alper-bozcal/75W_XDPS/ENKO/Canbus/DBC2 Canbus List.pdf

J1939-71

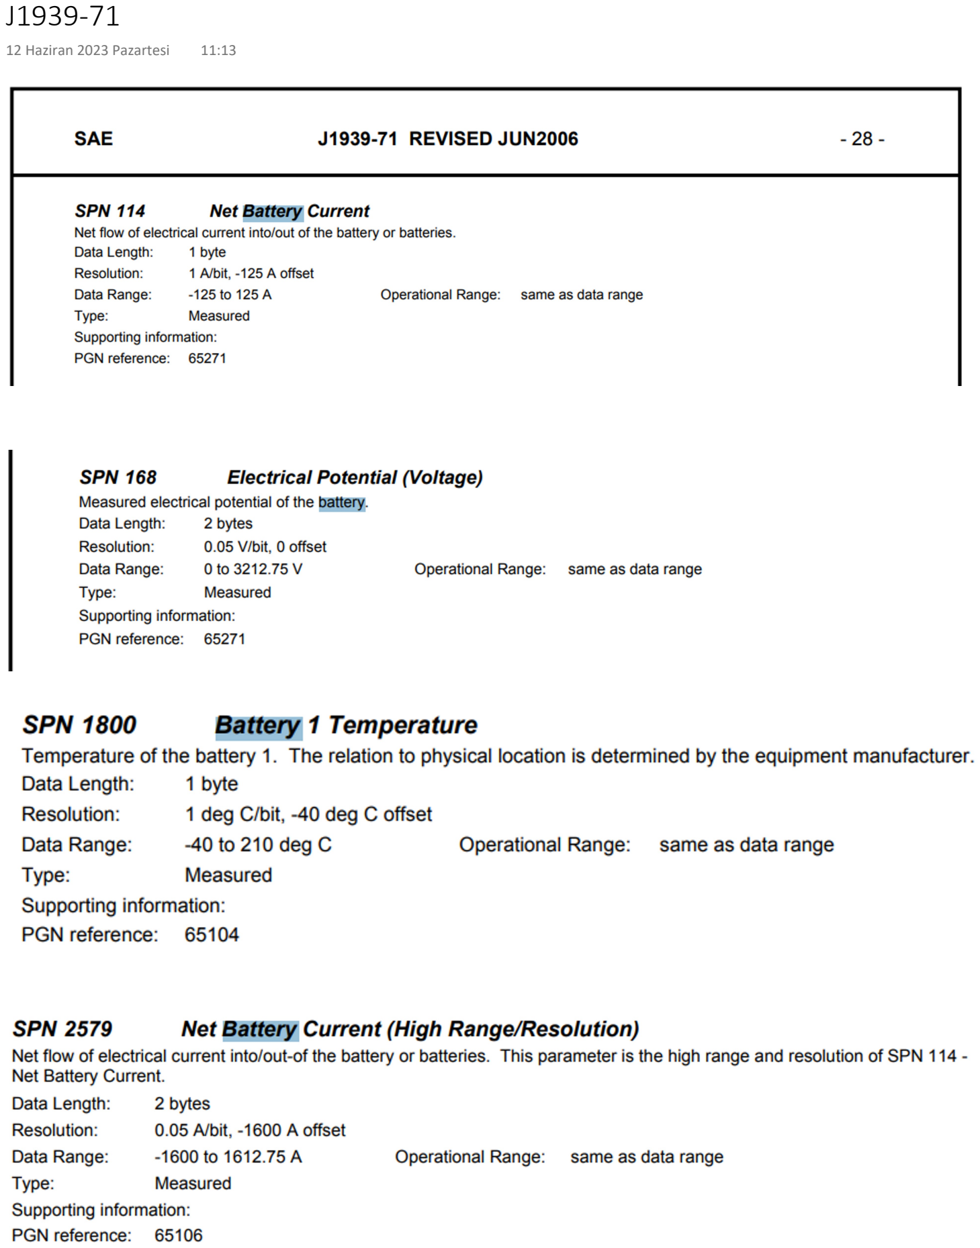
[picture p2: page 1]

### 12 Haziran 2023 Pazartesi 11:13

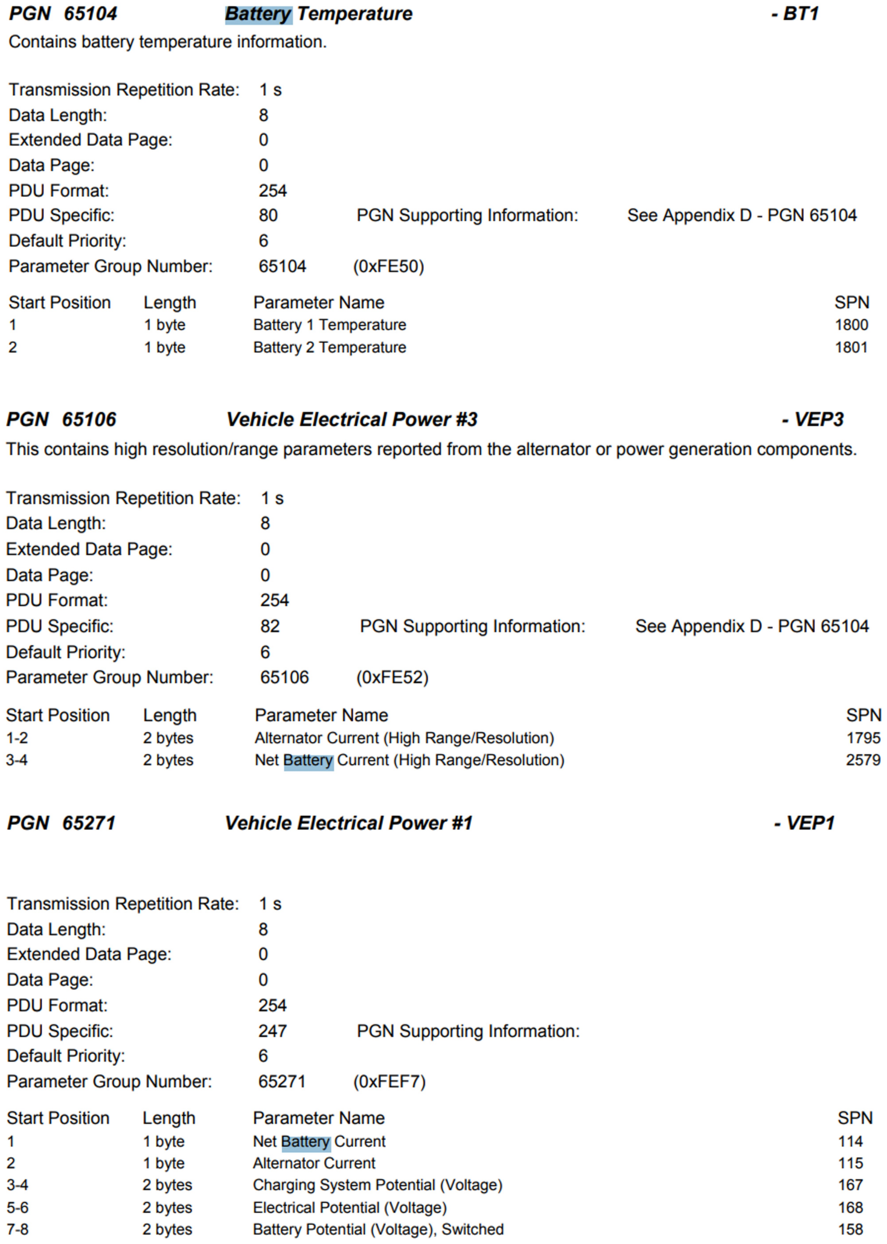
[picture p3: page 2]
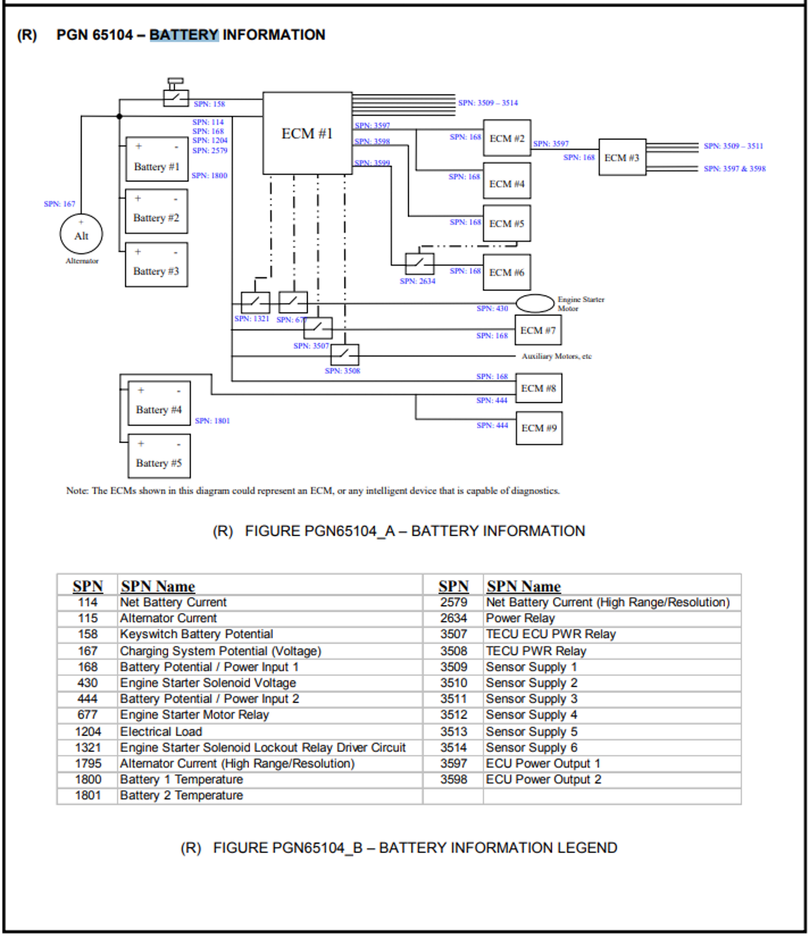
[picture p4: page 3]
