alper-bozcal/75W_XDPS/Design Docs/300W 894 Core Hesapları.PNG

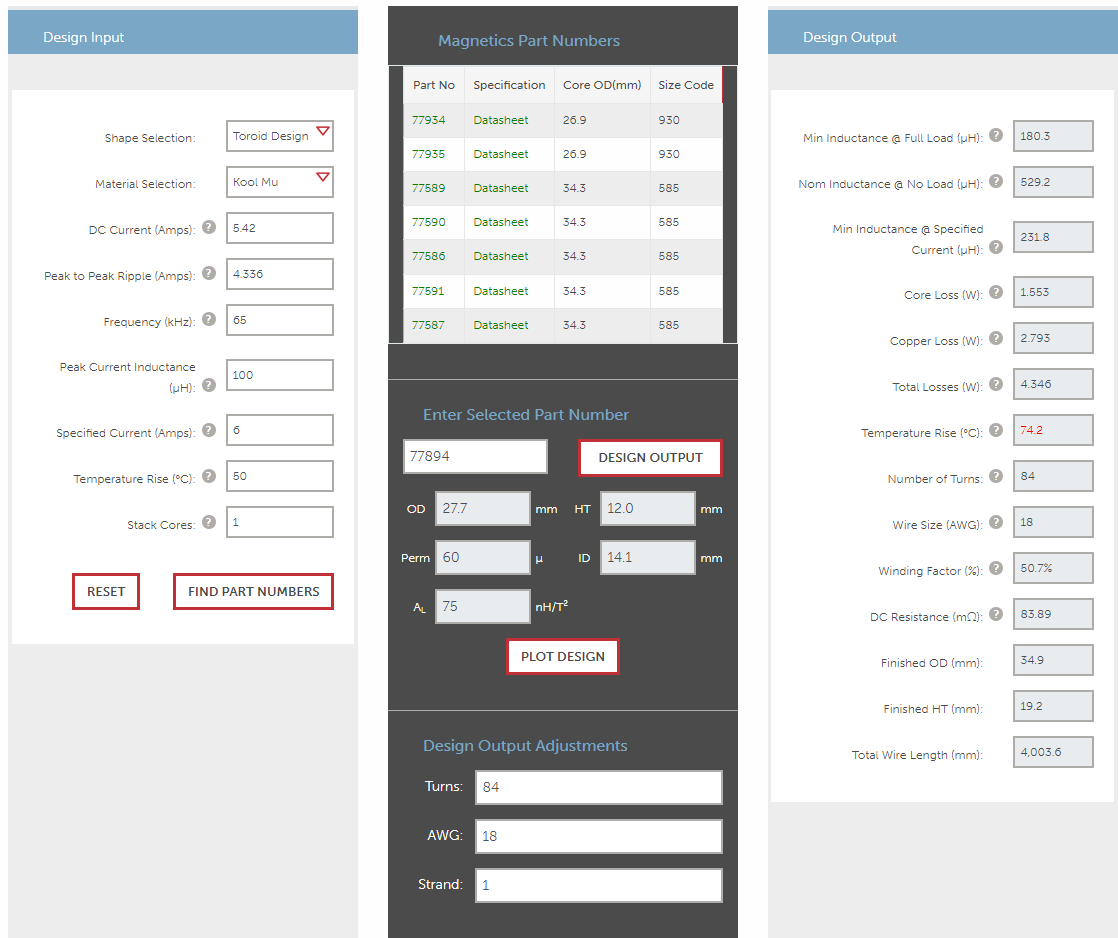
Design Docs/300W 894 Core Hesapları.PNG
