alper-bozcal/75W_XDPS/Design Docs/300W 77083 Bütün Sınırlara Uyan.PNG

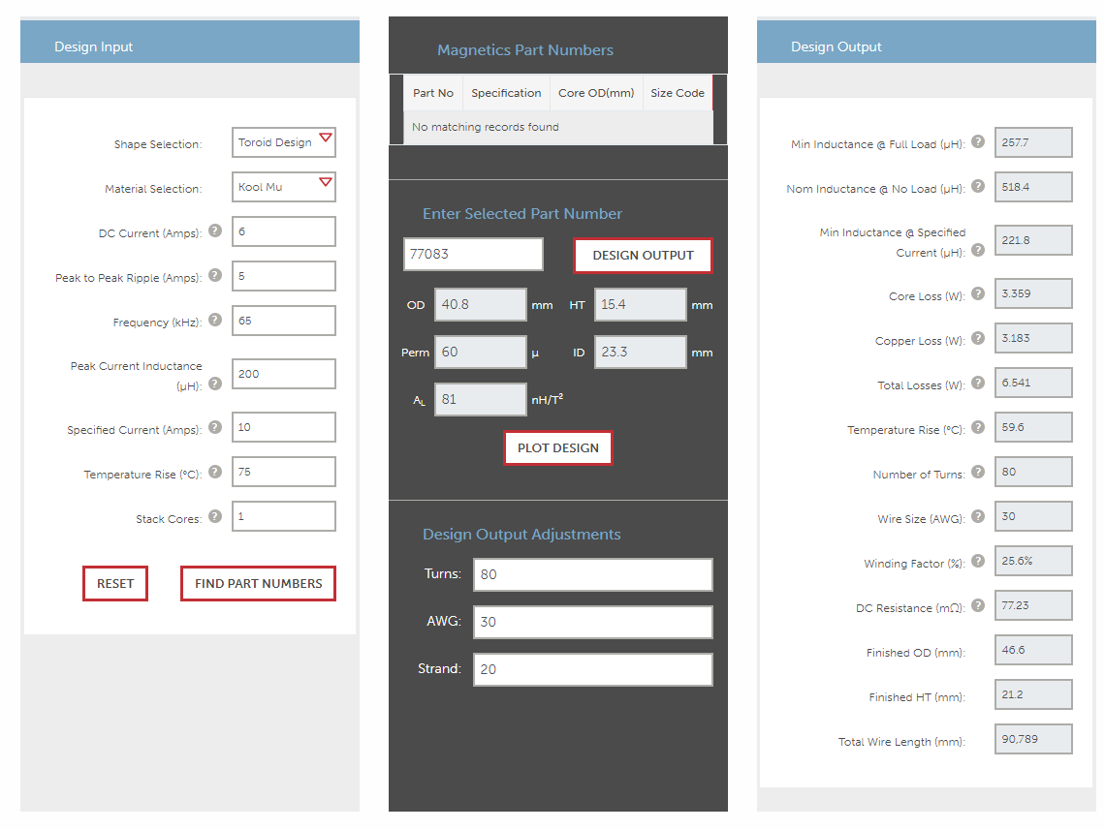
Design Docs/300W 77083 Bütün Sınırlara Uyan.PNG
