alper-bozcal/75W_XDPS/Simulations/Leakage/90W leakeage/90W-220VAC-LEAKAGE.PNG

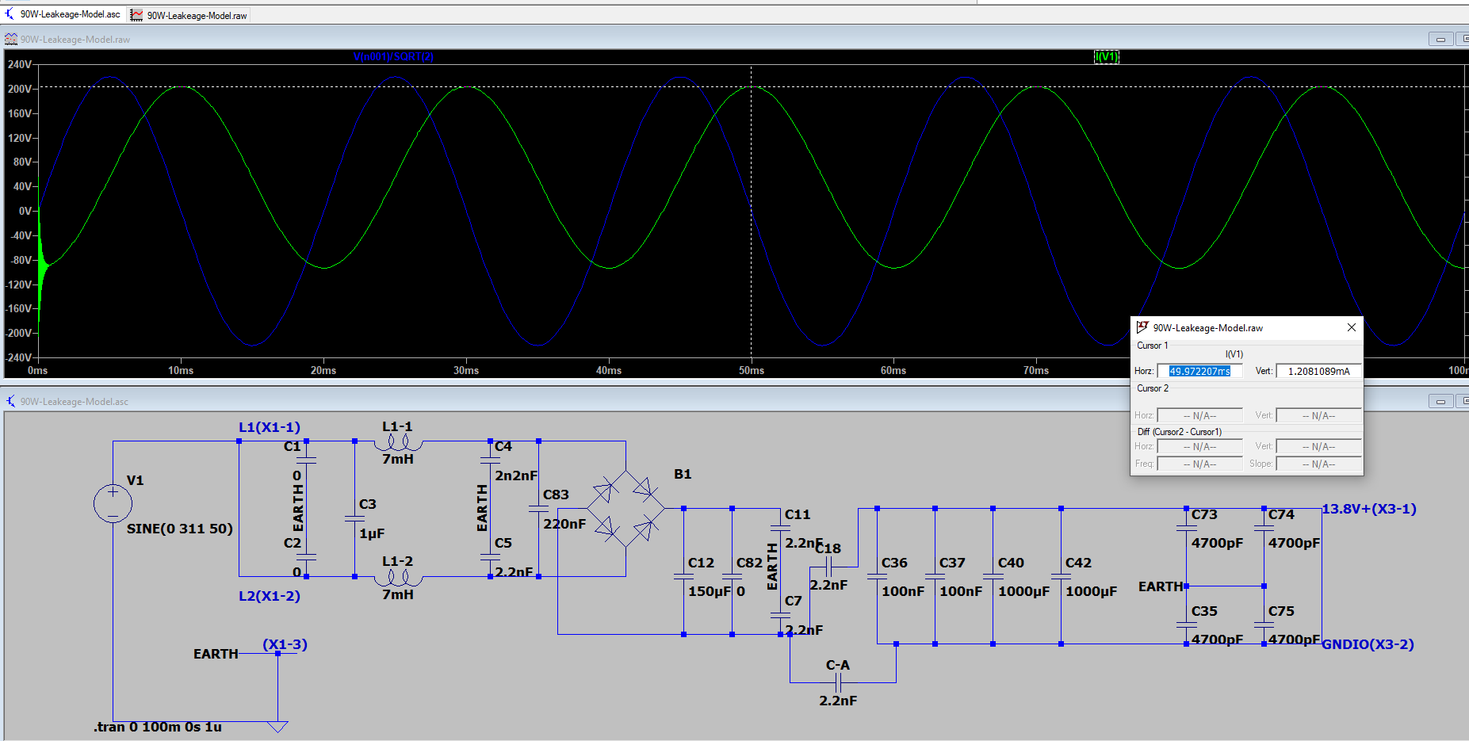
Simulations/Leakage/90W leakeage/90W-220VAC-LEAKAGE.PNG
