alper-bozcal/75W_XDPS/Simulations/Leakage/90W leakeage/90W-264VAC-LEAKAGE.PNG

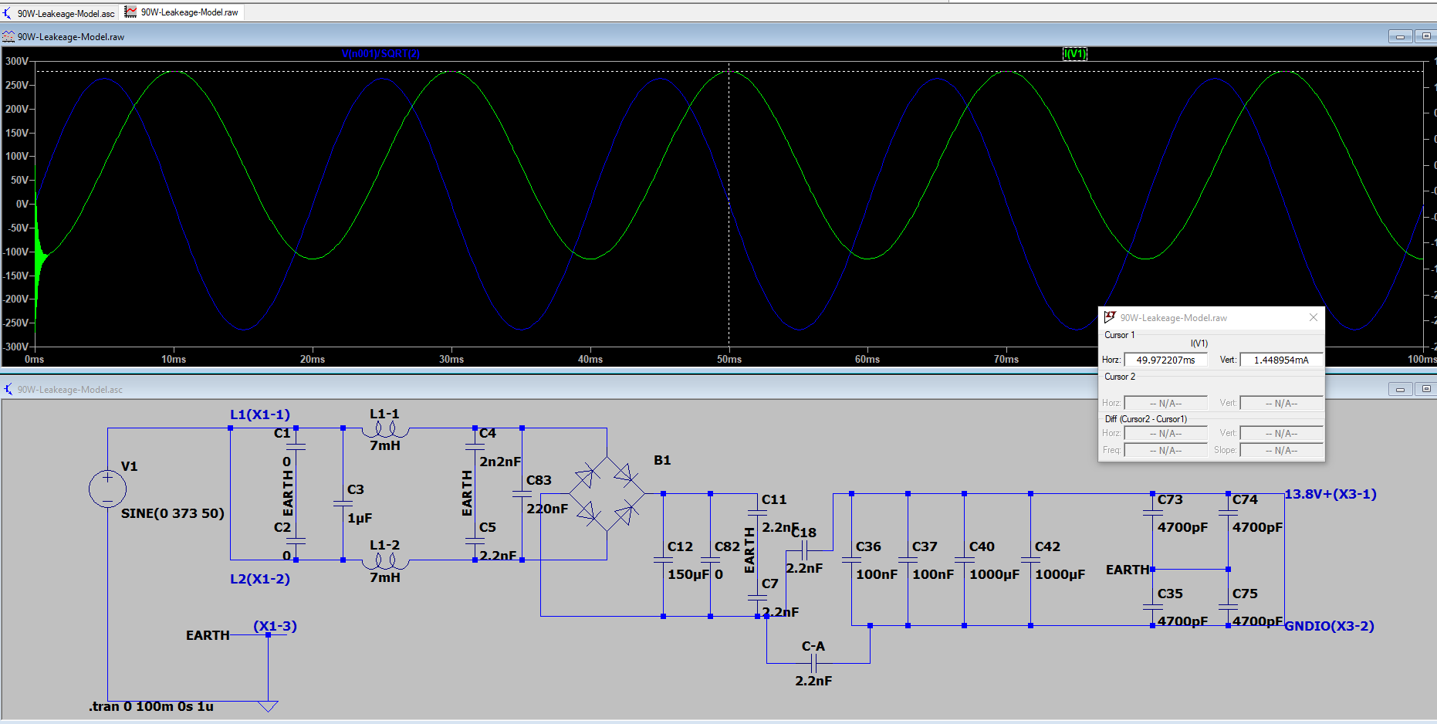
Simulations/Leakage/90W leakeage/90W-264VAC-LEAKAGE.PNG
