alper-bozcal/75W_XDPS/Simulations/Leakage/150W leakeage/150W-85VAC-Leakeage.PNG

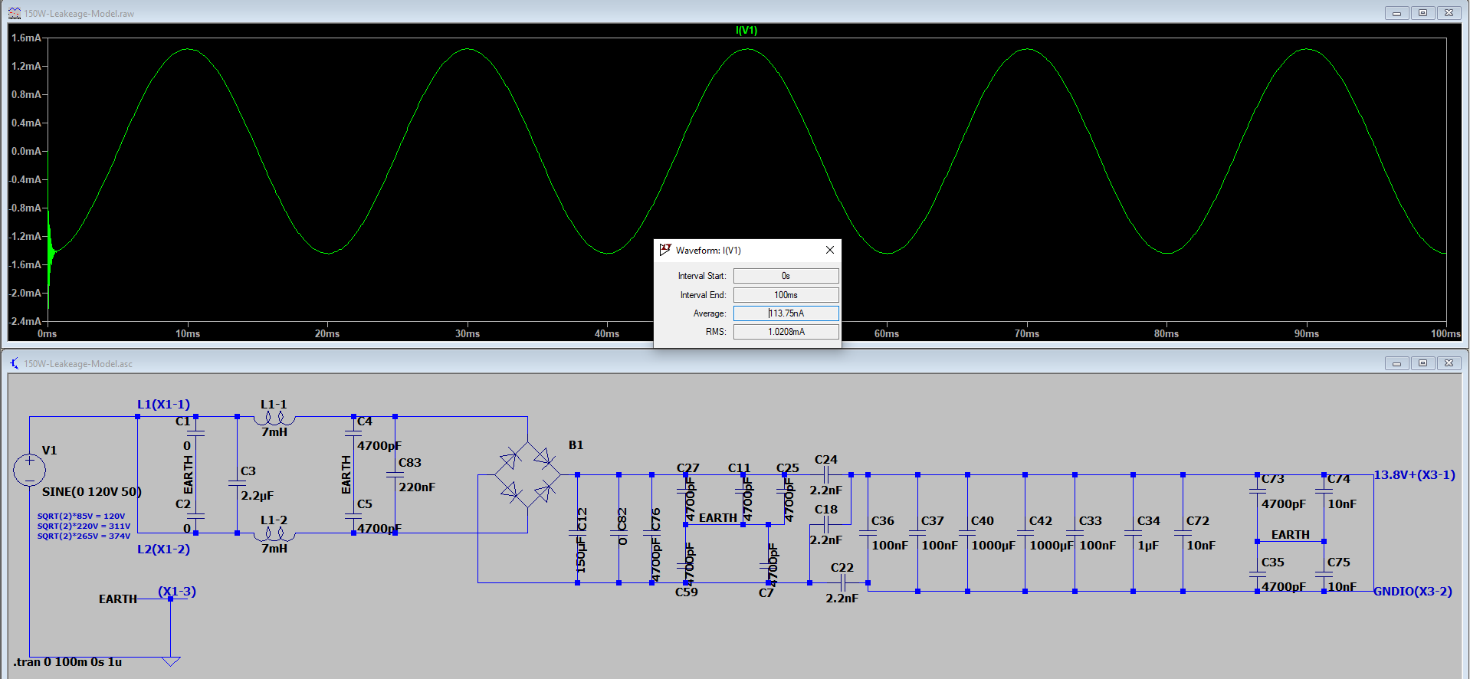
Simulations/Leakage/150W leakeage/150W-85VAC-Leakeage.PNG
