alper-bozcal/75W_XDPS/Simulations/Leakage/300W leakeage/300W 85VAC Leakeage.PNG

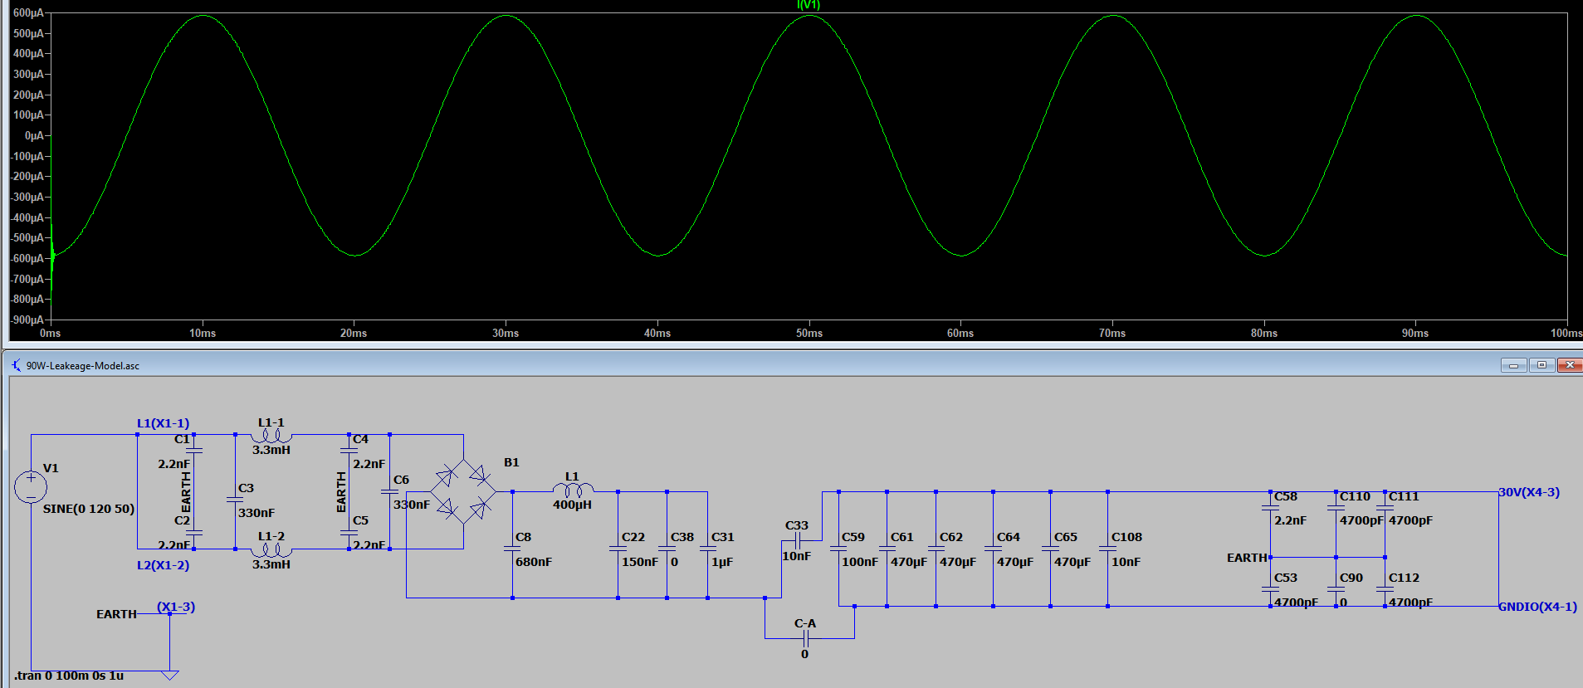
Simulations/Leakage/300W leakeage/300W 85VAC Leakeage.PNG
