alper-bozcal/75W_XDPS/Tests/EMC/2023 01 17 VESTEL/TEST18-2A_FULL.Rtf

TEST18-2A_FULL

Common Information
Test Description:
Test Site: | SAC3
Test Standard:
Environment Conditions:
Operator Name:
Comment:

Final_Result
Frequency (MHz) | QuasiPeak (dBµV/m) | Limit (dBµV/m) | Margin (dB) | Meas. Time (ms) | Bandwidth (kHz) | Height (cm) | Pol | Azimuth (deg)
30.570000 | 32.75 | 40.00 | 7.25 | 1000.0 | 120.000 | 100.0 | V | 165.0
40.260000 | 32.58 | 40.00 | 7.42 | 1000.0 | 120.000 | 100.0 | V | 18.0
44.760000 | 33.35 | 40.00 | 6.65 | 1000.0 | 120.000 | 100.0 | V | 120.0
74.940000 | 29.49 | 40.00 | 10.51 | 1000.0 | 120.000 | 160.0 | V | 225.0
222.360000 | 38.35 | 40.00 | 1.65 | 1000.0 | 120.000 | 100.0 | H | 114.0
223.650000 | 37.09 | 40.00 | 2.91 | 1000.0 | 120.000 | 105.0 | H | 103.0
Hardware Setup: EMI radiated\SAC3 Radiated Emission 30-6000 MHz - [EMI radiated] Subrange 1
| Frequency Range: | 30 MHz - 6 GHz
| Receiver: | ESW 44 [ESW 44]
| | @ GPIB0 (ADR 20), SN 1328.4100K45/103131, FW 2.10SP2
| Signal Path: | ESR 7-ETS-Lindgren 3142E
| | FW 1.0
| | Correction Table: EMI+ANTENNA_CABLE_30MHz-6GHz_26.08.2022
| Antenna: | ETS-Lindgren 3142E
| | Correction Table (vertical): ETS_LINDGREN_3142E_HORIZONTAL_18.08.2020
| | Correction Table (horizontal): ETS_LINDGREN_3142E_HORIZONTAL_18.08.2020
| Antenna Tower: | EMCO 2090 Antenna Tower [EMCO 2090 Antenna Tower]
| | @ GPIB0 (ADR 8), FW REV 3.21
| Turntable: | EMCO Turntable [EMCO Turntable]
| | @ GPIB0 (ADR 9), FW REV 3.21
EMI Auto Test Template: SAC3 EN 55032 CLASS B 30-1000 MHz TEST
Hardware Setup: | SAC3 Radiated Emission 30-6000 MHz
Measurement Type: | Open-Area-Test-Site
Frequency Range: | 30 MHz - 1 GHz
Graphics Level Range: | 0 dBµV/m - 80 dBµV/m
Preview Measurements:
| Graphics Display: | Show separate traces for horizontal and vertical polarization
| Scan Test Template: | SAC2 TV EN 55022 ITE Equipments Prescan
Adjustment:
| Template for Single Meas.: | SAC2 TV EN 55022 ITE Equipments Final Measurement
Final Measurements:
| Template for Single Meas.: | SAC2 TV EN 55022 ITE Equipments Final Measurement
