alper-bozcal/75W_XDPS/Tests/EMC/2023 05 23 Vestel RE CE Harmonics/DBC2 75W&150W VESTEL Tests.odt

DBC-2

75W & 150W

CONDUCTED – HARMONICS – RADIATED

Tests @Vestel

23.05.2023

Following tests hold for DBC 2 75W and 150W units accordingly. All images have labels to indicate which sample tested. For 150W tests ENKO Unit 150W-4 used. For 75W tests, ENKO Unit 1205-A used.

CONDUCTED EMISSIONS TESTS

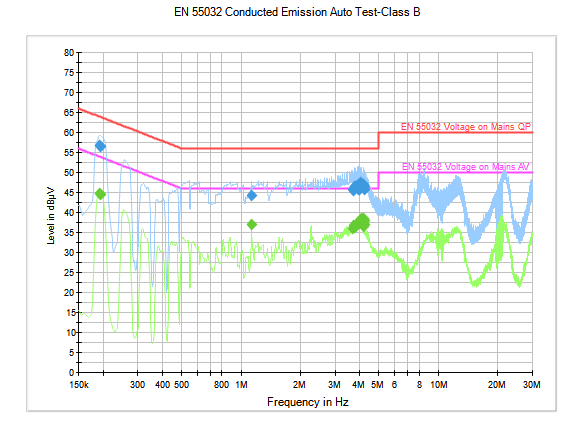
[picture p43: figure]

Image 1 – 150W-4 15VDC 10ADC Tests @Vestel

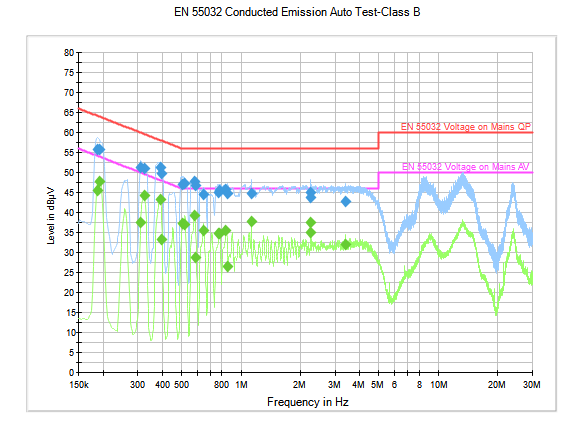
[picture p44: figure]

Image 2 - 150W-4 30VDC 5ADC Tests @Vestel

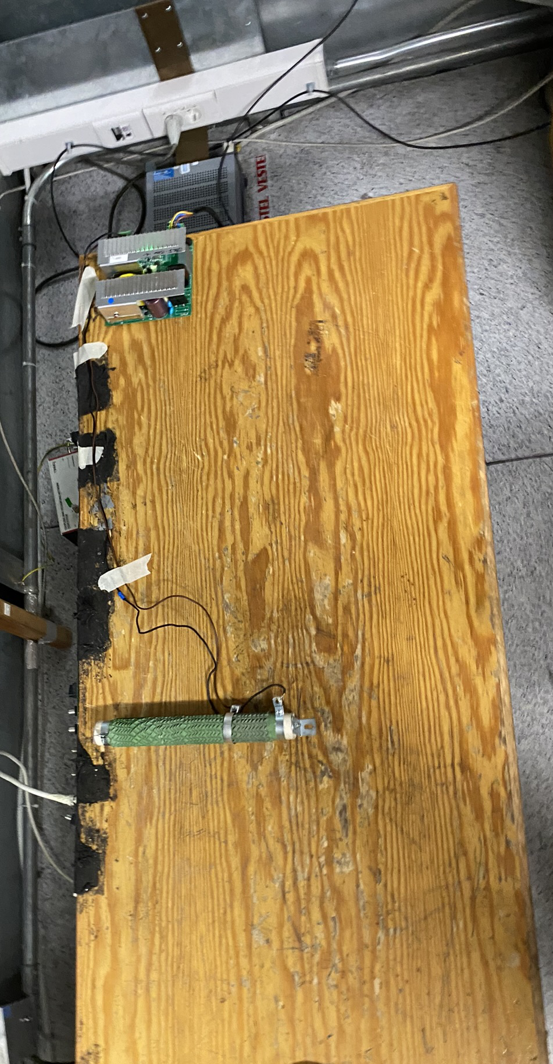
[picture p45: figure]

Image 3 – 150W-4 Conducted Test Setup @Vestel

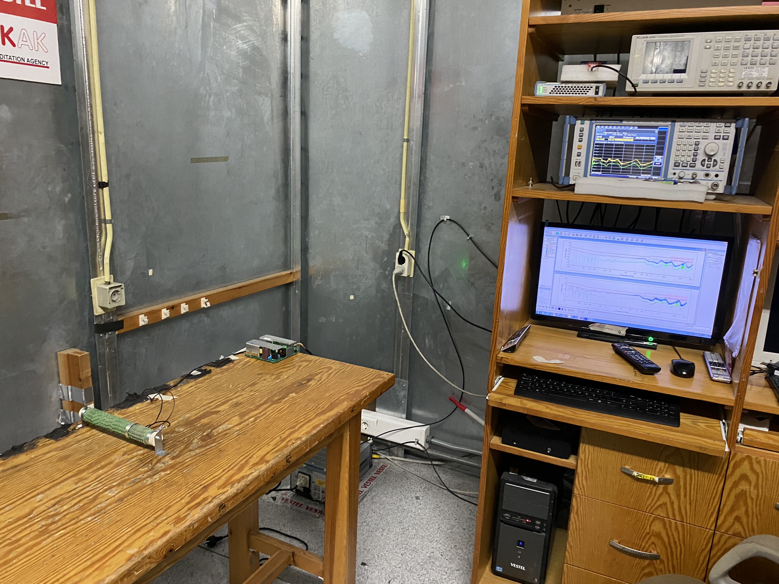
[picture p46: figure]

Image 4 – 150W-4 Conducted Test Setup @Vestel

Line Current Harmonics Tests

Harmonics tests at Vestel were according to standard: EN/IEC 61000-3-2 Ed.4 Long cyclic, Class A.

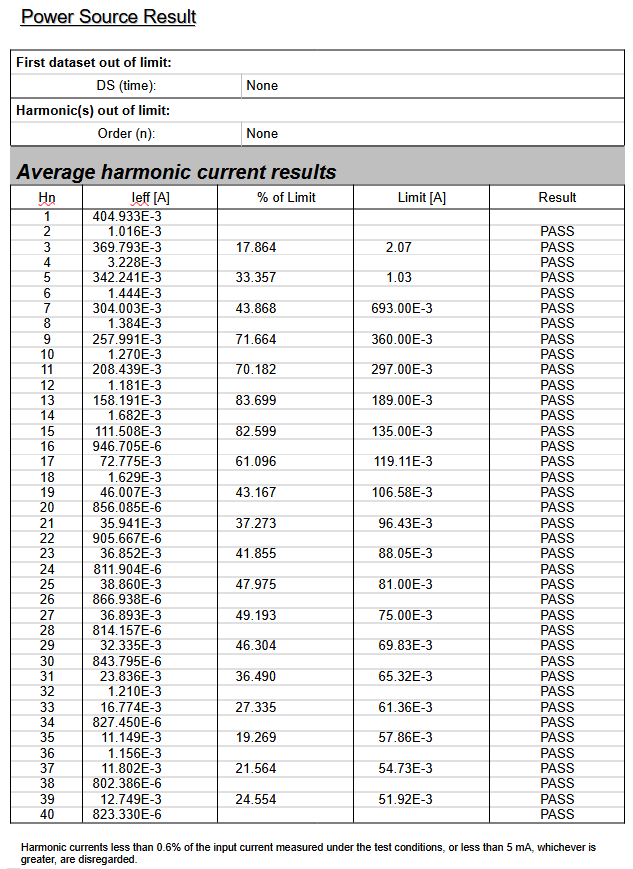
[picture p47: figure]

Image 5 – 1205-A 15VDC 05ADC Harmonics Test Average Results @Vestel

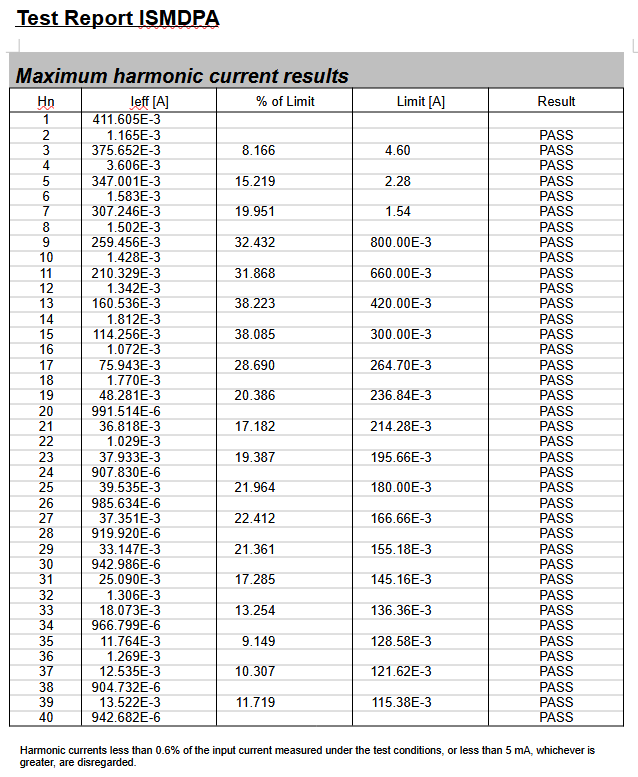
[picture p48: figure]

Image 6 – 1205-A 15VDC 05ADC Harmonics Test Maximum Results @Vestel

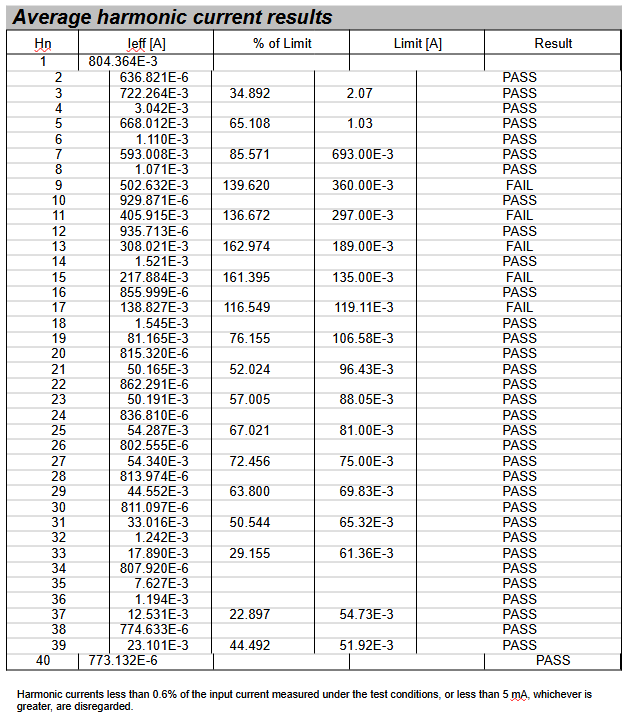
[picture p49: figure]

Image 7 – 150W-4 15VDC 10ADC Average Current Harmonics Test @Vestel

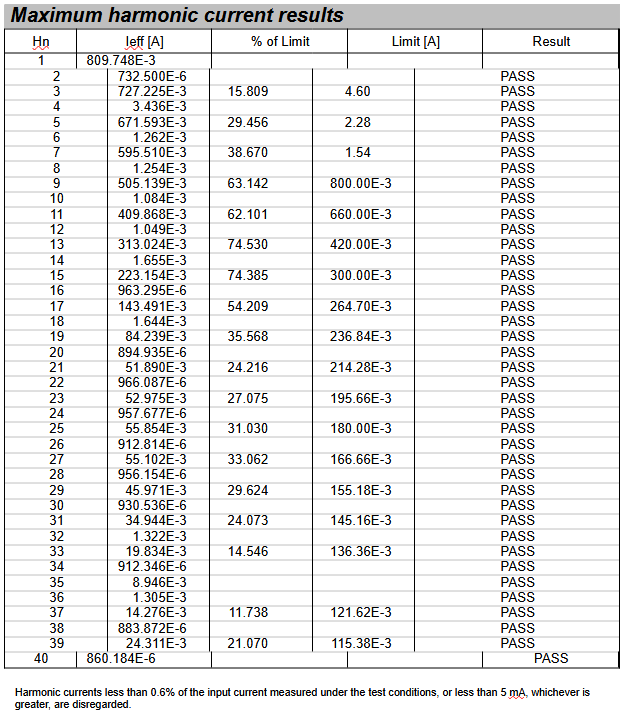
[picture p50: figure]

Image 8 – 150W-4 15VDC 10ADC Maximum Current Harmonics Test @Vestel

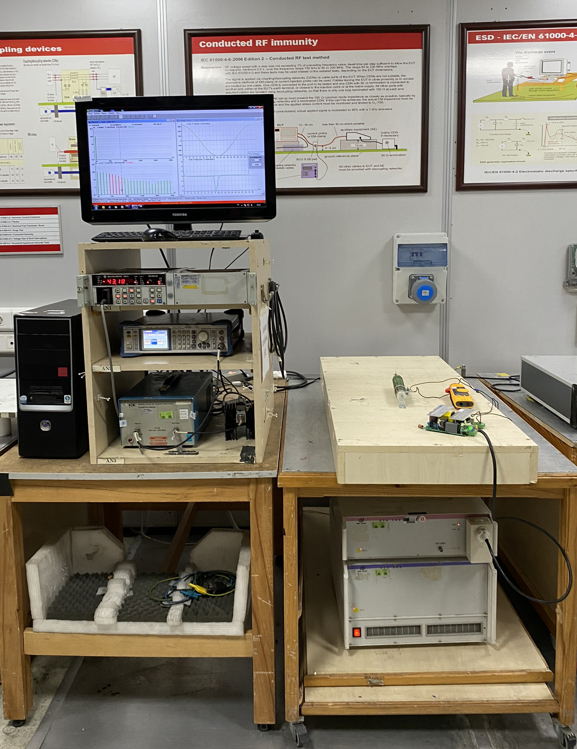
[picture p51: figure]

Image 9 – Harmonics Current Measurement Tests Setup @Vestel

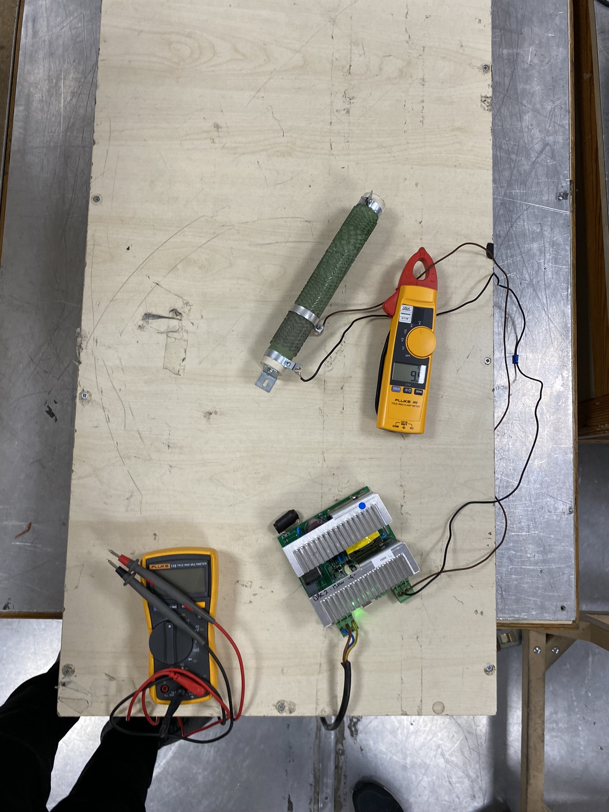
[picture p52: figure]

Image 10 - Harmonics Current Measurement Tests Setup @Vestel

Radiated Emissions Tests

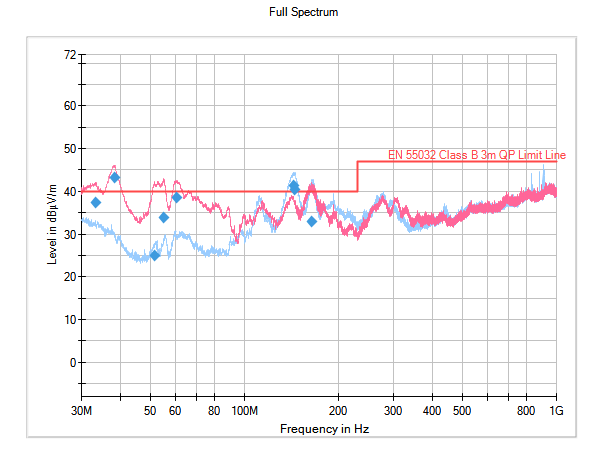
[picture p53: figure]

Image 11 – 150W-4 15VDC 10ADC T1 Radiated Test @Vestel

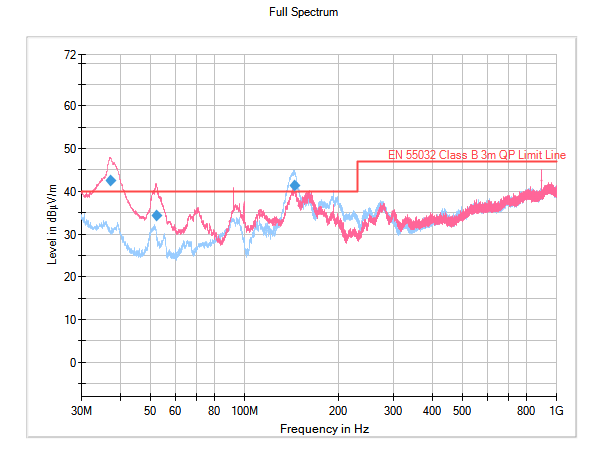
[picture p54: figure]

Image 12 – 150W-4 15VDC 10ADC T2 Radiated Test @Vestel

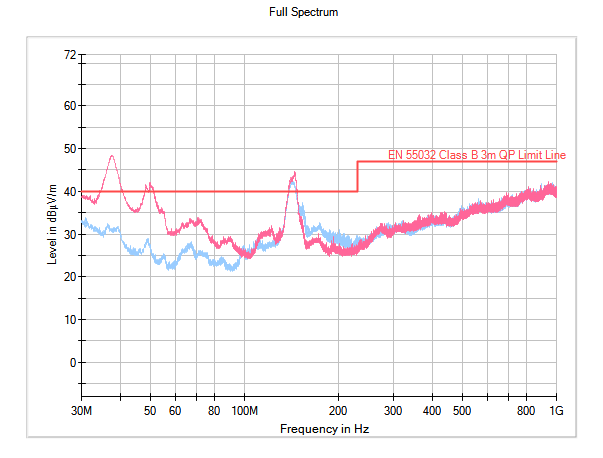
[picture p55: figure]

Image 13 – 150W-4 15VDC 10ADC T3 Radiated Test @Vestel

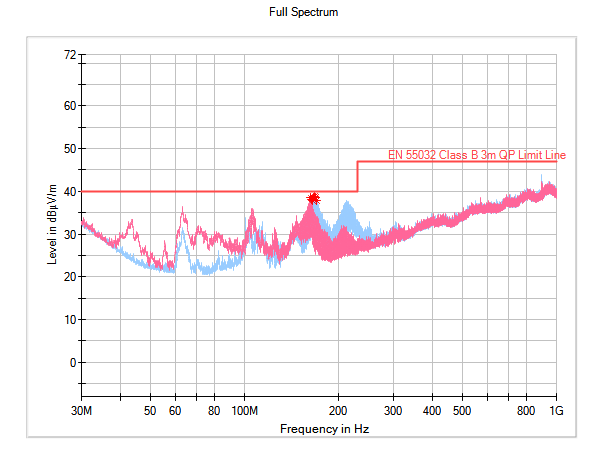
[picture p56: figure]

Image 14 – 150W-4 15VDC 10ADC T4 Radiated Test @Vestel

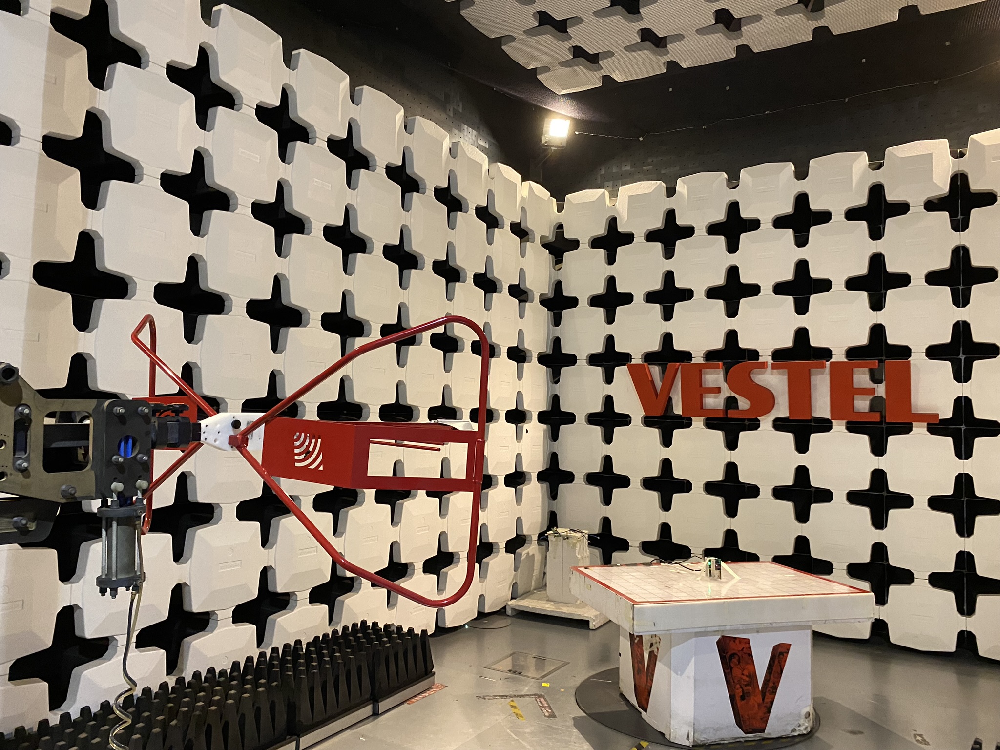
[picture p57: figure]

Image 15 – Radiated Tests Setup @Vestel

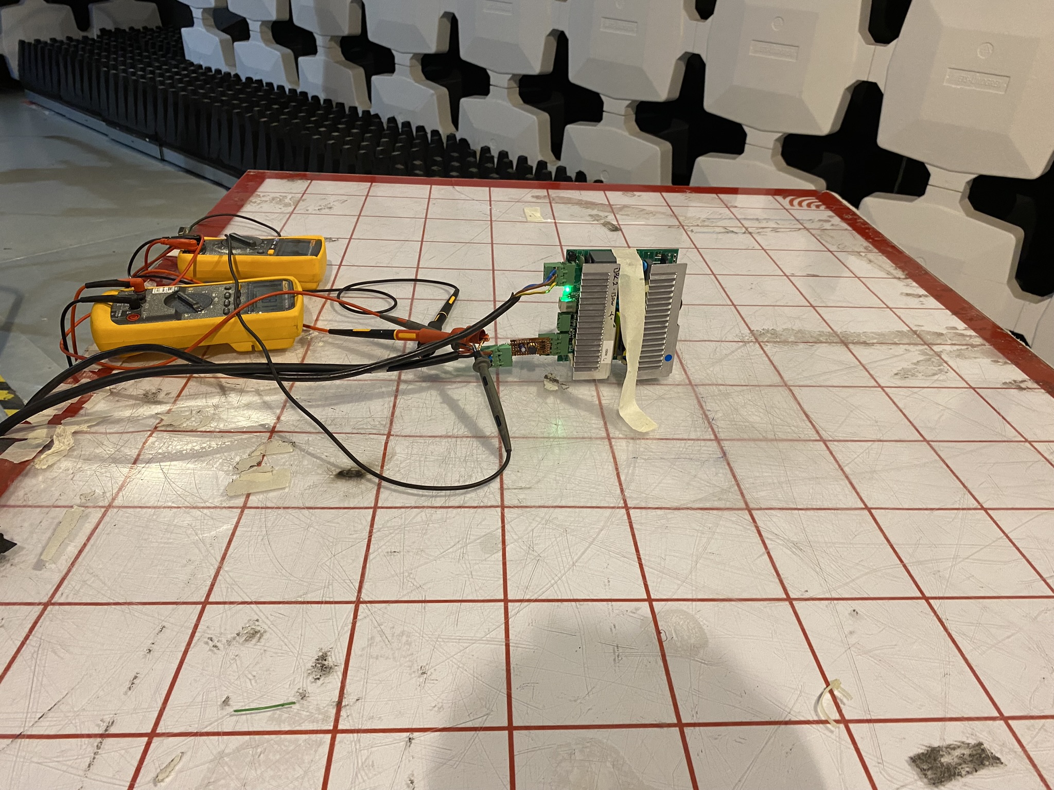
[picture p58: figure]

Image 16 – Radiated Tests Setup @Vestel

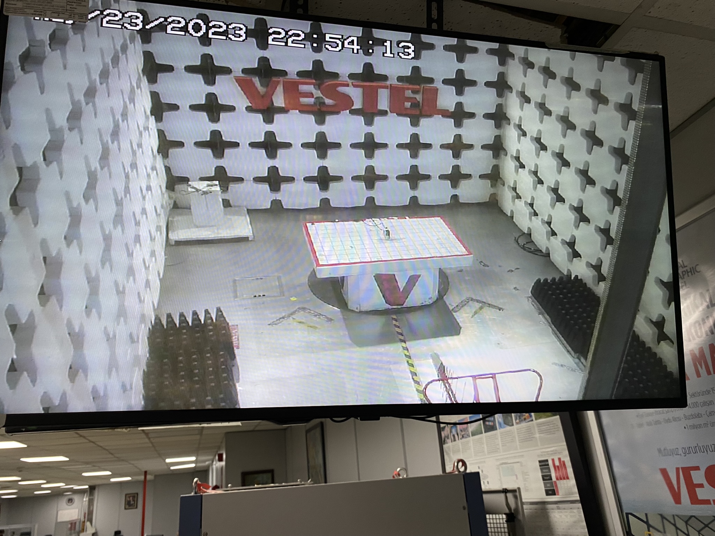
[picture p59: figure]

Image 17 – Radiated Tests Setup @Vestel

ENKO ELECTRONIC CONTROL SYSTEMS
