alper-bozcal/75W_XDPS/Tests/EMC/2023 05 23 Vestel RE CE Harmonics/Radiated Emission/Dbc2 1210-T1.Rtf

Dbc2 1210-T1

Common Information
Test Description:
Test Site: | SAC3
Test Standard:
Environment Conditions:
Operator Name:
Comment:

Final_Result
Frequency (MHz) | QuasiPeak (dBµV/m) | Limit (dBµV/m) | Margin (dB) | Meas. Time (ms) | Bandwidth (kHz) | Height (cm) | Pol | Azimuth (deg)
33.240000 | 37.49 | 40.00 | 2.51 | 1000.0 | 120.000 | 100.0 | V | 180.0
38.400000 | 43.31 | 40.00 | -3.31 | 1000.0 | 120.000 | 100.0 | V | 0.0
51.330000 | 25.09 | 40.00 | 14.91 | 1000.0 | 120.000 | 105.0 | V | 180.0
54.930000 | 33.97 | 40.00 | 6.03 | 1000.0 | 120.000 | 153.0 | V | 45.0
60.300000 | 38.47 | 40.00 | 1.53 | 1000.0 | 120.000 | 100.0 | V | 0.0
143.670000 | 41.41 | 40.00 | -1.41 | 1000.0 | 120.000 | 176.0 | H | 270.0
144.600000 | 40.31 | 40.00 | -0.31 | 1000.0 | 120.000 | 152.0 | H | 135.0
164.400000 | 32.84 | 40.00 | 7.16 | 1000.0 | 120.000 | 175.0 | H | 315.0
Hardware Setup: EMI radiated\SAC3 Radiated Emission 30-6000 MHz - [EMI radiated] Subrange 1
| Frequency Range: | 30 MHz - 6 GHz
| Receiver: | ESW 44 [ESW 44]
| | @ GPIB0 (ADR 20), SN 1328.4100K45/103131, FW 2.10SP2
| Signal Path: | ESR 7-ETS-Lindgren 3142E
| | FW 1.0
| | Correction Table: EMI+ANTENNA_CABLE_30MHz-6GHz_26.08.2022
| Antenna: | ETS-Lindgren 3142E
| | Correction Table (vertical): ETS_LINDGREN_3142E_HORIZONTAL_18.08.2020_KONTROL_24.01.2023
| | Correction Table (horizontal): ETS_LINDGREN_3142E_HORIZONTAL_18.08.2020_KONTROL_24.01.2023
| Antenna Tower: | EMCO 2090 Antenna Tower [EMCO 2090 Antenna Tower]
| | @ GPIB0 (ADR 8), FW REV 3.21
| Turntable: | EMCO Turntable [EMCO Turntable]
| | @ GPIB0 (ADR 9), FW REV 3.21
EMI Auto Test Template: SAC3 EN 55032 CLASS B 30-1000 MHz TEST
Hardware Setup: | SAC3 Radiated Emission 30-6000 MHz
Measurement Type: | Open-Area-Test-Site
Frequency Range: | 30 MHz - 1 GHz
Graphics Level Range: | 0 dBµV/m - 80 dBµV/m
Preview Measurements:
| Graphics Display: | Show separate traces for horizontal and vertical polarization
| Scan Test Template: | SAC2 TV EN 55022 ITE Equipments Prescan
Adjustment:
| Template for Single Meas.: | SAC2 TV EN 55022 ITE Equipments Final Measurement
Final Measurements:
| Template for Single Meas.: | SAC2 TV EN 55022 ITE Equipments Final Measurement
