alper-bozcal/75W_XDPS/Tests/EMC/2023 04 29 Numune Gönderimi/DBC2-150W-7-1510.pdf

# DBC2

19.04.2023 16:02:30

### 1 / 1 - Page 1 of 2

Heading | DBC2-150W-7-1510

## Meas Type Equipment under Test DBC2

Manufacturer | ENKO
OP Condition | p
Operator | C.U.
Test Spec | J

## Settings

Scan Start | 150.000000000 kHz
Scan Stop | 30.000000000 MHz
RBW | 9.0 kHz
IF RBW | 10.0 kHz
Meas Time | 1.0 s
RF Att | 10.0 dB
Preamp State | Off
Preamp Value | 0.0 dB
Input Selection | INP1
Input Coupling | AC
Scan Type | TD Scan
Transducer | ENV432 ENKO.TDF

## Scan Table

Scan Start | 150.000000000 kHz
Scan Stop | 30.000000000 MHz
Scan Type | TD Scan
Transducer | ENV432 ENKO.TDF
Detector | Trace 1: Max Peak Trace 2: Average
Start
Frequency

Stop
Frequency
Step Size | RBW | Meas Time | RF Atten | Preamp | Input
150.000 kHz | 30.000 MHz | 2.250 kHz | 9.0 kHz | 10.0 ms 10.0 dB 0.0 dB INPUT1

## Peak List

Margin | 6.0 dB
Peaks | 25
Trace | Frequency | Level (dBµV) | Phase | Detector | Delta Limit/dB
1 186.000000000 kHz | 59.29 | L1 Positive Peak | -4.92
1 | 3.358500000 MHz | 50.55 | L1 Positive Peak | -5.45
2 | 13.002000000 MHz | 44.09 | L1 | Average | -5.91
1 | 13.384500000 MHz | 56.01 | L1 Positive Peak | -3.99
1 | 16.836000000 MHz | 57.40 | L1 Positive Peak | -2.60
2 | 17.009250000 MHz | 44.44 | N | Average | -5.56

## Final Results

Meas Time | 1.0 s
Margin | 6.0 dB
Peaks | 25
Trace | Frequency | Level (dBµV) | Phase | Detector | Delta Limit/dB
1 186.000000000 kHz | 57.42 | L1 | Quasi Peak | -6.79
1 | 3.358500000 MHz | 45.27 | L1 | Quasi Peak | -10.73
2 | 13.002000000 MHz | 42.95 | L1 | CISPR AV | -7.05
1 | 13.384500000 MHz | 49.52 | L1 | Quasi Peak | -10.48
1 | 16.836000000 MHz | 51.17 | N | Quasi Peak | -8.83
2 | 17.009250000 MHz | 43.87 | N | CISPR AV | -6.13

19.04.2023 16:02:30
Heading | DBC2-150W-7-1510

## Meas Type Equipment under Test DBC2

Manufacturer | ENKO
OP Condition | p
Operator | C.U.
Test Spec | J

### 1 / 1 - Page 2 of 2

## Scan Diagram

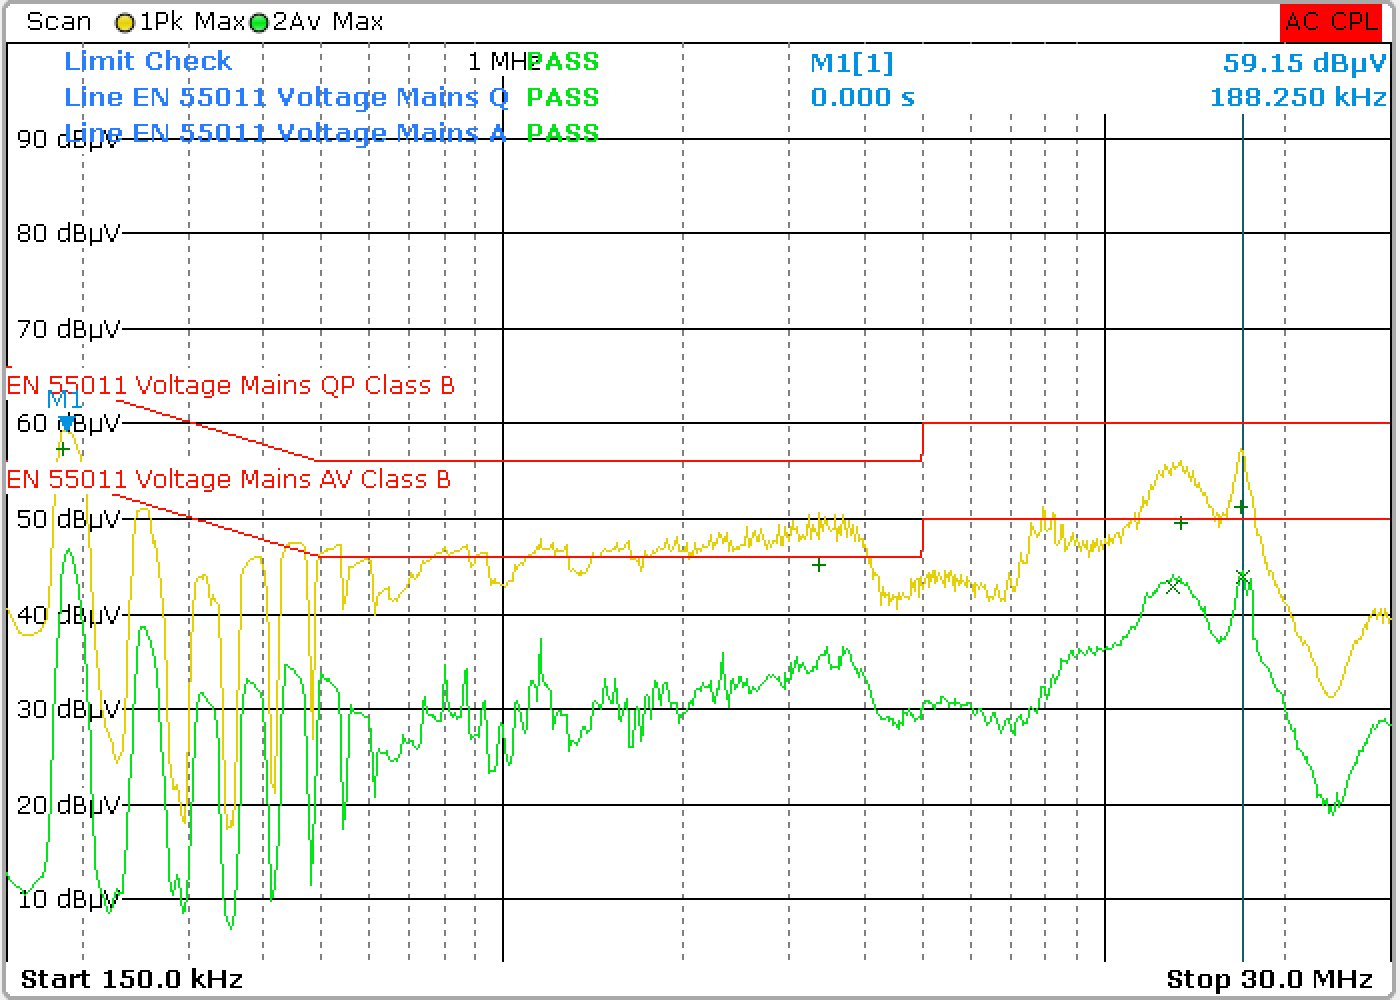
[picture p76: figure]
