alper-bozcal/75W_XDPS/Tests/EMC/2022 11 21 Conducted/2405/dbc-2 2405 V15.pdf

# DBC-2

21.11.2022 16:21:16

1 / 1 - Page 1 of 2

Heading | dbc-2 2405 V14
Meas Type
Equipment under Test
Manufacturer | enko
OP Condition | p
Operator | g.aktas
Test Spec | J
Settings
Scan Start | 150.000000000 kHz
Scan Stop | 30.000000000 MHz
RBW | 9.0 kHz
IF RBW | 10.0 kHz
Meas Time | 1.0 s
RF Att | 10.0 dB
Preamp State | Off
Preamp Value | 0.0 dB
Input Selection | INP1
Input Coupling | AC
Scan Type | TD Scan
Transducer | ENV432 ENKO.TDF
Scan Table
Scan Start | 150.000000000 kHz
Scan Stop | 30.000000000 MHz
Scan Type | TD Scan
Transducer | ENV432 ENKO.TDF
Detector | Trace 1: Max Peak Trace 2: Average
Start
Frequency

Stop
Frequency
Step Size | RBW | Meas Time | RF Atten | Preamp | Input
150.000 kHz | 30.000 MHz | 2.250 kHz | 9.0 kHz 100.0 ms 10.0 dB 0.0 dB INPUT1
Peak List
Margin | 6.0 dB
Peaks | 25
Trace | Frequency | Level (dBµV) | Phase | Detector | Delta Limit/dB
1 | 20.622750000 MHz | 55.20 | L1 Positive Peak | -4.80
1 | 29.942250000 MHz | 56.05 | L1 Positive Peak | -3.95
2 | 29.991750000 MHz | 45.11 | L1 | Average | -4.89
Final Results
Meas Time | 1.0 s
Margin | 6.0 dB
Peaks | 25
Trace | Frequency | Level (dBµV) | Phase | Detector | Delta Limit/dB
1 | 20.622750000 MHz | 50.75 | L1 | Quasi Peak | -9.25
1 | 29.942250000 MHz | 51.01 | L1 | Quasi Peak | -8.99
2 | 29.991750000 MHz | 44.92 | L1 | CISPR AV | -5.08

21.11.2022 16:21:16
Heading | dbc-2 2405 V14
Meas Type
Equipment under Test
Manufacturer | enko
OP Condition | p
Operator | g.aktas
Test Spec | J

1 / 1 - Page 2 of 2

Scan Diagram

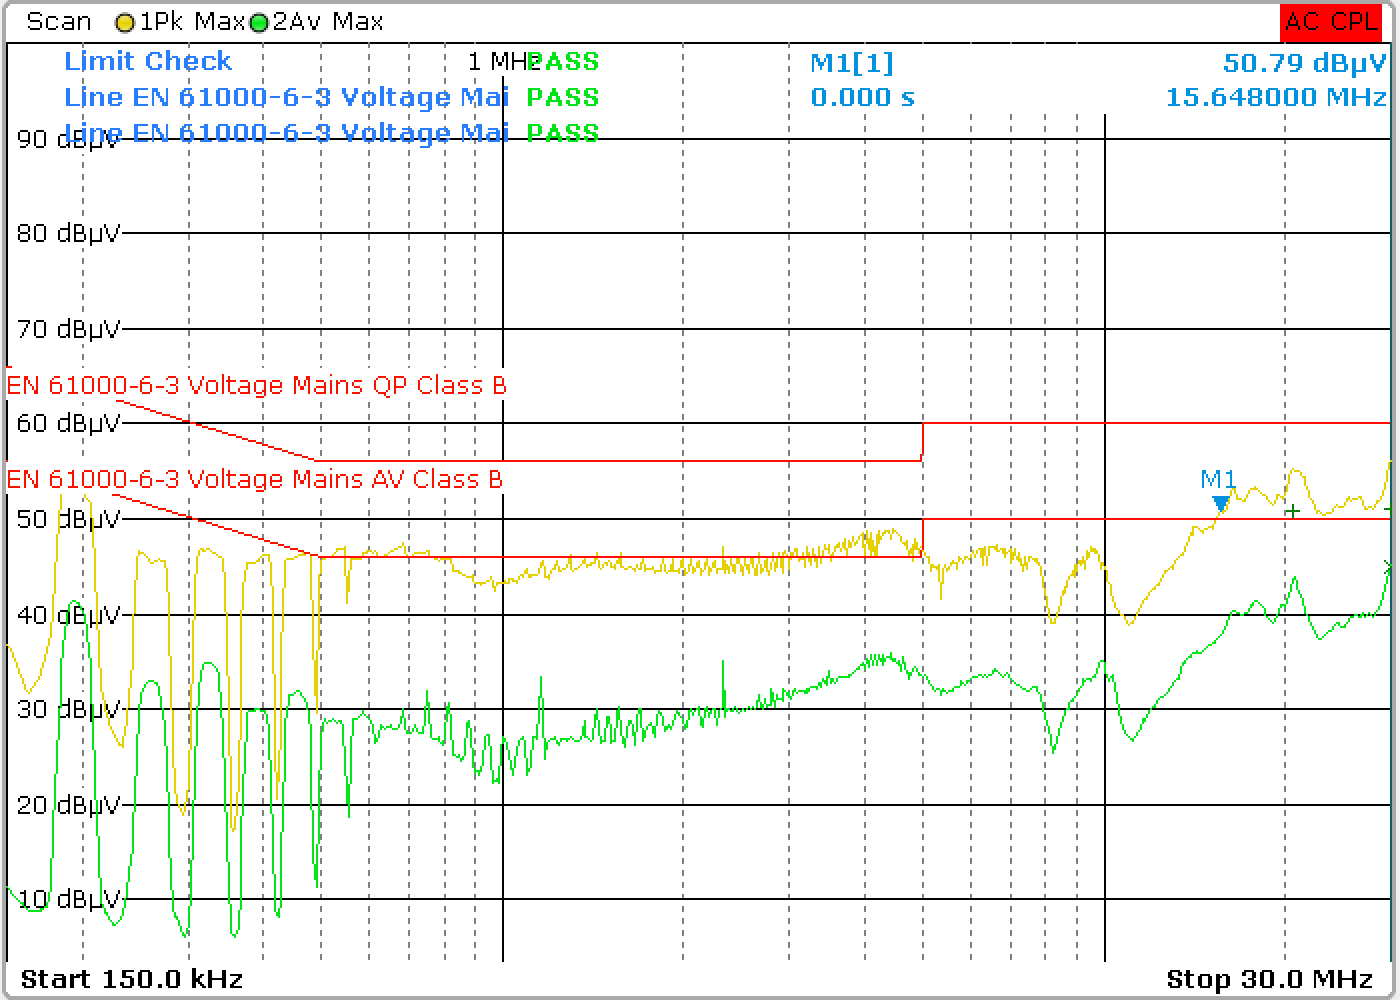
[picture p77: figure]
