alper-bozcal/75W_XDPS/Tests/EMC/Scope Denemeleri/osiloskop ölçümleri.xlsx

Sheet: Sheet1 (3)
 |  | 2022-12-29 | 2023-01-02 | 2023-01-03
Çıkış kablosu ile PE arası
Sekonder senkron mosfet darin source
D1 anot katot
Sekonder Vsupply-GNDA
Sekonder Vsupply-PE
Primer mosfet gate-source
VAUX_PRI
D6 anot katot
Sekonder senkron mosfet gate source
Sekonder senkron mosfet gate drain
Primer mosfet drain source
 | ilk durum |  | primer aux diyotuna snubber eklendi | Sekonder senkron mosfet snubber 3.3nF + 9.4 ohm

Sheet: Sheet1 (2)
 | 2022-12-29 | 2023-01-02 | 2023-01-03
Çıkış kablosu ile PE arası
Sekonder senkron mosfet darin source
D1 anot katot
Sekonder Vsupply-GNDA
Sekonder Vsupply-PE
Primer mosfet gate-source
VAUX_PRI
D6 anot katot
Sekonder senkron mosfet gate source
Sekonder senkron mosfet gate drain
Primer mosfet drain source

Sheet: Sheet1
 | 2022-12-29 | 2023-01-02 | 2023-01-03
Çıkış kablosu ile PE arası
Sekonder senkron mosfet darin source
D1 anot katot
Sekonder Vsupply-GNDA
Sekonder Vsupply-PE
Primer mosfet gate-source
VAUX_PRI
D6 anot katot
Sekonder senkron mosfet gate source
Sekonder senkron mosfet gate drain
Primer mosfet drain source
