alper-bozcal/75W_XDPS/Tests/Harmonik/Harmonik 31 Ekim 90W/DBC2 75W Testler-ENKO.xlsx

Sheet: TESTLER
1- | TEST1 sayfasındaki koşullar oluşturularak test yapılır. Sonuçlar bu sayfaya kayıt edilir.
2- | PC arayüzden min.12V ve maksimum 30V değerine set edilebilir olmalıdır. Kontrol edilir.
3- | Output reverse polarity protection test (TEST3)
4- | Akım harmonikleri ölçümü TEST4
4- | Cold start test
5- | Max. ambient temperature test on maximum output power (thermal kamera ile test, thermocouple ile test)
6- | Leakage Current. Leakage current için devre eş değer şeması çizilir. Leakage akım hesaplanır. 220VAC ve 264VAc için ölçülür.
 | Humidity test
 | Output power derating test
 | Alarm conditions and alarm relay test
 | Battery temperature measurement tests
 | Boost charge test
 | Parallel connection test
 | Vibration
 | Sparking (Cihaz enerjisiz ve çıkış kondansatörleri boşalmışken akü bağlantısı yapılır bu sırada ark oluşmamalıdır.)
 | In-rush current value (Cihaz enerjisiz ve çıkış kondansötörleri boşalmışken çıkış tam yük ve boş durumları için akım akım probu ile osiloskopta giriş akımı ölçülür.)
 | Input-output Hi-Pot test (with terminals shorted)
 | Input-Earth isolation test
 | Output-Earth isolation test
 | Case-Earth ESD test, 8kV max. (not applicable with 3D enclosure)
 | EMC test:
 | Input current harmonics level measurement
 | Conducted EMC
 | Radiated EMC
 | Burst-surge test (to be tested at final stage)
 | Noise immunity test
 | Failure Mode Analysis
 | Load Dump Test
 |  | 7-

Sheet: TEST1
INPUT |  |  |  |  | OUTPUT |  |  |  | Verim | Ripple | Start-up | Start-up with 10x10.000uF | Notlar
Vin (VAC) |  | Fr (Hz) |  | Pin (watt) | Vout(DC) |  | Iout(A) |  | Çıkış Gücü/Giriş Gücü | Çıkışta sadece direnç yükü varken ölçüm yapılır. | Beliritlen koşulda giriş gerilimini kes ve ver. Problemsiz olarak çıkış geriliminin yada akımının oluştuğunu gör. | Beliritlen koşulda giriş gerilimini kes ve ver. Problemsiz olarak çıkış geriliminin yada akımının oluştuğunu gör.
İstenen | Ölçülen | İstenen | Ölçülen |  | İstenen | Ölçülen | İstenen | Ölçülen | % | mVDC
85VAC |  | 60Hz |  |  | 12VDC |  | NO LOAD
85VAC |  | 60Hz |  |  | 12VDC |  | 0,5A
85VAC |  | 60Hz |  |  | 12VDC |  | 1A
85VAC |  | 60Hz |  |  | 12VDC |  | 4A
85VAC |  | 60Hz |  |  | 12VDC |  | 5A
85VAC |  | 60Hz |  |  | 12VDC |  | SHORT
85VAC |  | 60Hz |  |  | 13,8VDC |  | NO LOAD
85VAC |  | 60Hz |  |  | 13,8VDC |  | 0,5A
85VAC |  | 60Hz |  |  | 13,8VDC |  | 1A
85VAC |  | 60Hz |  |  | 13,8VDC |  | 4A
85VAC |  | 60Hz |  |  | 13,8VDC |  | 5A
85VAC |  | 60Hz |  |  | 13,8VDC |  | SHORT
85VAC |  | 60Hz |  |  | 14,5VDC |  | NO LOAD
85VAC |  | 60Hz |  |  | 14,5VDC |  | 0,5A
85VAC |  | 60Hz |  |  | 14,5VDC |  | 1A
85VAC |  | 60Hz |  |  | 14,5VDC |  | 4A
85VAC |  | 60Hz |  |  | 14,5VDC |  | 5A
85VAC |  | 60Hz |  |  | 14,5VDC |  | SHORT
85VAC |  | 60Hz |  |  | 15VDC |  | NO LOAD
85VAC |  | 60Hz |  |  | 15VDC |  | 0,5A
85VAC |  | 60Hz |  |  | 15VDC |  | 1A
85VAC |  | 60Hz |  |  | 15VDC |  | 4A
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
300VAC |  | 50Hz |  |  | 14,5VDC |  | SHORT
300VAC |  | 50Hz |  |  | 15VDC |  | NO LOAD
300VAC |  | 50Hz |  |  | 15VDC |  | 0,5A
300VAC |  | 50Hz |  |  | 15VDC |  | 1A
300VAC |  | 50Hz |  |  | 15VDC |  | 4A
300VAC |  | 50Hz |  |  | 15VDC |  | 5A
300VAC |  | 50Hz |  |  | 15VDC |  | SHORT

Sheet: TEST3
INPUT |  |  |  | OUTPUT |  |  | Çıkışa ters olarak bağlanacak akü şarj durumu | Çıkışa ters olarak bağlanacak akü nominal gerilimi
Vin (VAC) |  | Fr (Hz) |  | Vout(DC) |  | LOAD (A)
İstenen | Ölçülen | İstenen | Ölçülen | İstenen | Ölçülen | İstenen |  | İstenen | Ölçülen
110VAC |  | 60Hz |  | 12VDC |  | NO LOAD | Boş yada boşa yakın | 12VDC
110VAC |  | 60Hz |  | 12VDC |  | NO LOAD | Tam şarjlı | 12VDC
110VAC |  | 60Hz |  | 12VDC |  | 1A resistive Load | Boş yada boşa yakın | 12VDC
110VAC |  | 60Hz |  | 12VDC |  | 1A resistive Load | Tam şarjlı | 12VDC
110VAC |  | 60Hz |  | 12VDC |  | 5A resistive Load | Boş yada boşa yakın | 12VDC
110VAC |  | 60Hz |  | 12VDC |  | 5A resistive Load | Tam şarjlı | 12VDC
220VAC |  | 50Hz |  | 12VDC |  | NO LOAD | Boş yada boşa yakın | 12VDC
220VAC |  | 50Hz |  | 12VDC |  | NO LOAD | Tam şarjlı | 12VDC
220VAC |  | 50Hz |  | 12VDC |  | 1A resistive Load | Boş yada boşa yakın | 12VDC
220VAC |  | 50Hz |  | 12VDC |  | 1A resistive Load | Tam şarjlı | 12VDC
220VAC |  | 50Hz |  | 12VDC |  | 5A resistive Load | Boş yada boşa yakın | 12VDC
220VAC |  | 50Hz |  | 12VDC |  | 5A resistive Load | Tam şarjlı | 12VDC
264VAC |  | 50Hz |  | 12VDC |  | NO LOAD | Boş yada boşa yakın | 12VDC
264VAC |  | 50Hz |  | 12VDC |  | NO LOAD | Tam şarjlı | 12VDC
264VAC |  | 50Hz |  | 12VDC |  | 1A resistive Load | Boş yada boşa yakın | 12VDC
264VAC |  | 50Hz |  | 12VDC |  | 1A resistive Load | Tam şarjlı | 12VDC
264VAC |  | 50Hz |  | 12VDC |  | 5A resistive Load | Boş yada boşa yakın | 12VDC
264VAC |  | 50Hz |  | 12VDC |  | 5A resistive Load | Tam şarjlı | 12VDC

Sheet: TEST4
INPUT |  |  |  | OUTPUT |  |  |  | Harmonik ÖlçümAkım Harmoniği Ölçümü (Class A) (ölçümler mA olarak yazılmalıdır)
Vin (VAC) |  | Fr (Hz) |  | Vout(DC) |  | Iout(A) |  | 1 | 2 | 3 | 4 | 5 | 6 | 7 | 8 | 9 | 10 | 11 | 12 | 13 | 14 | 15 | 16 | 17 | 18 | 19 | 20 | 21 | 22 | 23 | 24 | 25
İstenen | Ölçülen | İstenen | Ölçülen | İstenen | Ölçülen | İstenen | Ölçülen |  | 1080 | 2300 | 430 | 1140 | 300 | 770 | 230 | 400 | 184 | 330 | 153 | 210 | 131 | 150 | 115 | 132 | 102 | 118 | 92 | 107 | 83 | 97 | 76 | 90
85VAC |  | 60Hz |  | 12VDC |  | NO LOAD
85VAC |  | 60Hz |  | 12VDC |  | 10A
85VAC |  | 60Hz |  | 13,8VDC |  | NO LOAD
85VAC |  | 60Hz |  | 13,8VDC |  | 10A
85VAC |  | 60Hz |  | 14,5VDC |  | NO LOAD
85VAC |  | 60Hz |  | 14,5VDC |  | 10A
85VAC | 90 | 60Hz | 60 | 15VDC | 15.02 | NO LOAD | 0 | 41.31 | 2.61 | 3.58 | 2.39 | 3.86 | 2.07 | 5.31 | 1.67 | 2.99 | 1.56 | 3 | 1.38 | 2.43 | 1.16 | 1.94 | 0.68 | 1.56 | 0.51 | 1.17 | 0.46 | 1.49 | 0.3 | 1.52 | 0.02 | 1.67
85VAC | 90 | 60Hz | 60 | 15VDC | 14.6 | 10A | 5.2 | 1093.83 | 12.41 | 860 | 11.33 | 522.62 | 8.63 | 235.39 | 6.47 | 130.65 | 3.77 | 101 | 3.77 | 44.81 | 2.69 | 35.63 | 1.61 | 33.47 | 1.07 | 10.25 | 1.61 | 16.73 | 2.16 | 16.73 | 1.07 | 4.85
85VAC |  | 60Hz |  | 24VDC |  | NO LOAD
85VAC |  | 60Hz |  | 24VDC |  | 10A
85VAC |  | 60Hz |  | 27,6VDC |  | NO LOAD
85VAC |  | 60Hz |  | 27,6VDC |  | 10A
85VAC |  | 60Hz |  | 29VDC |  | NO LOAD
85VAC |  | 60Hz |  | 29VDC |  | 10A
85VAC |  | 60Hz |  | 30VDC |  | NO LOAD
85VAC |  | 60Hz |  | 30VDC |  | 10A
110VAC |  | 60Hz |  | 12VDC |  | NO LOAD
110VAC |  | 60Hz |  | 12VDC |  | 10A
110VAC |  | 60Hz |  | 13,8VDC |  | NO LOAD
110VAC |  | 60Hz |  | 13,8VDC |  | 10A
110VAC |  | 60Hz |  | 14,5VDC |  | NO LOAD
110VAC |  | 60Hz |  | 14,5VDC |  | 10A
110VAC | 110 | 60Hz | 60 | 15VDC | 15.02 | NO LOAD | 0 | 50 | 1.5 | 2.88 | 1.54 | 3.38 | 1.27 | 5.71 | 1.22 | 2.69 | 1.07 | 2.66 | 0.81 | 2.06 | 0.94 | 2.23 | 0.72 | 1.62 | 0.59 | 1.47 | 0.47 | 1.98 | 0.31 | 2.04 | 0.409 | 1.77
110VAC | 110 | 60Hz | 60 | 15VDC | 14.6 | 10A | 5.2 | 857.39 | 10.4 | 708.89 | 8.03 | 484.26 | 7.09 | 252.535 | 6.14 | 109.71 | 4.25 | 85.59 | 2.36 | 69.04 | 2.83 | 31.68 | 0.94 | 22.22 | 0.47 | 28.84 | 0.945 | 14.18 | 2.36 | 7.56 | 2.83 | 13.71
110VAC |  | 60Hz |  | 24VDC |  | NO LOAD
110VAC |  | 60Hz |  | 24VDC |  | 10A
110VAC |  | 60Hz |  | 27,6VDC |  | NO LOAD
110VAC |  | 60Hz |  | 27,6VDC |  | 10A
110VAC |  | 60Hz |  | 29VDC |  | NO LOAD
110VAC |  | 60Hz |  | 29VDC |  | 10A
110VAC |  | 60Hz |  | 30VDC |  | NO LOAD
110VAC |  | 60Hz |  | 30VDC |  | 10A
220VAC |  | 50Hz |  | 12VDC |  | NO LOAD
220VAC |  | 50Hz |  | 12VDC |  | 10A
220VAC |  | 50Hz |  | 13,8VDC |  | NO LOAD
220VAC |  | 50Hz |  | 13,8VDC |  | 10A
220VAC |  | 50Hz |  | 14,5VDC |  | NO LOAD
220VAC |  | 50Hz |  | 14,5VDC |  | 10A
220VAC | 220 | 50Hz | 50 | 15VDC | 15.02 | NO LOAD | 0 | 82.96 | 0.3 | 2.73 | 0.08 | 5.09 | 0.3 | 4.01 | 0.39 | 3.01 | 0.303 | 3.27 | 0.455 | 2.66 | 0.455 | 2.58 | 0.347 | 2.23 | 0.21 | 2.64 | 0.23 | 2.77 | 0.91 | 3.99 | 0.34 | 6.46
220VAC | 222 | 50Hz | 50 | 15VDC | 14.5 | 10A | 5.2 | 425.18 | 2.24 | 377.08 | 2.24 | 316.16 | 1.92 | 238.56 | 1.92 | 162.89 | 1.6 | 90.1 | 2.24 | 42.96 | 0.96 | 34.63 | 0.96 | 42.32 | 2.88 | 41.36 | 2.56 | 34.3 | 1.6 | 27.25 | 2.88 | 13.46
220VAC |  | 50Hz |  | 24VDC |  | NO LOAD
220VAC |  | 50Hz |  | 24VDC |  | 10A
220VAC |  | 50Hz |  | 27,6VDC |  | NO LOAD
220VAC |  | 50Hz |  | 27,6VDC |  | 10A
220VAC |  | 50Hz |  | 29VDC |  | NO LOAD
220VAC |  | 50Hz |  | 29VDC |  | 10A
220VAC |  | 50Hz |  | 30VDC |  | NO LOAD
220VAC |  | 50Hz |  | 30VDC |  | 10A
264VAC |  | 50Hz |  | 12VDC |  | NO LOAD
264VAC |  | 50Hz |  | 12VDC |  | 10A
264VAC |  | 50Hz |  | 13,8VDC |  | NO LOAD
264VAC |  | 50Hz |  | 13,8VDC |  | 10A
264VAC |  | 50Hz |  | 14,5VDC |  | NO LOAD
264VAC |  | 50Hz |  | 14,5VDC |  | 10A
264VAC | 262 | 50Hz | 50 | 15VDC | 15.02 | NO LOAD | 0 | 97.99564 | 3.94876 | 3.37604 | 1.26602 | 7.74681 | 2.32103 | 4.76263 | 1.68802 | 3.85833 | 2.11003 | 2.11003 | 3.34590 | 2.07988 | 2.77318 | 1.98945 | 2.59232 | 1.98945 | 2.17031 | 1.65788 | 2.80332 | 2.20046 | 1.77845 | 2.35117 | 5.06406 | 1.35645
264VAC | 265 | 50Hz | 50 | 15VDC | 14.6 | 10A | 5.2 | 370.40046 | 13.97738 | 324.68279 | 11.93901 | 275.47078 | 8.44466 | 216.06694 | 6.98869 | 152.87755 | 3.49434 | 88.81458 | 1.74717 | 44.84408 | 2.91195 | 24.75160 | 3.49434 | 29.70192 | 2.91195 | 33.19627 | 3.78554 | 26.78997 | 1.74717 | 25.62519 | 2.91195 | 12.52140
264VAC |  | 50Hz |  | 24VDC |  | NO LOAD
264VAC |  | 50Hz |  | 24VDC |  | 10A
264VAC |  | 50Hz |  | 27,6VDC |  | NO LOAD
264VAC |  | 50Hz |  | 27,6VDC |  | 10A
264VAC |  | 50Hz |  | 29VDC |  | NO LOAD
264VAC |  | 50Hz |  | 29VDC |  | 10A
264VAC |  | 50Hz |  | 30VDC |  | NO LOAD
264VAC |  | 50Hz |  | 30VDC |  | 10A

Sheet: Procedure
# | Final testspec | Test requirements | According to (newest edition) | ENKO TEST ACTION FOR DBC2 90/150W | Prototype test
1 | Test specimen documentation | Full data package available, datasheet, test reports, schematic, 3D stp files, Layout files |  | Critical components and their circuit connection diagram will be shared with DEIF prior to type tests. Creapage and clearance data on the pcb gerber file will be shared with DEIF.
2 | Performance Test | According to datasheet |  | Functional performance tests will be completed by ENKO before sending the samples. BMS algorithm will not be included with the first samples, this task will be tested after the type tests are completed and approved. Function tests will include: - Maximum and minimum AC input voltage limit test - Output voltage selection (150W only) and load regulation test - Line regulation test - Output voltage ripple test - Maximum power test - Short circuit test - Reverse polarity protection test - Power derating test - Efficiency test - Temperature limit tests
3 | Cold Test | -40°C | IACS E10 Revision 7 & relevant product standard | Cold start function will be tested at ENKO
4 | Dry Heat Test | 70°C | IACS E10 Revision 7 & relevant product standard | DEIF (test should be conducted at 60 degrees Celsius)
5 | Damp Heat Dynamic - Test | 55°C, 97% RH, 2 cyckles 2x(12+12 h) | IACS E10 Revision 7 & relevant product standard | DEIF
6 | Vibration Test | 2-13,2Hz, amplitude ±1mm 13,2-100Hz, acceleration +-0,7G | IACS E10 Revision 7 & relevant product standard | DEIF
7 | Bump Test | Fix mount 25G 16ms, DIN mount 15G 16ms 1000 bumps in each direction correspond to 2000 bumps in each axis. Total 6000 bumps. | Deif standard & relevant product standard | DEIF
8 | Mechanical Shock Test | Fix mount 50G 11ms, DIN mount 15G 11ms | IEC 60068-2-27 or relevant product standard | DEIF
9 | Inclination Test | Static 22,5°C, Dynamic 22,5°C | IEC 60092-504 | DEIF
10 | Flammability Test | 1x30sek needle flame | IEC 60092-101 | DEIF
11 | Insulation Resistance Test | Un<65V testvoltage 2xUn (minimum 50V), before test 10MΩ, after test 1MΩ Un>65V testvoltage 500V, before test 100MΩ, after test 10MΩ | IACS E10 rev. 7 | ENKO
12 | High-Voltage Test | Un≤65V: Testvoltage = 2xUn + 500 V 65V<Un≤250V: Testvoltage 1500V 250V<Un≤500V: Testvoltage 2000V 500V<Un≤690V: Testvoltage 2500V | IACS E10 rev. 7 | ENKO
13 | Radiated Interf. | 150kHz - 6GHz Power distribution zone | IACS E10 rev. 7, IEC 61000-6-3, IEC 62041 environment 1 | DEIF
14 | Terminal Interf. Volt., AC, DC and Tele ports | 9kHz - 30 MHz Power distribution zone | IACS E10 rev. 7, IEC 61000-6-3, IEC 62041 environment 1 | DEIF
15 | Enclosure Test (IP degree) | IP 20 | EN60529 | DEIF
16 | High Temperature life time test | To be evaluated based on HALT result |  | DEIF
17 | Electrical Fast Transients, Burst (5/50 ns, CM) | 1kV I/O & Com ports, 2kV AC & DC I/O supply ports and GND port Tested at 5KHz and 100 kHz ,Criteria B | IACS E10 rev. 7, IEC 61000-6-2, IEC 62041 environment 1 | ENKO
18 | RF E-field | 80MHz - 6GHz 10V/m 80%AM 3s dwell time | IACS E10 rev. 7, IEC 61000-6-2, IEC 62041 environment 1 | DEIF
19 | Load Dump Test | To be determined | ISO 16750-2 load dump Test A / SAE J1113-11 pulse 5a | DEIF
20 | Electro-static Discharge (ESD) | 6kV contact, 8kV air discharge (including terminals) | IACS E10 rev. 7, IEC 61000-6-2, IEC 62041 environment 1 | ENKO
21 | Slow Transients, Surge (1,2/50 ms, DM & CM) | 1kV CM long COM ports >30m 1kV CM, 0,5 kV DM DC ports 2kV CM, 1 kV DM AC ports | IACS E10 rev. 7, IEC 61000-6-2, IEC 62041 environment 1 | DEIF
22 | RF Conducted | 150kHz - 80MHz 10Vrms 80%AM 3s dwell time | IACS E10 rev. 7, IEC 61000-6-2, IEC 62041 environment 1 | ENKO
23 | Power Frequency Magn. Field | 30A/m, 50 & 60Hz, 60sec. | IEC 61000-6-2 | DEIF
24 | Low-freq. Harm., AC power ports | See test specified in standard | IACS E10 rev. 7 | DEIF
25 | Voltage Variations, AC power ports | +6 %V/ -10 %V, +/- 5 %Hz - 15 minutes +/- 20 %V - 1,5 seconds +/- 10 %Hz - 5 seconds | IACS E10 rev. 7 | DEIF
26 | Voltage Dips, AC power ports | 0%-1 cycle, 40%-10/12 cycles, 70%-25/30cycles | IEC 61000-6-2 | DEIF
27 | Voltage Interruptions, AC power ports | 0% voltage - various timing according to standard | IACS E10 rev. 7, IEC 61000-6-2, IEC 62041 environment 1 | DEIF
28 | Reverse Polarity | 100% 1 minute | IEC/EN 61010-1 | ENKO
29 | Physical Spacing on PCBs, terminals, etc. |  | CE (EN/IEC requirements) and UL requirements | ENKO
30 | Temperature Rise in Components & Terminals |  | CE (EN/IEC requirements) and UL requirements | ENKO
31 | Single Fault Condition Test |  | CE (EN/IEC requirements) and UL requirements | ENKO
32 | Limited Circuits Test |  | CE (EN/IEC requirements) and UL requirements | ENKO
33 | Enclosure rigidity – Static Test |  | CE (EN/IEC requirements) and UL requirements | DEIF
34 | Enclosure rigidity – Impact Test |  | CE (EN/IEC requirements) and UL requirements | DEIF
35 | Protection against spread of fire |  | CE (EN/IEC requirements) and UL requirements | DEIF
36 | Durability of markings |  | CE (EN/IEC requirements) and UL requirements | DEIF
37 | Marking requirements |  | CE (EN/IEC requirements) and UL requirements | ENKO
38 | Protective Bonding Impedance Test |  | CE (EN/IEC requirements) and UL requirements | There are no conductive surfaces on DBC2, enclosure is plastic. Therefore; this test is not applicable for DBC2 series chargers.
39 | Routine High Voltage Test (Production) | According to EN/IEC and UL requirements |  | ENKO
40 | TRF for EN61010-1 |  | Documentation according to CB requirements | DEIF
