alper-bozcal/75W_XDPS/Tests/EMC/2023 02 17 IZTECHLAB/13Vadapter_1.Rtf

IZTECHLABS EMC TEST REPORT

Common Information
Test Description: | Radiated Emission
Test Site: | SAC
Test Standard:
Test Mode:
Environment Conditions:
Comment:
Full Spectrum

Final_Result
Frequency (MHz) | QuasiPeak (dBµV/m) | Limit (dBµV/m) | Margin (dB) | Meas. Time (ms) | Bandwidth (kHz) | Height (cm) | Pol | Azimuth (deg)
174.090000 | 37.46 | 40.00 | 2.54 | 1000.0 | 120.000 | 176.0 | H | 82.0
174.600000 | 40.54 | 40.00 | -0.54 | 1000.0 | 120.000 | 100.0 | V | 123.0
182.610000 | 37.84 | 40.00 | 2.16 | 1000.0 | 120.000 | 100.0 | V | 227.0
(continuation of the "Final_Result" table from column 15 ...) Frequency (MHz) | Corr. (dB/m) | Comment
174.090000 | 10.6 | 2:41:35 PM - 2/17/2023
174.600000 | 10.7 | 2:44:33 PM - 2/17/2023
182.610000 | 10.1 | 2:47:17 PM - 2/17/2023
Fewer than six emissions within 10 dB of the limit have been observed
