alper-bozcal/75W_XDPS/Tests/EMC/2023 02 17 IZTECHLAB/13Vadapter_2.Rtf

IZTECHLABS EMC TEST REPORT

Common Information
Test Description: | Radiated Emission
Test Site: | SAC
Test Standard:
Test Mode:
Environment Conditions:
Comment:
Full Spectrum

Final_Result
Frequency (MHz) | QuasiPeak (dBµV/m) | Limit (dBµV/m) | Margin (dB) | Meas. Time (ms) | Bandwidth (kHz) | Height (cm) | Pol | Azimuth (deg)
174.570000 | 37.86 | 40.00 | 2.14 | 1000.0 | 120.000 | 163.0 | H | 66.0
178.140000 | 35.78 | 40.00 | 4.22 | 1000.0 | 120.000 | 100.0 | V | 240.0
182.070000 | 38.79 | 40.00 | 1.21 | 1000.0 | 120.000 | 139.0 | H | 270.0
230.250000 | 34.17 | 47.00 | 12.83 | 1000.0 | 120.000 | 127.0 | H | 51.0
(continuation of the "Final_Result" table from column 15 ...) Frequency (MHz) | Corr. (dB/m) | Comment
174.570000 | 10.7 | 3:21:04 PM - 2/17/2023
178.140000 | 11.3 | 3:24:09 PM - 2/17/2023
182.070000 | 10.2 | 3:26:51 PM - 2/17/2023
230.250000 | 10.9 | 3:29:54 PM - 2/17/2023
Fewer than six emissions within 10 dB of the limit have been observed
