alper-bozcal/75W_XDPS/Tests/EMC/2023 02 17 IZTECHLAB/BCS2405_2.Rtf

IZTECHLABS EMC TEST REPORT

Common Information
Test Description: | Radiated Emission
Test Site: | SAC
Test Standard:
Test Mode:
Environment Conditions:
Comment:
Full Spectrum

Final_Result
Frequency (MHz) | QuasiPeak (dBµV/m) | Limit (dBµV/m) | Margin (dB) | Meas. Time (ms) | Bandwidth (kHz) | Height (cm) | Pol | Azimuth (deg)
30.000000 | 29.46 | 40.00 | 10.54 | 1000.0 | 120.000 | 190.0 | V | 294.0
43.830000 | 39.16 | 40.00 | 0.84 | 1000.0 | 120.000 | 100.0 | V | 330.0
78.930000 | 31.79 | 40.00 | 8.21 | 1000.0 | 120.000 | 103.0 | V | 270.0
94.680000 | 42.28 | 40.00 | -2.28 | 1000.0 | 120.000 | 103.0 | V | 141.0
(continuation of the "Final_Result" table from column 15 ...) Frequency (MHz) | Corr. (dB/m) | Comment
30.000000 | 20.3 | 3:50:57 PM - 2/17/2023
43.830000 | 12.1 | 3:53:48 PM - 2/17/2023
78.930000 | 10.8 | 3:56:33 PM - 2/17/2023
94.680000 | 11.6 | 3:48:09 PM - 2/17/2023
Fewer than six emissions within 10 dB of the limit have been observed
