alper-bozcal/75W_XDPS/Tests/EMC/2023 02 17 IZTECHLAB/DBC2-Ref-_full.Rtf

IZTECHLABS EMC TEST REPORT

Common Information
Test Description: | Radiated Emission
Test Site: | SAC
Test Standard:
Test Mode:
Environment Conditions:
Comment:
Full Spectrum

Final_Result
Frequency (MHz) | QuasiPeak (dBµV/m) | Limit (dBµV/m) | Margin (dB) | Meas. Time (ms) | Bandwidth (kHz) | Height (cm) | Pol | Azimuth (deg)
30.000000 | 22.65 | 40.00 | 17.35 | 1000.0 | 120.000 | 187.0 | V | 24.0
37.890000 | 33.34 | 40.00 | 6.66 | 1000.0 | 120.000 | 100.0 | V | -43.0
48.210000 | 31.48 | 40.00 | 8.52 | 1000.0 | 120.000 | 100.0 | V | 15.0
66.540000 | 30.86 | 40.00 | 9.14 | 1000.0 | 120.000 | 115.0 | V | -45.0
71.730000 | 32.27 | 40.00 | 7.73 | 1000.0 | 120.000 | 100.0 | V | -45.0
79.200000 | 21.86 | 40.00 | 18.14 | 1000.0 | 120.000 | 188.0 | H | 253.0
79.230000 | 34.99 | 40.00 | 5.01 | 1000.0 | 120.000 | 106.0 | V | 227.0
103.350000 | 28.49 | 40.00 | 11.51 | 1000.0 | 120.000 | 103.0 | V | 186.0
123.990000 | 29.02 | 40.00 | 10.98 | 1000.0 | 120.000 | 270.0 | H | 263.0
213.630000 | 26.93 | 40.00 | 13.07 | 1000.0 | 120.000 | 139.0 | H | 119.0
214.710000 | 27.13 | 40.00 | 12.87 | 1000.0 | 120.000 | 139.0 | H | 119.0
215.790000 | 25.64 | 40.00 | 14.36 | 1000.0 | 120.000 | 175.0 | H | 110.0
217.050000 | 27.34 | 40.00 | 12.66 | 1000.0 | 120.000 | 161.0 | H | 118.0
218.160000 | 28.31 | 40.00 | 11.69 | 1000.0 | 120.000 | 175.0 | H | 289.0
219.300000 | 26.92 | 40.00 | 13.08 | 1000.0 | 120.000 | 150.0 | H | 119.0
220.470000 | 26.79 | 40.00 | 13.21 | 1000.0 | 120.000 | 151.0 | H | 114.0
221.730000 | 23.74 | 40.00 | 16.26 | 1000.0 | 120.000 | 175.0 | H | 101.0
222.750000 | 28.53 | 40.00 | 11.47 | 1000.0 | 120.000 | 222.0 | H | 285.0
223.920000 | 29.02 | 40.00 | 10.98 | 1000.0 | 120.000 | 223.0 | H | 285.0
225.150000 | 24.67 | 40.00 | 15.33 | 1000.0 | 120.000 | 127.0 | H | 114.0
226.260000 | 29.03 | 40.00 | 10.97 | 1000.0 | 120.000 | 150.0 | H | 141.0
227.460000 | 28.28 | 40.00 | 11.72 | 1000.0 | 120.000 | 152.0 | H | 132.0
228.570000 | 28.76 | 40.00 | 11.24 | 1000.0 | 120.000 | 151.0 | H | 127.0
229.620000 | 28.39 | 40.00 | 11.61 | 1000.0 | 120.000 | 152.0 | H | 132.0
(continuation of the "Final_Result" table from column 15 ...) Frequency (MHz) | Corr. (dB/m) | Comment
30.000000 | 20.3 | 12:25:49 PM - 2/17/2023
37.890000 | 15.8 | 12:28:47 PM - 2/17/2023
48.210000 | 9.1 | 1:28:24 PM - 2/17/2023
66.540000 | 8.6 | 1:25:27 PM - 2/17/2023
71.730000 | 9.7 | 1:28:13 PM - 2/17/2023
79.200000 | 10.8 | 1:10:58 PM - 2/17/2023
79.230000 | 10.8 | 1:34:03 PM - 2/17/2023
103.350000 | 12.1 | 1:31:18 PM - 2/17/2023
123.990000 | 12.0 | 1:13:39 PM - 2/17/2023
213.630000 | 10.8 | 12:37:28 PM - 2/17/2023
214.710000 | 10.7 | 12:40:16 PM - 2/17/2023
215.790000 | 10.7 | 12:43:01 PM - 2/17/2023
217.050000 | 10.5 | 12:45:50 PM - 2/17/2023
218.160000 | 10.4 | 1:16:31 PM - 2/17/2023
219.300000 | 10.2 | 12:48:39 PM - 2/17/2023
220.470000 | 10.2 | 12:51:26 PM - 2/17/2023
221.730000 | 10.2 | 12:54:12 PM - 2/17/2023
222.750000 | 10.2 | 1:19:16 PM - 2/17/2023
223.920000 | 10.4 | 1:22:02 PM - 2/17/2023
225.150000 | 10.5 | 12:57:02 PM - 2/17/2023
226.260000 | 10.6 | 12:59:47 PM - 2/17/2023
227.460000 | 10.7 | 1:02:35 PM - 2/17/2023
228.570000 | 10.8 | 1:05:23 PM - 2/17/2023
229.620000 | 10.9 | 1:08:09 PM - 2/17/2023
