alper-bozcal/75W_XDPS/Tests/EMC/2023 02 17 IZTECHLAB/DBC290W_full.Rtf

IZTECHLABS EMC TEST REPORT

Common Information
Test Description: | Radiated Emission
Test Site: | SAC
Test Standard:
Test Mode:
Environment Conditions:
Comment:
Full Spectrum

Final_Result
Frequency (MHz) | QuasiPeak (dBµV/m) | Limit (dBµV/m) | Margin (dB) | Meas. Time (ms) | Bandwidth (kHz) | Height (cm) | Pol | Azimuth (deg)
30.150000 | 38.93 | 40.00 | 1.07 | 1000.0 | 120.000 | 198.0 | V | 105.0
38.430000 | 34.81 | 40.00 | 5.19 | 1000.0 | 120.000 | 100.0 | V | 90.0
46.950000 | 43.26 | 40.00 | -3.26 | 1000.0 | 120.000 | 100.0 | V | 1.0
76.950000 | 39.98 | 40.00 | 0.02 | 1000.0 | 120.000 | 103.0 | V | 313.0
87.150000 | 45.09 | 40.00 | -5.09 | 1000.0 | 120.000 | 103.0 | V | 263.0
131.250000 | 39.31 | 40.00 | 0.69 | 1000.0 | 120.000 | 107.0 | V | 177.0
188.430000 | 38.98 | 40.00 | 1.02 | 1000.0 | 120.000 | 100.0 | V | 258.0
192.300000 | 41.52 | 40.00 | -1.52 | 1000.0 | 120.000 | 164.0 | H | 245.0
(continuation of the "Final_Result" table from column 15 ...) Frequency (MHz) | Corr. (dB/m) | Comment
30.150000 | 20.2 | 4:53:27 PM - 2/17/2023
38.430000 | 15.5 | 4:56:23 PM - 2/17/2023
46.950000 | 10.0 | 4:59:11 PM - 2/17/2023
76.950000 | 10.5 | 5:02:11 PM - 2/17/2023
87.150000 | 11.4 | 5:04:56 PM - 2/17/2023
131.250000 | 11.5 | 5:07:43 PM - 2/17/2023
188.430000 | 9.7 | 5:10:32 PM - 2/17/2023
192.300000 | 9.7 | 5:13:17 PM - 2/17/2023
