alper-bozcal/75W_XDPS/Tests/EMC/2023 02 27 IZTECHLAB/RE_DBC2_150W_1510_B.Rtf

IZTECHLABS EMC TEST REPORT

Common Information
Test Description: | Radiated Emission
Test Site: | SAC
Test Standard:
Test Mode:
Environment Conditions:
Comment:

Final_Result
Frequency (MHz) | QuasiPeak (dBµV/m) | Limit (dBµV/m) | Margin (dB) | Meas. Time (ms) | Bandwidth (kHz) | Height (cm) | Pol | Azimuth (deg)
166.648750 | 34.80 | 40.00 | 5.20 | 1000.0 | 120.000 | 176.0 | H | 113.0
(continuation of the "Final_Result" table from column 15 ...) Frequency (MHz) | Corr. (dB/m) | Comment
166.648750 | 9.9 | 12:03:15 PM - 2/27/2023
Fewer than six emissions within 10 dB of the limit have been observed
