alper-bozcal/75W_XDPS/Tests/EMC/2023 02 27 IZTECHLAB/RE_DBC2_150W_1510_B2.Rtf

IZTECHLABS EMC TEST REPORT

Common Information
Test Description: | Radiated Emission
Test Site: | SAC
Test Standard:
Test Mode:
Environment Conditions:
Comment:

Final_Result
Frequency (MHz) | QuasiPeak (dBµV/m) | Limit (dBµV/m) | Margin (dB) | Meas. Time (ms) | Bandwidth (kHz) | Height (cm) | Pol | Azimuth (deg)
33.135478 | 34.64 | 40.00 | 5.36 | 1000.0 | 120.000 | 100.0 | V | 47.0
47.824953 | 40.71 | 40.00 | -0.71 | 1000.0 | 120.000 | 100.0 | V | 326.0
72.344347 | 38.78 | 40.00 | 1.22 | 1000.0 | 120.000 | 105.0 | V | 351.0
79.673294 | 41.36 | 40.00 | -1.36 | 1000.0 | 120.000 | 100.0 | V | 152.0
92.522819 | 37.07 | 40.00 | 2.93 | 1000.0 | 120.000 | 105.0 | V | 134.0
159.506750 | 36.95 | 40.00 | 3.05 | 1000.0 | 120.000 | 246.0 | H | 109.0
(continuation of the "Final_Result" table from column 15 ...) Frequency (MHz) | Corr. (dB/m) | Comment
33.135478 | 18.6 | 1:57:34 PM - 2/27/2023
47.824953 | 9.4 | 2:06:28 PM - 2/27/2023
72.344347 | 9.8 | 2:09:17 PM - 2/27/2023
79.673294 | 10.9 | 2:03:20 PM - 2/27/2023
92.522819 | 11.5 | 2:00:27 PM - 2/27/2023
159.506750 | 9.7 | 1:54:15 PM - 2/27/2023
