alper-bozcal/75W_XDPS/Tests/EMC/2023 02 27 IZTECHLAB/RE_DBC2_150W_1510_B4.Rtf

IZTECHLABS EMC TEST REPORT

Common Information
Test Description: | Radiated Emission
Test Site: | SAC
Test Standard:
Test Mode:
Environment Conditions:
Comment:

Final_Result
Frequency (MHz) | QuasiPeak (dBµV/m) | Limit (dBµV/m) | Margin (dB) | Meas. Time (ms) | Bandwidth (kHz) | Height (cm) | Pol | Azimuth (deg)
47.156875 | 33.96 | 40.00 | 6.04 | 1000.0 | 120.000 | 100.0 | V | -5.0
74.983750 | 36.88 | 40.00 | 3.12 | 1000.0 | 120.000 | 119.0 | V | 169.0
99.840000 | 34.84 | 40.00 | 5.16 | 1000.0 | 120.000 | 103.0 | V | 33.0
156.100000 | 33.29 | 40.00 | 6.71 | 1000.0 | 120.000 | 208.0 | H | 112.0
(continuation of the "Final_Result" table from column 15 ...) Frequency (MHz) | Corr. (dB/m) | Comment
47.156875 | 9.8 | 4:34:45 PM - 2/27/2023
74.983750 | 10.2 | 4:37:59 PM - 2/27/2023
99.840000 | 11.9 | 4:36:18 PM - 2/27/2023
156.100000 | 9.7 | 4:32:41 PM - 2/27/2023
Fewer than six emissions within 10 dB of the limit have been observed
