alper-bozcal/75W_XDPS/Tests/EMC/2023 02 27 IZTECHLAB/RE_DBC2_75W.Rtf

IZTECHLABS EMC TEST REPORT

Common Information
Test Description: | Radiated Emission
Test Site: | SAC
Test Standard:
Test Mode:
Environment Conditions:
Comment:

Final_Result
Frequency (MHz) | QuasiPeak (dBµV/m) | Limit (dBµV/m) | Margin (dB) | Meas. Time (ms) | Bandwidth (kHz) | Height (cm) | Pol | Azimuth (deg)
76.014375 | 33.81 | 40.00 | 6.19 | 1000.0 | 120.000 | 300.0 | V | 187.0
78.378750 | 36.35 | 40.00 | 3.65 | 1000.0 | 120.000 | 107.0 | V | 214.0
87.290625 | 38.76 | 40.00 | 1.24 | 1000.0 | 120.000 | 100.0 | V | 68.0
124.878125 | 34.61 | 40.00 | 5.39 | 1000.0 | 120.000 | 103.0 | V | 159.0
134.093125 | 35.62 | 40.00 | 4.38 | 1000.0 | 120.000 | 100.0 | V | -7.0
146.581875 | 37.70 | 40.00 | 2.30 | 1000.0 | 120.000 | 103.0 | V | 159.0
169.922500 | 35.05 | 40.00 | 4.95 | 1000.0 | 120.000 | 164.0 | H | 119.0
202.417500 | 39.51 | 40.00 | 0.49 | 1000.0 | 120.000 | 100.0 | V | 292.0
(continuation of the "Final_Result" table from column 15 ...) Frequency (MHz) | Corr. (dB/m) | Comment
76.014375 | 10.4 | 11:19:55 AM - 2/27/2023
78.378750 | 10.7 | 11:14:10 AM - 2/27/2023
87.290625 | 11.4 | 11:07:15 AM - 2/27/2023
124.878125 | 12.0 | 11:09:38 AM - 2/27/2023
134.093125 | 11.2 | 11:04:52 AM - 2/27/2023
146.581875 | 10.1 | 11:11:53 AM - 2/27/2023
169.922500 | 10.2 | 11:02:10 AM - 2/27/2023
202.417500 | 10.4 | 11:16:37 AM - 2/27/2023
