alper-bozcal/75W_XDPS/Tests/EMC/2023 02 27 IZTECHLAB/RE_DBC2_75W_2.Rtf

IZTECHLABS EMC TEST REPORT

Common Information
Test Description: | Radiated Emission
Test Site: | SAC
Test Standard:
Test Mode:
Environment Conditions:
Comment:

Final_Result
Frequency (MHz) | QuasiPeak (dBµV/m) | Limit (dBµV/m) | Margin (dB) | Meas. Time (ms) | Bandwidth (kHz) | Height (cm) | Pol | Azimuth (deg)
31.576250 | 34.49 | 40.00 | 5.51 | 1000.0 | 120.000 | 214.0 | V | 214.0
75.286875 | 38.24 | 40.00 | 1.76 | 1000.0 | 120.000 | 103.0 | V | 162.0
83.289375 | 35.63 | 40.00 | 4.37 | 1000.0 | 120.000 | 103.0 | V | 155.0
150.886250 | 35.84 | 40.00 | 4.16 | 1000.0 | 120.000 | 227.0 | H | 102.0
202.902500 | 34.18 | 40.00 | 5.82 | 1000.0 | 120.000 | 103.0 | V | 294.0
204.357500 | 35.29 | 40.00 | 4.71 | 1000.0 | 120.000 | 143.0 | H | 209.0
(continuation of the "Final_Result" table from column 15 ...) Frequency (MHz) | Corr. (dB/m) | Comment
31.576250 | 19.4 | 4:09:13 PM - 2/27/2023
75.286875 | 10.3 | 4:03:54 PM - 2/27/2023
83.289375 | 11.1 | 4:05:29 PM - 2/27/2023
150.886250 | 9.8 | 4:01:58 PM - 2/27/2023
202.902500 | 10.4 | 4:07:10 PM - 2/27/2023
204.357500 | 10.5 | 3:59:58 PM - 2/27/2023
