alper-bozcal/75W_XDPS/Tests/EMC/2023 05 23 Vestel RE CE Harmonics/Conducted Emission/DBC-150W-C2_4.9dB.Rtf

DBC-150W-C2_4.9dB

Common Information
Test Description: | .. Mode
Test site : | Test Site 2
Test Standard: | EN55032
Environment Conditions: | Temp: 25°c Hum:%40
Operator Name: | Kadir ARSLAN
Result:
EN 55032 Conducted Emission Auto Test-Class B

Final Result 1
Frequency (MHz) | QuasiPeak (dBµV) | Meas. Time (ms) | Bandwidth (kHz) | Line | Corr. (dB) | Margin (dB) | Limit (dBµV)
0.188250 | 55.7 | 2000.0 | 9.000 | L1 | 12.1 | 8.4 | 64.1
0.192750 | 55.6 | 2000.0 | 9.000 | L1 | 12.0 | 8.3 | 63.9
0.309750 | 51.3 | 2000.0 | 9.000 | L1 | 11.8 | 8.7 | 60.0
0.323250 | 51.1 | 2000.0 | 9.000 | L1 | 11.8 | 8.6 | 59.6
0.388500 | 51.2 | 2000.0 | 9.000 | L1 | 11.8 | 6.9 | 58.1
0.395250 | 49.8 | 2000.0 | 9.000 | L1 | 11.8 | 8.2 | 58.0
0.507750 | 47.0 | 2000.0 | 9.000 | L1 | 11.7 | 9.0 | 56.0
0.519000 | 47.2 | 2000.0 | 9.000 | L1 | 11.7 | 8.8 | 56.0
0.579750 | 47.6 | 2000.0 | 9.000 | L1 | 11.7 | 8.4 | 56.0
0.591000 | 46.7 | 2000.0 | 9.000 | L1 | 11.7 | 9.3 | 56.0
0.645000 | 44.6 | 2000.0 | 9.000 | L1 | 11.7 | 11.4 | 56.0
0.766500 | 45.0 | 2000.0 | 9.000 | L1 | 11.7 | 11.0 | 56.0
0.775500 | 45.4 | 2000.0 | 9.000 | L1 | 11.7 | 10.6 | 56.0
0.838500 | 45.7 | 2000.0 | 9.000 | L1 | 11.7 | 10.3 | 56.0
0.852000 | 44.7 | 2000.0 | 9.000 | L1 | 11.7 | 11.3 | 56.0
1.128750 | 44.7 | 2000.0 | 9.000 | L1 | 11.7 | 11.3 | 56.0
2.256000 | 45.0 | 2000.0 | 9.000 | L1 | 11.7 | 11.0 | 56.0
2.258250 | 43.8 | 2000.0 | 9.000 | L1 | 11.7 | 12.2 | 56.0
3.385500 | 42.8 | 2000.0 | 9.000 | L1 | 11.7 | 13.2 | 56.0
Final Result 2 Frequency (MHz) | Average (dBµV) | Meas. Time (ms) | Bandwidth (kHz) | Line | Corr. (dB) | Margin (dB) | Limit (dBµV)
0.188250 | 45.5 | 2000.0 | 9.000 | L1 | 12.1 | 8.6 | 54.1
0.192750 | 47.7 | 2000.0 | 9.000 | L1 | 12.0 | 6.2 | 53.9
0.309750 | 37.5 | 2000.0 | 9.000 | L1 | 11.8 | 12.4 | 50.0
0.323250 | 44.2 | 2000.0 | 9.000 | L1 | 11.8 | 5.4 | 49.6
0.388500 | 43.2 | 2000.0 | 9.000 | L1 | 11.8 | 4.9 | 48.1
0.395250 | 33.2 | 2000.0 | 9.000 | L1 | 11.8 | 14.7 | 48.0
0.507750 | 37.3 | 2000.0 | 9.000 | L1 | 11.7 | 8.7 | 46.0
0.519000 | 37.1 | 2000.0 | 9.000 | L1 | 11.7 | 8.9 | 46.0
0.579750 | 39.3 | 2000.0 | 9.000 | L1 | 11.7 | 6.7 | 46.0
0.591000 | 28.8 | 2000.0 | 9.000 | L1 | 11.7 | 17.2 | 46.0
0.645000 | 35.5 | 2000.0 | 9.000 | L1 | 11.7 | 10.5 | 46.0
0.766500 | 34.8 | 2000.0 | 9.000 | L1 | 11.7 | 11.2 | 46.0
0.775500 | 34.9 | 2000.0 | 9.000 | L1 | 11.7 | 11.1 | 46.0
0.838500 | 35.4 | 2000.0 | 9.000 | L1 | 11.7 | 10.6 | 46.0
0.852000 | 26.4 | 2000.0 | 9.000 | L1 | 11.7 | 19.6 | 46.0
1.128750 | 37.7 | 2000.0 | 9.000 | L1 | 11.7 | 8.3 | 46.0
2.256000 | 37.5 | 2000.0 | 9.000 | L1 | 11.7 | 8.5 | 46.0
2.258250 | 35.0 | 2000.0 | 9.000 | L1 | 11.7 | 11.0 | 46.0
3.385500 | 32.1 | 2000.0 | 9.000 | L1 | 11.7 | 13.9 | 46.0
