alper-bozcal/75W_XDPS/Tests/EMC/2023 05 23 Vestel RE CE Harmonics/Conducted Emission/DBC2-150W-C1.Rtf

DBC2-150W-C1

Common Information
Test Description: | .. Mode
Test site : | Test Site 2
Test Standard: | EN55032
Environment Conditions: | Temp: 25°c Hum:%40
Operator Name: | Kadir ARSLAN
Result:
EN 55032 Conducted Emission Auto Test-Class B

Final Result 1
Frequency (MHz) | QuasiPeak (dBµV) | Meas. Time (ms) | Bandwidth (kHz) | Line | Corr. (dB) | Margin (dB) | Limit (dBµV)
0.192750 | 56.6 | 2000.0 | 9.000 | L1 | 12.0 | 7.3 | 63.9
0.195000 | 56.5 | 2000.0 | 9.000 | L1 | 12.0 | 7.3 | 63.8
1.131000 | 44.4 | 2000.0 | 9.000 | L1 | 11.7 | 11.6 | 56.0
3.682500 | 45.8 | 2000.0 | 9.000 | L1 | 11.7 | 10.2 | 56.0
3.729750 | 45.5 | 2000.0 | 9.000 | L1 | 11.7 | 10.5 | 56.0
3.750000 | 46.5 | 2000.0 | 9.000 | L1 | 11.7 | 9.5 | 56.0
3.819750 | 46.6 | 2000.0 | 9.000 | L1 | 11.7 | 9.4 | 56.0
3.887250 | 46.9 | 2000.0 | 9.000 | L1 | 11.7 | 9.1 | 56.0
3.939000 | 45.8 | 2000.0 | 9.000 | L1 | 11.7 | 10.2 | 56.0
3.952500 | 46.7 | 2000.0 | 9.000 | L1 | 11.7 | 9.3 | 56.0
3.954750 | 47.0 | 2000.0 | 9.000 | L1 | 11.7 | 9.0 | 56.0
3.990750 | 45.9 | 2000.0 | 9.000 | L1 | 11.7 | 10.1 | 56.0
4.022250 | 47.6 | 2000.0 | 9.000 | L1 | 11.7 | 8.4 | 56.0
4.026750 | 46.2 | 2000.0 | 9.000 | L1 | 11.7 | 9.8 | 56.0
4.087500 | 47.2 | 2000.0 | 9.000 | L1 | 11.7 | 8.8 | 56.0
4.092000 | 47.0 | 2000.0 | 9.000 | L1 | 11.7 | 9.0 | 56.0
4.152750 | 46.1 | 2000.0 | 9.000 | L1 | 11.6 | 9.9 | 56.0
4.159500 | 46.9 | 2000.0 | 9.000 | L1 | 11.6 | 9.1 | 56.0
4.218000 | 45.9 | 2000.0 | 9.000 | L1 | 11.6 | 10.1 | 56.0
4.227000 | 46.4 | 2000.0 | 9.000 | L1 | 11.6 | 9.6 | 56.0
Final Result 2 Frequency (MHz) | Average (dBµV) | Meas. Time (ms) | Bandwidth (kHz) | Line | Corr. (dB) | Margin (dB) | Limit (dBµV)
0.192750 | 44.6 | 2000.0 | 9.000 | L1 | 12.0 | 9.3 | 53.9
0.195000 | 44.6 | 2000.0 | 9.000 | L1 | 12.0 | 9.2 | 53.8
1.131000 | 37.0 | 2000.0 | 9.000 | L1 | 11.7 | 9.0 | 46.0
3.682500 | 36.0 | 2000.0 | 9.000 | L1 | 11.7 | 10.0 | 46.0
3.729750 | 36.7 | 2000.0 | 9.000 | L1 | 11.7 | 9.3 | 46.0
3.750000 | 36.3 | 2000.0 | 9.000 | L1 | 11.7 | 9.7 | 46.0
3.819750 | 36.5 | 2000.0 | 9.000 | L1 | 11.7 | 9.5 | 46.0
3.887250 | 37.1 | 2000.0 | 9.000 | L1 | 11.7 | 8.9 | 46.0
3.939000 | 37.4 | 2000.0 | 9.000 | L1 | 11.7 | 8.6 | 46.0
3.952500 | 37.6 | 2000.0 | 9.000 | L1 | 11.7 | 8.4 | 46.0
3.954750 | 37.3 | 2000.0 | 9.000 | L1 | 11.7 | 8.7 | 46.0
3.990750 | 37.5 | 2000.0 | 9.000 | L1 | 11.7 | 8.5 | 46.0
4.022250 | 37.7 | 2000.0 | 9.000 | L1 | 11.7 | 8.3 | 46.0
4.026750 | 38.0 | 2000.0 | 9.000 | L1 | 11.7 | 8.0 | 46.0
4.087500 | 38.5 | 2000.0 | 9.000 | L1 | 11.7 | 7.5 | 46.0
4.092000 | 37.6 | 2000.0 | 9.000 | L1 | 11.7 | 8.4 | 46.0
4.152750 | 38.5 | 2000.0 | 9.000 | L1 | 11.6 | 7.5 | 46.0
4.159500 | 36.5 | 2000.0 | 9.000 | L1 | 11.6 | 9.5 | 46.0
4.218000 | 37.9 | 2000.0 | 9.000 | L1 | 11.6 | 8.1 | 46.0
4.227000 | 36.9 | 2000.0 | 9.000 | L1 | 11.6 | 9.1 | 46.0
