alper-bozcal/75W_XDPS/Tests/EMC/2023 05 23 Vestel RE CE Harmonics/Harmonic/123-1.rtf

Test Report ISMDPA

Report title: | R 001
Company Name: | EMTEST AG
Date of test: | 15:10 23.Mai 2023
Measurement file name: | DBC2-150W-2.rsd
Tester: | ABU
Standard used: | EN/IEC 61000-3-2 Ed.4 Long cyclic Equipment class A <= 200% of the limit (Limit factor: 1.00)
Observation time: | 200s
Windows width: | 10 periods - (EN/IEC 61000-4-7 Edition 2002 + A1:2008)
Customer:
E. U. T.:
Temperature :
Humidity :

Test Result
E. U. T.: | FAIL
Power Source: | FAIL

(Date) | | (Sign)

E. U. T. Result

Harmonic(s) > 200%:
Order (n): | None
Harmonic(s) with average > 90%:
Order (n): | 9, 11, 13, 15, 17, 19
Harmonic(s) between 150% and 200% during more than 10% of the test time or max. 10min:
Order (n): | None

Power Source Result

First dataset out of limit:
DS (time): | 1 (0.20s)
Harmonic(s) out of limit:
Order (n): | 15

Average harmonic current results
Hn | Ieff [A] | % of Limit | Limit [A] | Result
1 | 825.933E-3
2 | 893.614E-6 | | | PASS
3 | 733.651E-3 | 35.442 | 2.07 | PASS
4 | 3.517E-3 | | | PASS
5 | 665.484E-3 | 64.862 | 1.03 | PASS
6 | 1.644E-3 | | | PASS
7 | 574.681E-3 | 82.927 | 693.00E-3 | PASS
8 | 1.577E-3 | | | PASS
9 | 471.433E-3 | 130.954 | 360.00E-3 | FAIL
10 | 1.431E-3 | | | PASS
11 | 369.198E-3 | 124.309 | 297.00E-3 | FAIL
12 | 1.213E-3 | | | PASS
13 | 276.530E-3 | 146.312 | 189.00E-3 | FAIL
14 | 1.655E-3 | | | PASS
15 | 202.792E-3 | 150.217 | 135.00E-3 | FAIL
16 | 909.208E-6 | | | PASS
17 | 146.679E-3 | 123.141 | 119.11E-3 | FAIL
18 | 1.560E-3 | | | PASS
19 | 109.252E-3 | 102.509 | 106.58E-3 | FAIL
20 | 899.596E-6 | | | PASS
21 | 80.782E-3 | 83.776 | 96.43E-3 | PASS
22 | 1.022E-3 | | | PASS
23 | 62.611E-3 | 71.111 | 88.05E-3 | PASS
24 | 0.998E-3 | | | PASS
25 | 50.381E-3 | 62.199 | 81.00E-3 | PASS
26 | 994.809E-6 | | | PASS
27 | 50.047E-3 | 66.732 | 75.00E-3 | PASS
28 | 1.002E-3 | | | PASS
29 | 50.212E-3 | 71.905 | 69.83E-3 | PASS
30 | 980.573E-6 | | | PASS
31 | 50.087E-3 | 76.677 | 65.32E-3 | PASS
32 | 1.370E-3 | | | PASS
33 | 41.548E-3 | 67.710 | 61.36E-3 | PASS
34 | 903.690E-6 | | | PASS
35 | 30.820E-3 | 53.266 | 57.86E-3 | PASS
36 | 1.268E-3 | | | PASS
37 | 17.557E-3 | 32.080 | 54.73E-3 | PASS
38 | 877.430E-6 | | | PASS
39 | 18.597E-3 | 35.817 | 51.92E-3 | PASS
40 | 894.273E-6 | | | PASS

Harmonic currents less than 0.6% of the input current measured under the test conditions, or less than 5 mA, whichever is greater, are disregarded.

Maximum harmonic current results
Hn | Ieff [A] | % of Limit | Limit [A] | Result
1 | 827.413E-3
2 | 1.064E-3 | | | PASS
3 | 734.453E-3 | 15.966 | 4.60 | PASS
4 | 3.750E-3 | | | PASS
5 | 667.153E-3 | 29.261 | 2.28 | PASS
6 | 1.757E-3 | | | PASS
7 | 577.434E-3 | 37.496 | 1.54 | PASS
8 | 1.703E-3 | | | PASS
9 | 475.515E-3 | 59.439 | 800.00E-3 | PASS
10 | 1.525E-3 | | | PASS
11 | 373.998E-3 | 56.666 | 660.00E-3 | PASS
12 | 1.346E-3 | | | PASS
13 | 281.648E-3 | 67.059 | 420.00E-3 | PASS
14 | 1.782E-3 | | | PASS
15 | 208.244E-3 | 69.415 | 300.00E-3 | PASS
16 | 1.051E-3 | | | PASS
17 | 151.832E-3 | 57.360 | 264.70E-3 | PASS
18 | 1.689E-3 | | | PASS
19 | 113.680E-3 | 47.999 | 236.84E-3 | PASS
20 | 1.024E-3 | | | PASS
21 | 84.207E-3 | 39.297 | 214.28E-3 | PASS
22 | 1.136E-3 | | | PASS
23 | 64.943E-3 | 33.192 | 195.66E-3 | PASS
24 | 1.115E-3 | | | PASS
25 | 52.044E-3 | 28.913 | 180.00E-3 | PASS
26 | 1.100E-3 | | | PASS
27 | 51.538E-3 | 30.924 | 166.66E-3 | PASS
28 | 1.128E-3 | | | PASS
29 | 51.504E-3 | 33.190 | 155.18E-3 | PASS
30 | 1.072E-3 | | | PASS
31 | 51.557E-3 | 35.518 | 145.16E-3 | PASS
32 | 1.485E-3 | | | PASS
33 | 43.360E-3 | 31.798 | 136.36E-3 | PASS
34 | 995.696E-6 | | | PASS
35 | 32.963E-3 | 25.636 | 128.58E-3 | PASS
36 | 1.376E-3 | | | PASS
37 | 19.587E-3 | 16.105 | 121.62E-3 | PASS
38 | 986.349E-6 | | | PASS
39 | 19.338E-3 | 16.760 | 115.38E-3 | PASS
40 | 980.031E-6 | | | PASS

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
33 | 50.96E-3 | 0.022 | 0.1 | PASS
34 | 7.28E-3 | 0.003 | 0.1 | PASS
35 | 109.64E-3 | 0.048 | 0.1 | PASS
36 | 6.00E-3 | 0.003 | 0.1 | PASS
37 | 59.48E-3 | 0.026 | 0.1 | PASS
38 | 8.12E-3 | 0.004 | 0.1 | PASS
39 | 69.80E-3 | 0.030 | 0.1 | PASS
40 | 7.98E-3 | 0.003 | 0.1 | PASS
