alper-bozcal/75W_XDPS/Tests/EMC/2023 05 23 Vestel RE CE Harmonics/Harmonic/123.rtf

Test Report ISMDPA

Report title: | R 001
Company Name: | EMTEST AG
Date of test: | 14:50 23.Mai 2023
Measurement file name: | Harmonics_3_2_Ed4.rsd
Tester: | ABU
Standard used: | EN/IEC 61000-3-2 Ed.4 Long cyclic Equipment class A <= 200% of the limit (Limit factor: 1.00)
Observation time: | 200s
Windows width: | 10 periods - (EN/IEC 61000-4-7 Edition 2002 + A1:2008)
Customer:
E. U. T.:
Temperature :
Humidity :

Test Result
E. U. T.: | FAIL
Power Source: | FAIL

(Date) | | (Sign)

E. U. T. Result

Harmonic(s) > 200%:
Order (n): | None
Harmonic(s) with average > 90%:
Order (n): | 9, 11, 13, 15, 17
Harmonic(s) between 150% and 200% during more than 10% of the test time or max. 10min:
Order (n): | None

Power Source Result

First dataset out of limit:
DS (time): | 1 (0.20s)
Harmonic(s) out of limit:
Order (n): | 15

Average harmonic current results
Hn | Ieff [A] | % of Limit | Limit [A] | Result
1 | 811.518E-3
2 | 642.072E-6 | | | PASS
3 | 719.938E-3 | 34.780 | 2.07 | PASS
4 | 3.566E-3 | | | PASS
5 | 653.336E-3 | 63.678 | 1.03 | PASS
6 | 934.325E-6 | | | PASS
7 | 564.583E-3 | 81.469 | 693.00E-3 | PASS
8 | 941.791E-6 | | | PASS
9 | 463.454E-3 | 128.737 | 360.00E-3 | FAIL
10 | 866.473E-6 | | | PASS
11 | 363.068E-3 | 122.245 | 297.00E-3 | FAIL
12 | 835.571E-6 | | | PASS
13 | 271.763E-3 | 143.790 | 189.00E-3 | FAIL
14 | 1.305E-3 | | | PASS
15 | 198.745E-3 | 147.218 | 135.00E-3 | FAIL
16 | 831.282E-6 | | | PASS
17 | 142.896E-3 | 119.965 | 119.11E-3 | FAIL
18 | 1.559E-3 | | | PASS
19 | 105.483E-3 | 98.972 | 106.58E-3 | PASS
20 | 821.918E-6 | | | PASS
21 | 76.827E-3 | 79.675 | 96.43E-3 | PASS
22 | 1.157E-3 | | | PASS
23 | 58.067E-3 | 65.950 | 88.05E-3 | PASS
24 | 892.345E-6 | | | PASS
25 | 45.253E-3 | 55.867 | 81.00E-3 | PASS
26 | 853.942E-6 | | | PASS
27 | 45.446E-3 | 60.597 | 75.00E-3 | PASS
28 | 850.018E-6 | | | PASS
29 | 47.050E-3 | 67.376 | 69.83E-3 | PASS
30 | 871.189E-6 | | | PASS
31 | 48.354E-3 | 74.024 | 65.32E-3 | PASS
32 | 1.165E-3 | | | PASS
33 | 40.926E-3 | 66.695 | 61.36E-3 | PASS
34 | 810.470E-6 | | | PASS
35 | 30.714E-3 | 53.083 | 57.86E-3 | PASS
36 | 1.223E-3 | | | PASS
37 | 15.826E-3 | 28.917 | 54.73E-3 | PASS
38 | 809.685E-6 | | | PASS
39 | 14.686E-3 | 28.285 | 51.92E-3 | PASS
40 | 965.600E-6 | | | PASS

Harmonic currents less than 0.6% of the input current measured under the test conditions, or less than 5 mA, whichever is greater, are disregarded.

Maximum harmonic current results
Hn | Ieff [A] | % of Limit | Limit [A] | Result
1 | 817.132E-3
2 | 809.212E-6 | | | PASS
3 | 725.228E-3 | 15.766 | 4.60 | PASS
4 | 3.718E-3 | | | PASS
5 | 657.088E-3 | 28.820 | 2.28 | PASS
6 | 1.051E-3 | | | PASS
7 | 566.398E-3 | 36.779 | 1.54 | PASS
8 | 1.094E-3 | | | PASS
9 | 466.281E-3 | 58.285 | 800.00E-3 | PASS
10 | 1.125E-3 | | | PASS
11 | 366.699E-3 | 55.560 | 660.00E-3 | PASS
12 | 1.064E-3 | | | PASS
13 | 276.349E-3 | 65.797 | 420.00E-3 | PASS
14 | 1.495E-3 | | | PASS
15 | 203.173E-3 | 67.724 | 300.00E-3 | PASS
16 | 1.023E-3 | | | PASS
17 | 146.959E-3 | 55.519 | 264.70E-3 | PASS
18 | 1.964E-3 | | | PASS
19 | 108.377E-3 | 45.760 | 236.84E-3 | PASS
20 | 963.726E-6 | | | PASS
21 | 78.899E-3 | 36.820 | 214.28E-3 | PASS
22 | 1.410E-3 | | | PASS
23 | 59.489E-3 | 30.404 | 195.66E-3 | PASS
24 | 1.072E-3 | | | PASS
25 | 46.749E-3 | 25.972 | 180.00E-3 | PASS
26 | 1.023E-3 | | | PASS
27 | 46.939E-3 | 28.164 | 166.66E-3 | PASS
28 | 1.020E-3 | | | PASS
29 | 47.958E-3 | 30.905 | 155.18E-3 | PASS
30 | 1.060E-3 | | | PASS
31 | 49.021E-3 | 33.770 | 145.16E-3 | PASS
32 | 1.367E-3 | | | PASS
33 | 42.138E-3 | 30.902 | 136.36E-3 | PASS
34 | 958.548E-6 | | | PASS
35 | 32.262E-3 | 25.091 | 128.58E-3 | PASS
36 | 1.612E-3 | | | PASS
37 | 17.579E-3 | 14.454 | 121.62E-3 | PASS
38 | 953.904E-6 | | | PASS
39 | 16.203E-3 | 14.043 | 115.38E-3 | PASS
40 | 1.187E-3 | | | PASS

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
33 | 48.55E-3 | 0.021 | 0.1 | PASS
34 | 7.78E-3 | 0.003 | 0.1 | PASS
35 | 106.44E-3 | 0.046 | 0.1 | PASS
36 | 8.24E-3 | 0.004 | 0.1 | PASS
37 | 57.38E-3 | 0.025 | 0.1 | PASS
38 | 8.61E-3 | 0.004 | 0.1 | PASS
39 | 69.83E-3 | 0.030 | 0.1 | PASS
40 | 8.26E-3 | 0.004 | 0.1 | PASS
