alper-bozcal/75W_XDPS/Tests/EMC/2023 05 23 Vestel RE CE Harmonics/Harmonic/DBC2-75W-1.rtf

Test Report ISMDPA

Report title: | R 001
Company Name: | EMTEST AG
Date of test: | 15:29 23.Mai 2023
Measurement file name: | Harmonics_3_2_Ed4.rsd
Tester: | ABU
Standard used: | EN/IEC 61000-3-2 Ed.4 Long cyclic Equipment class A <= 200% of the limit (Limit factor: 1.00)
Observation time: | 200s
Windows width: | 10 periods - (EN/IEC 61000-4-7 Edition 2002 + A1:2008)
Customer:
E. U. T.:
Temperature :
Humidity :

Test Result
E. U. T.: | PASS
Power Source: | PASS

(Date) | | (Sign)

E. U. T. Result

Harmonic(s) > 200%:
Order (n): | None
Harmonic(s) with average > 90%:
Order (n): | None
Harmonic(s) between 150% and 200% during more than 10% of the test time or max. 10min:
Order (n): | None

Power Source Result

First dataset out of limit:
DS (time): | None
Harmonic(s) out of limit:
Order (n): | None

Average harmonic current results
Hn | Ieff [A] | % of Limit | Limit [A] | Result
1 | 404.933E-3
2 | 1.016E-3 | | | PASS
3 | 369.793E-3 | 17.864 | 2.07 | PASS
4 | 3.228E-3 | | | PASS
5 | 342.241E-3 | 33.357 | 1.03 | PASS
6 | 1.444E-3 | | | PASS
7 | 304.003E-3 | 43.868 | 693.00E-3 | PASS
8 | 1.384E-3 | | | PASS
9 | 257.991E-3 | 71.664 | 360.00E-3 | PASS
10 | 1.270E-3 | | | PASS
11 | 208.439E-3 | 70.182 | 297.00E-3 | PASS
12 | 1.181E-3 | | | PASS
13 | 158.191E-3 | 83.699 | 189.00E-3 | PASS
14 | 1.682E-3 | | | PASS
15 | 111.508E-3 | 82.599 | 135.00E-3 | PASS
16 | 946.705E-6 | | | PASS
17 | 72.775E-3 | 61.096 | 119.11E-3 | PASS
18 | 1.629E-3 | | | PASS
19 | 46.007E-3 | 43.167 | 106.58E-3 | PASS
20 | 856.085E-6 | | | PASS
21 | 35.941E-3 | 37.273 | 96.43E-3 | PASS
22 | 905.667E-6 | | | PASS
23 | 36.852E-3 | 41.855 | 88.05E-3 | PASS
24 | 811.904E-6 | | | PASS
25 | 38.860E-3 | 47.975 | 81.00E-3 | PASS
26 | 866.938E-6 | | | PASS
27 | 36.893E-3 | 49.193 | 75.00E-3 | PASS
28 | 814.157E-6 | | | PASS
29 | 32.335E-3 | 46.304 | 69.83E-3 | PASS
30 | 843.795E-6 | | | PASS
31 | 23.836E-3 | 36.490 | 65.32E-3 | PASS
32 | 1.210E-3 | | | PASS
33 | 16.774E-3 | 27.335 | 61.36E-3 | PASS
34 | 827.450E-6 | | | PASS
35 | 11.149E-3 | 19.269 | 57.86E-3 | PASS
36 | 1.156E-3 | | | PASS
37 | 11.802E-3 | 21.564 | 54.73E-3 | PASS
38 | 802.386E-6 | | | PASS
39 | 12.749E-3 | 24.554 | 51.92E-3 | PASS
40 | 823.330E-6 | | | PASS

Harmonic currents less than 0.6% of the input current measured under the test conditions, or less than 5 mA, whichever is greater, are disregarded.

Maximum harmonic current results
Hn | Ieff [A] | % of Limit | Limit [A] | Result
1 | 411.605E-3
2 | 1.165E-3 | | | PASS
3 | 375.652E-3 | 8.166 | 4.60 | PASS
4 | 3.606E-3 | | | PASS
5 | 347.001E-3 | 15.219 | 2.28 | PASS
6 | 1.583E-3 | | | PASS
7 | 307.246E-3 | 19.951 | 1.54 | PASS
8 | 1.502E-3 | | | PASS
9 | 259.456E-3 | 32.432 | 800.00E-3 | PASS
10 | 1.428E-3 | | | PASS
11 | 210.329E-3 | 31.868 | 660.00E-3 | PASS
12 | 1.342E-3 | | | PASS
13 | 160.536E-3 | 38.223 | 420.00E-3 | PASS
14 | 1.812E-3 | | | PASS
15 | 114.256E-3 | 38.085 | 300.00E-3 | PASS
16 | 1.072E-3 | | | PASS
17 | 75.943E-3 | 28.690 | 264.70E-3 | PASS
18 | 1.770E-3 | | | PASS
19 | 48.281E-3 | 20.386 | 236.84E-3 | PASS
20 | 991.514E-6 | | | PASS
21 | 36.818E-3 | 17.182 | 214.28E-3 | PASS
22 | 1.029E-3 | | | PASS
23 | 37.933E-3 | 19.387 | 195.66E-3 | PASS
24 | 907.830E-6 | | | PASS
25 | 39.535E-3 | 21.964 | 180.00E-3 | PASS
26 | 985.634E-6 | | | PASS
27 | 37.351E-3 | 22.412 | 166.66E-3 | PASS
28 | 919.920E-6 | | | PASS
29 | 33.147E-3 | 21.361 | 155.18E-3 | PASS
30 | 942.986E-6 | | | PASS
31 | 25.090E-3 | 17.285 | 145.16E-3 | PASS
32 | 1.306E-3 | | | PASS
33 | 18.073E-3 | 13.254 | 136.36E-3 | PASS
34 | 966.799E-6 | | | PASS
35 | 11.764E-3 | 9.149 | 128.58E-3 | PASS
36 | 1.269E-3 | | | PASS
37 | 12.535E-3 | 10.307 | 121.62E-3 | PASS
38 | 904.732E-6 | | | PASS
39 | 13.522E-3 | 11.719 | 115.38E-3 | PASS
40 | 942.682E-6 | | | PASS

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
33 | 36.82E-3 | 0.016 | 0.1 | PASS
34 | 6.44E-3 | 0.003 | 0.1 | PASS
35 | 46.56E-3 | 0.020 | 0.1 | PASS
36 | 6.81E-3 | 0.003 | 0.1 | PASS
37 | 51.02E-3 | 0.022 | 0.1 | PASS
38 | 7.16E-3 | 0.003 | 0.1 | PASS
39 | 21.57E-3 | 0.009 | 0.1 | PASS
40 | 6.70E-3 | 0.003 | 0.1 | PASS
