alper-bozcal/75W_XDPS/Tests/EMC/2023 05 23 Vestel RE CE Harmonics/Harmonic/SON.rtf

Test Report ISMDPA

Report title: | R 001
Company Name: | EMTEST AG
Date of test: | 15:35 23.Mai 2023
Measurement file name: | DBC2-150-4.rsd
Tester: | ABU
Standard used: | EN/IEC 61000-3-2 Ed.4 Long cyclic Equipment class A <= 200% of the limit (Limit factor: 1.00)
Observation time: | 200s
Windows width: | 10 periods - (EN/IEC 61000-4-7 Edition 2002 + A1:2008)
Customer:
E. U. T.:
Temperature :
Humidity :

Test Result
E. U. T.: | FAIL
Power Source: | FAIL

(Date) | | (Sign)

E. U. T. Result

Harmonic(s) > 200%:
Order (n): | None
Harmonic(s) with average > 90%:
Order (n): | 9, 11, 13, 15, 17
Harmonic(s) between 150% and 200% during more than 10% of the test time or max. 10min:
Order (n): | None

Power Source Result

First dataset out of limit:
DS (time): | 7 (1.40s)
Harmonic(s) out of limit:
Order (n): | 11, 15

Average harmonic current results
Hn | Ieff [A] | % of Limit | Limit [A] | Result
1 | 804.364E-3
2 | 636.821E-6 | | | PASS
3 | 722.264E-3 | 34.892 | 2.07 | PASS
4 | 3.042E-3 | | | PASS
5 | 668.012E-3 | 65.108 | 1.03 | PASS
6 | 1.110E-3 | | | PASS
7 | 593.008E-3 | 85.571 | 693.00E-3 | PASS
8 | 1.071E-3 | | | PASS
9 | 502.632E-3 | 139.620 | 360.00E-3 | FAIL
10 | 929.871E-6 | | | PASS
11 | 405.915E-3 | 136.672 | 297.00E-3 | FAIL
12 | 935.713E-6 | | | PASS
13 | 308.021E-3 | 162.974 | 189.00E-3 | FAIL
14 | 1.521E-3 | | | PASS
15 | 217.884E-3 | 161.395 | 135.00E-3 | FAIL
16 | 855.999E-6 | | | PASS
17 | 138.827E-3 | 116.549 | 119.11E-3 | FAIL
18 | 1.545E-3 | | | PASS
19 | 81.165E-3 | 76.155 | 106.58E-3 | PASS
20 | 815.320E-6 | | | PASS
21 | 50.165E-3 | 52.024 | 96.43E-3 | PASS
22 | 862.291E-6 | | | PASS
23 | 50.191E-3 | 57.005 | 88.05E-3 | PASS
24 | 836.810E-6 | | | PASS
25 | 54.287E-3 | 67.021 | 81.00E-3 | PASS
26 | 802.555E-6 | | | PASS
27 | 54.340E-3 | 72.456 | 75.00E-3 | PASS
28 | 813.974E-6 | | | PASS
29 | 44.552E-3 | 63.800 | 69.83E-3 | PASS
30 | 811.097E-6 | | | PASS
31 | 33.016E-3 | 50.544 | 65.32E-3 | PASS
32 | 1.242E-3 | | | PASS
33 | 17.890E-3 | 29.155 | 61.36E-3 | PASS
34 | 807.920E-6 | | | PASS
35 | 7.627E-3 | | | PASS
36 | 1.194E-3 | | | PASS
37 | 12.531E-3 | 22.897 | 54.73E-3 | PASS
38 | 774.633E-6 | | | PASS
39 | 23.101E-3 | 44.492 | 51.92E-3 | PASS
40 | 773.132E-6 | | | PASS

Harmonic currents less than 0.6% of the input current measured under the test conditions, or less than 5 mA, whichever is greater, are disregarded.

Maximum harmonic current results
Hn | Ieff [A] | % of Limit | Limit [A] | Result
1 | 809.748E-3
2 | 732.500E-6 | | | PASS
3 | 727.225E-3 | 15.809 | 4.60 | PASS
4 | 3.436E-3 | | | PASS
5 | 671.593E-3 | 29.456 | 2.28 | PASS
6 | 1.262E-3 | | | PASS
7 | 595.510E-3 | 38.670 | 1.54 | PASS
8 | 1.254E-3 | | | PASS
9 | 505.139E-3 | 63.142 | 800.00E-3 | PASS
10 | 1.084E-3 | | | PASS
11 | 409.868E-3 | 62.101 | 660.00E-3 | PASS
12 | 1.049E-3 | | | PASS
13 | 313.024E-3 | 74.530 | 420.00E-3 | PASS
14 | 1.655E-3 | | | PASS
15 | 223.154E-3 | 74.385 | 300.00E-3 | PASS
16 | 963.295E-6 | | | PASS
17 | 143.491E-3 | 54.209 | 264.70E-3 | PASS
18 | 1.644E-3 | | | PASS
19 | 84.239E-3 | 35.568 | 236.84E-3 | PASS
20 | 894.935E-6 | | | PASS
21 | 51.890E-3 | 24.216 | 214.28E-3 | PASS
22 | 966.087E-6 | | | PASS
23 | 52.975E-3 | 27.075 | 195.66E-3 | PASS
24 | 957.677E-6 | | | PASS
25 | 55.854E-3 | 31.030 | 180.00E-3 | PASS
26 | 912.814E-6 | | | PASS
27 | 55.102E-3 | 33.062 | 166.66E-3 | PASS
28 | 956.154E-6 | | | PASS
29 | 45.971E-3 | 29.624 | 155.18E-3 | PASS
30 | 930.536E-6 | | | PASS
31 | 34.944E-3 | 24.073 | 145.16E-3 | PASS
32 | 1.322E-3 | | | PASS
33 | 19.834E-3 | 14.546 | 136.36E-3 | PASS
34 | 912.346E-6 | | | PASS
35 | 8.946E-3 | | | PASS
36 | 1.305E-3 | | | PASS
37 | 14.276E-3 | 11.738 | 121.62E-3 | PASS
38 | 883.872E-6 | | | PASS
39 | 24.311E-3 | 21.070 | 115.38E-3 | PASS
40 | 860.184E-6 | | | PASS

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
33 | 68.79E-3 | 0.030 | 0.1 | PASS
34 | 6.95E-3 | 0.003 | 0.1 | PASS
35 | 77.53E-3 | 0.034 | 0.1 | PASS
36 | 7.62E-3 | 0.003 | 0.1 | PASS
37 | 60.20E-3 | 0.026 | 0.1 | PASS
38 | 8.54E-3 | 0.004 | 0.1 | PASS
39 | 38.71E-3 | 0.017 | 0.1 | PASS
40 | 6.73E-3 | 0.003 | 0.1 | PASS
