alper-bozcal/75W_XDPS/Tests/EMC/2023 04 29 Numune Gönderimi/DBC2-150W-5-1510.pdf

# DBC2

19.04.2023 16:01:07

### 1 / 1 - Page 1 of 2

Heading | DBC2-150W-4-1510

## Meas Type Equipment under Test DBC2

Manufacturer | ENKO
OP Condition | p
Operator | C.U.
Test Spec | J

## Settings

Scan Start | 150.000000000 kHz
Scan Stop | 30.000000000 MHz
RBW | 9.0 kHz
IF RBW | 10.0 kHz
Meas Time | 1.0 s
RF Att | 10.0 dB
Preamp State | Off
Preamp Value | 0.0 dB
Input Selection | INP1
Input Coupling | AC
Scan Type | TD Scan
Transducer | ENV432 ENKO.TDF

## Scan Table

Scan Start | 150.000000000 kHz
Scan Stop | 30.000000000 MHz
Scan Type | TD Scan
Transducer | ENV432 ENKO.TDF
Detector | Trace 1: Max Peak Trace 2: Average
Start
Frequency

Stop
Frequency
Step Size | RBW | Meas Time | RF Atten | Preamp | Input
150.000 kHz | 30.000 MHz | 2.250 kHz | 9.0 kHz | 10.0 ms 10.0 dB 0.0 dB INPUT1

## Peak List

Margin | 6.0 dB
Peaks | 25
Trace | Frequency | Level (dBµV) | Phase | Detector | Delta Limit/dB
1 188.250000000 kHz | 58.95 | L1 Positive Peak | -5.16
1 | 3.563250000 MHz | 50.68 | L1 Positive Peak | -5.32
1 | 12.819750000 MHz | 55.55 | L1 Positive Peak | -4.45
1 | 13.573500000 MHz | 55.38 | L1 Positive Peak | -4.62
2 | 13.573500000 MHz | 44.48 | L1 | Average | -5.52
2 | 16.878750000 MHz | 45.39 | N | Average | -4.61
1 | 17.067750000 MHz | 56.86 | N Positive Peak | -3.14

## Final Results

Meas Time | 1.0 s
Margin | 6.0 dB
Peaks | 25
Trace | Frequency | Level (dBµV) | Phase | Detector | Delta Limit/dB
1 188.250000000 kHz | 57.77 | L1 | Quasi Peak | -6.34
1 | 3.563250000 MHz | 46.77 | L1 | Quasi Peak | -9.23
1 | 12.819750000 MHz | 50.65 | L1 | Quasi Peak | -9.35
1 | 13.573500000 MHz | 50.28 | L1 | Quasi Peak | -9.72
2 | 13.573500000 MHz | 43.47 | L1 | CISPR AV | -6.53
2 | 16.878750000 MHz | 43.71 | L1 | CISPR AV | -6.29
1 | 17.067750000 MHz | 52.19 | N | Quasi Peak | -7.81

19.04.2023 16:01:07
Heading | DBC2-150W-4-1510

## Meas Type Equipment under Test DBC2

Manufacturer | ENKO
OP Condition | p
Operator | C.U.
Test Spec | J

### 1 / 1 - Page 2 of 2

## Scan Diagram

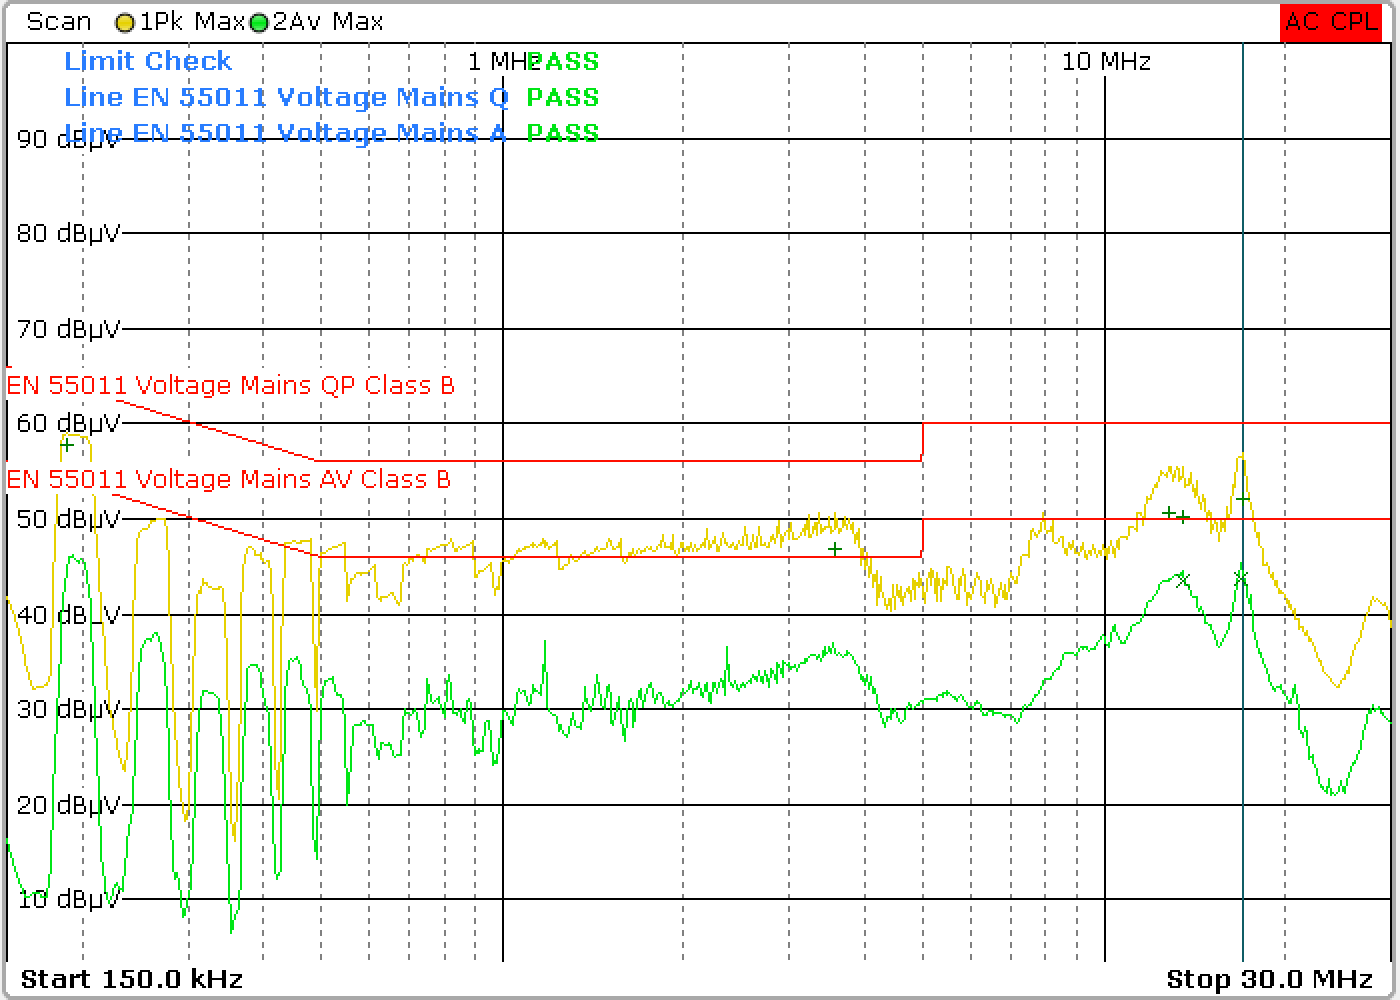
[picture p81: figure]
