alper-bozcal/75W_XDPS/Tests/EMC/2023 04 29 Numune Gönderimi/DBC2-150W-8-1510.pdf

# DBC2

19.04.2023 16:04:01

### 1 / 1 - Page 1 of 2

Heading | DBC2-150W-8-1510

## Meas Type Equipment under Test DBC2

Manufacturer | ENKO
OP Condition | p
Operator | C.U.
Test Spec | J

## Settings

Scan Start | 150.000000000 kHz
Scan Stop | 30.000000000 MHz
RBW | 9.0 kHz
IF RBW | 10.0 kHz
Meas Time | 1.0 s
RF Att | 10.0 dB
Preamp State | Off
Preamp Value | 0.0 dB
Input Selection | INP1
Input Coupling | AC
Scan Type | TD Scan
Transducer | ENV432 ENKO.TDF

## Scan Table

Scan Start | 150.000000000 kHz
Scan Stop | 30.000000000 MHz
Scan Type | TD Scan
Transducer | ENV432 ENKO.TDF
Detector | Trace 1: Max Peak Trace 2: Average
Start
Frequency

Stop
Frequency
Step Size | RBW | Meas Time | RF Atten | Preamp | Input
150.000 kHz | 30.000 MHz | 2.250 kHz | 9.0 kHz | 10.0 ms 10.0 dB 0.0 dB INPUT1

## Peak List

Margin | 6.0 dB
Peaks | 25
Trace | Frequency | Level (dBµV) | Phase | Detector | Delta Limit/dB
1 188.250000000 kHz | 58.54 | L1 Positive Peak | -5.57
1 | 3.554250000 MHz | 50.17 | L1 Positive Peak | -5.83
1 | 12.117750000 MHz | 54.35 | L1 Positive Peak | -5.65
2 | 13.053750000 MHz | 44.12 | L1 | Average | -5.88
1 | 13.056000000 MHz | 55.76 | L1 Positive Peak | -4.24
1 | 16.809000000 MHz | 55.41 | N Positive Peak | -4.59
2 | 16.908000000 MHz | 44.03 | L1 | Average | -5.97

## Final Results

Meas Time | 1.0 s
Margin | 6.0 dB
Peaks | 25
Trace | Frequency | Level (dBµV) | Phase | Detector | Delta Limit/dB
1 188.250000000 kHz | 56.95 | L1 | Quasi Peak | -7.16
1 | 3.554250000 MHz | 46.07 | L1 | Quasi Peak | -9.93
1 | 12.117750000 MHz | 47.19 | L1 | Quasi Peak | -12.81
2 | 13.053750000 MHz | 43.54 | L1 | CISPR AV | -6.46
1 | 13.056000000 MHz | 49.14 | L1 | Quasi Peak | -10.86
1 | 16.809000000 MHz | 49.86 | N | Quasi Peak | -10.14
2 | 16.908000000 MHz | 41.36 | L1 | CISPR AV | -8.64

19.04.2023 16:04:01
Heading | DBC2-150W-8-1510

## Meas Type Equipment under Test DBC2

Manufacturer | ENKO
OP Condition | p
Operator | C.U.
Test Spec | J

### 1 / 1 - Page 2 of 2

## Scan Diagram

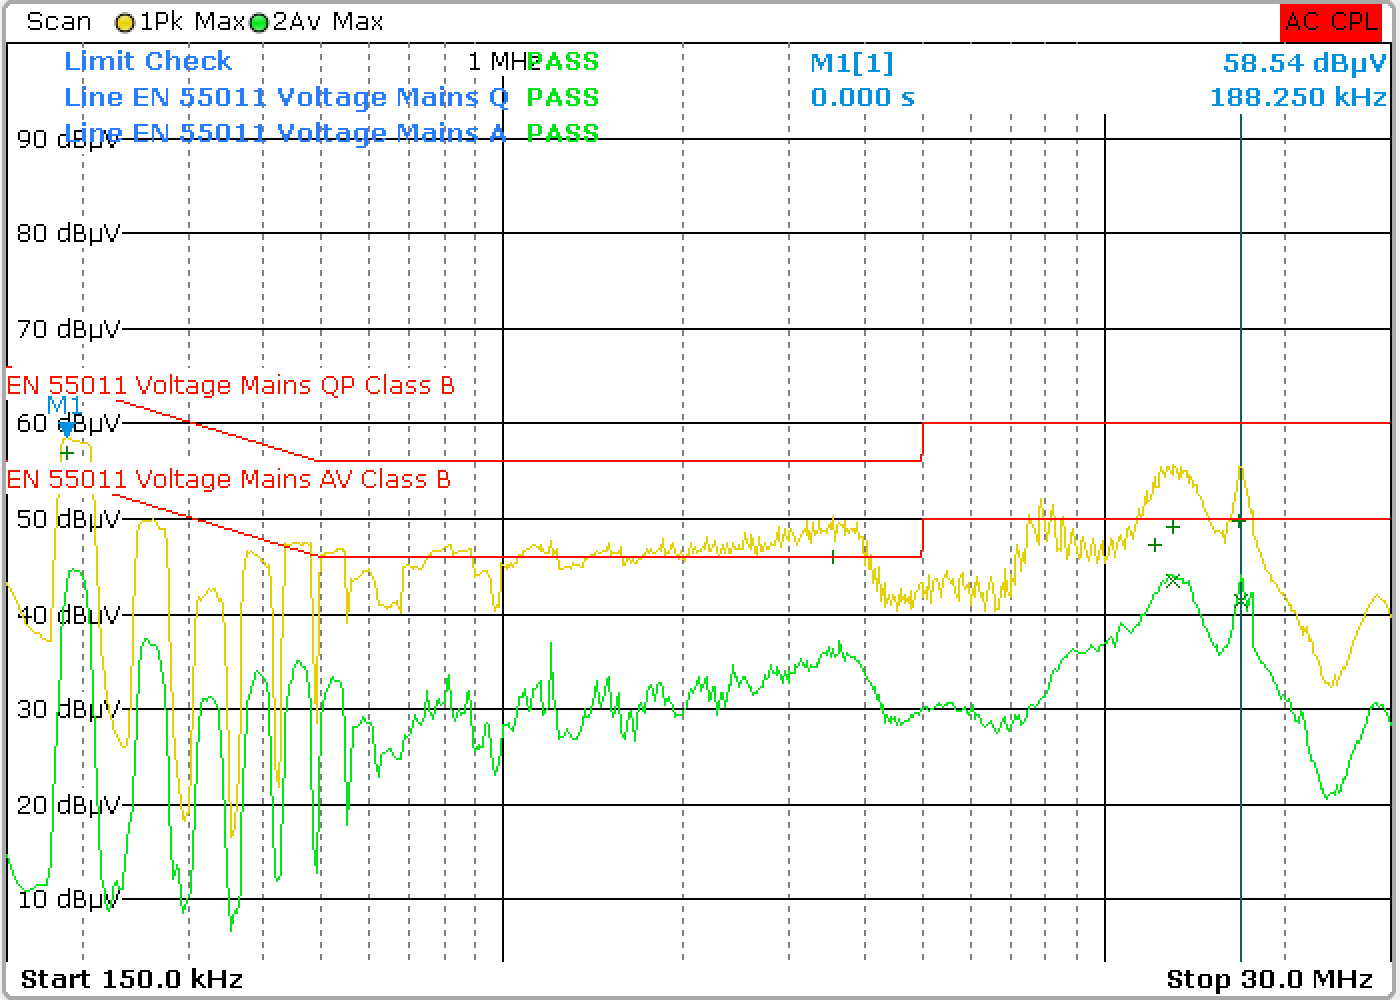
[picture p82: figure]
