alper-bozcal/75W_XDPS/Simulations/ADC_IOUT/ADC Calibration.ods

Sheet: VOUT
SET | SCADA | ÖLÇ. | FARK | % | 7 OFF ile SCADA | 7 OFF ile Ölç
1500 | 1495 | 1501 | 6 | 99,6666666666667 | 1491 | 1489
1550 | 1542 |  | -1542 | 99,4838709677419 | 1542 | 1540
1600 | 1593 | 1598 | 5 | 99,5625
1700 | 1691 | 1697 | 6 | 99,4705882352941
1800 | 1794 | 1799 | 5 | 99,6666666666667
1900 | 1893 | 1899 | 6 | 99,6315789473684
2000 | 1994 | 1999 | 5 | 99,7
2100 | 2094 | 2100 | 6 | 99,7142857142857
2200 | 2192 | 2198 | 6 | 99,6363636363636
2300 | 2292 | 2299 | 7 | 99,6521739130435
2400 | 2393 | 2400 | 7 | 99,7083333333333
2500 | 2499 | 2506 | 7 | 99,96
2600 | 2604 | 2612 | 8 | 100,153846153846
2700 | 2710 | 2717 | 7 | 100,37037037037
2800 | 2806 | 2814 | 8 | 100,214285714286 | 2807 | 2807
2900 | 2908 | 2915 | 7 | 100,275862068966
3000 | 3006 | 3014 | 8 | 100,2 | 3005 | 3008
1200 | 1207 | 1211 | 4 | 100,583333333333 | 1210 | 1207
1250 | 1247 | 1250 | 3 | 99,76 | 1254 | 1251
1350 | 1342 | 1346 | 4 | 99,4074074074074
1450 | 1440 | 1445 | 5 | 99,3103448275862
0 | 130 | 118 | -12 | #BÖLÜ/0!
2150 | 2144 | 2151
2175 | 2166 | 2173
 |  |  |  |  |  | (V(i_out_adc)*4095/3.3*0.604/100)-I(Rload)
 |  |  |  |  |  | 7,49509090909091
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
