alper-bozcal/75W_XDPS/Tests/Harmonik/2023 05 16 Alternator Class A.ods

Harmonics Number | Limits | Tested I[mA] | Vestel Peak | MB RMS | *sqrt(2) | Vestel Avg | MB 2 RMS
1 | 0 | 778,76 | 809 | 805 | 1138 | 804 | 890
2 | 1080 |  |  |  | 0
3 | 2300 | 679,27 | 727 | 730 | 1032 | 722 | 742
4 | 430 |  |  |  | 0
5 | 1140 | 555,76 | 671 | 671 | 949 | 668 | 686
6 | 300 |  |  |  | 0
7 | 770 | 425,4 | 595 | 593 | 839 | 593 | 596
8 |  |  |  |  | 0
9 | 400 | 291,6 | 505 | 506 | 716 | 502 | 503
10 |  |  |  |  | 0
11 | 330 | 164,67 | 409 | 423 | 598 | 405 | 411
12 |  |  |  |  | 0
13 | 210 | 102,92 | 313 | 346 | 489 | 308 | 331
14 |  |  |  |  | 0
15 | 150 | 78,9 | 223 | 283 | 400 | 217 | 267
16 |  |  |  |  | 0
17 | 132,4 | 85,77 | 143 | 232 | 328 | 138 | 217
18 |  |  |  |  | 0
19 | 118,4 | 54,89 | 84 | 189 | 267 | 81 | 177
20 |  |  |  |  | 0
21 | 107,1 | 41,17 | 51 | 150 | 212 | 50 | 141
22
23 | 97,8 |  | 52 |  |  | 50 | 107
24
25 | 90,0 |  | 55 |  |  | 54 | 74,1
26
27 | 83,3 |  | 55 |  |  | 54 | 48,4
28
29 | 77,6 |  | 45 |  |  | 44 | 32,4
30
31 | 72,6 |  | 34 |  |  | 33 | 27,2
32 |  | Harmonics tested with Alternator
33 | 68,2 |  |  |  |  |  | 25,9
34
35 | 64,3 |  |  |  |  |  | 22,3
36
37 | 60,8 |  |  |  |  |  | 16,4
38
39 | 57,7 |  |  |  |  |  | 10,6
40
