alper-bozcal/75W_XDPS/Tests/Harmonik/Class A değerleri.ods

 |  | mA
1 | 0
2 | 1080
3 | 2300
4 | 430
5 | 1140
6 | 300
7 | 770
8 |  | 230
9 | 400 | 250
10 |  | 184
11 | 330 | 204,545
12 |  | 153,333
13 | 210 | 173,077
14 |  | 131,429
15 |  | 150
16 |  | 115
17 |  | 132,353
18 |  | 102,222
19 |  | 118,421
20 |  | 92
21 |  | 107,143
22 |  | 83,636
23 |  | 97,826
24 |  | 76,667
25 |  | 90
26 |  | 70,769
27 |  | 83,333
28 |  | 65,714
29 |  | 77,586
30 |  | 61,333
31 |  | 72,581
32 |  | 57,5
33 |  | 68,182
34 |  | 54,118
35 |  | 64,286
36 |  | 51,111
37 |  | 60,811
38 |  | 48,421
39 |  | 57,692
40 |  | 46
