alper-bozcal/75W_XDPS/Tests/PWM/PWM Test.ods

Sheet: Voltage
PWM | Vout | PWM | Vout
0 | 1204 | 150 | 1207
1 | 1206 | 151 | 1207
2 | 1206 | 152 | 1207
3 | 1206 | 153 | 1207
4 | 1206 | 154 | 1207
5 | 1206 | 155 | 1207
6 | 1206 | 156 | 1207
7 | 1206 | 157 | 1207
8 | 1206 | 158 | 1207
9 | 1206 | 159 | 1207
10 | 1206 | 160 | 1207
11 | 1206 | 161 | 1208
12 | 1206 | 162 | 1208
13 | 1206 | 163 | 1208
14 | 1206 | 164 | 1209
15 | 1206 | 165 | 1209
16 | 1206 | 166 | 1209
17 | 1206 | 167 | 1210
18 | 1206 | 168 | 1210
19 | 1206 | 169 | 1211
20 | 1206 | 170 | 1211
21 | 1206 | 171 | 1212
22 | 1206 | 172 | 1213
23 | 1206 | 173 | 1214
24 | 1206 | 174 | 1215
25 | 1206 | 175 | 1215
26 | 1206 | 176 | 1215
27 | 1206 | 177 | 1216
28 | 1206 | 178 | 1217
29 | 1206 | 179 | 1219
30 | 1206 | 180 | 1220
31 | 1206 | 181 | 1221
32 | 1206 | 182 | 1222
33 | 1206 | 183 | 1223
34 | 1206 | 184 | 1224
35 | 1206 | 185 | 1226
36 | 1206 | 186 | 1227
37 | 1206 | 187 | 1229
38 | 1206 | 188 | 1230
39 | 1206 | 189 | 1232
40 | 1206 | 190 | 1233
41 | 1206 | 191 | 1235
42 | 1206 | 192 | 1237
43 | 1206 | 193 | 1239
44 | 1206 | 194 | 1241
45 | 1206 | 195 | 1243
46 | 1206 | 196 | 1245
47 | 1206 | 197 | 1247
48 | 1206 | 198 | 1249
49 | 1206 | 199 | 1251
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
