alper-bozcal/75W_XDPS/Tests/EMC/2023 05 23 Vestel RE CE Harmonics/2023 05 23 Vestel Testleri.ods

Sheet: DBC2 75W
75W Ürün Harmonik testlerini geçti. | 75W Conducted teste sokulmadı | 75W radiated teste sokuldu fakat sonuçlar arasında bulunamadı

Sheet: DBC2 150W
150W Ürünü Harmonik testlerini geçemedi.
150W Ürünü Conducted testlerini 1510 ve 3005 için geçti.
1510 | 3005 | DEIF 1510 |  | ENKO 1510
150W Ürünü Radiated testlerini 1510 için geçemedi.
T1 1510 modifiyesiz | T2 1510 çıkış bobini bağlandı | T3 Primer gate diyotu söküldü | T4 diyot takıldı, primer snubber cap ^220p, pri-sec kenardaki kapasite 4n7 |  | DEIF 1510
