alper-bozcal/75W_XDPS/Tests/Harmonik/Harmonik 31 Ekim 90W/SAVE04/WFM.CSV

in s | C2 in A
-2.9999923E-02 | -1.02539E-01
-2.9999462E-02 | -1.12305E-01
-2.9999002E-02 | -1.61133E-01
-2.9998541E-02 | -1.41602E-01
-2.9998080E-02 | -1.12305E-01
-2.9997619E-02 | -1.22070E-01
-2.9997158E-02 | -1.12305E-01
-2.9996698E-02 | -1.22070E-01
-2.9996237E-02 | -1.22070E-01
-2.9995776E-02 | -1.02539E-01
-2.9995315E-02 | -1.02539E-01
-2.9994854E-02 | -1.22070E-01
-2.9994394E-02 | -1.12305E-01
-2.9993933E-02 | -8.30078E-02
-2.9993472E-02 | -9.27734E-02
-2.9993011E-02 | -8.30078E-02
-2.9992550E-02 | -1.22070E-01
-2.9992090E-02 | -1.12305E-01
-2.9991629E-02 | -8.30078E-02
-2.9991168E-02 | -1.22070E-01
-2.9990707E-02 | -1.12305E-01
-2.9990246E-02 | -1.22070E-01
-2.9989786E-02 | -7.32422E-02
-2.9989325E-02 | -1.12305E-01
-2.9988864E-02 | -1.12305E-01
-2.9988403E-02 | -1.02539E-01
-2.9987942E-02 | -5.37109E-02
-2.9987482E-02 | -1.12305E-01
-2.9987021E-02 | -1.02539E-01
-2.9986560E-02 | -1.12305E-01
-2.9986099E-02 | -8.30078E-02
-2.9985638E-02 | -6.34766E-02
-2.9985178E-02 | -1.02539E-01
-2.9984717E-02 | -7.32422E-02
-2.9984256E-02 | -8.30078E-02
-2.9983795E-02 | -8.30078E-02
-2.9983334E-02 | -1.12305E-01
-2.9982874E-02 | -9.27734E-02
-2.9982413E-02 | -1.12305E-01
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
