alper-bozcal/75W_XDPS/Tests/Harmonik/Harmonik 31 Ekim 90W/SAVE06/WFM.CSV

in s | C2 in A
-4.0931164E+00 | 1.67480E+00
-4.0930540E+00 | 1.45020E+00
-4.0929915E+00 | 1.32324E+00
-4.0929290E+00 | 1.18652E+00
-4.0928666E+00 | 1.01074E+00
-4.0928041E+00 | 8.05664E-01
-4.0927417E+00 | 6.68945E-01
-4.0926792E+00 | 5.32227E-01
-4.0926168E+00 | 4.44336E-01
-4.0925543E+00 | 2.58789E-01
-4.0924919E+00 | 1.61133E-01
-4.0924294E+00 | 7.32422E-02
-4.0923669E+00 | 1.46484E-02
-4.0923045E+00 | 4.88281E-03
-4.0922420E+00 | 2.44141E-02
-4.0921796E+00 | 2.44141E-02
-4.0921171E+00 | 3.41797E-02
-4.0920547E+00 | 4.88281E-03
-4.0919922E+00 | 6.34766E-02
-4.0919298E+00 | 3.41797E-02
-4.0918673E+00 | 1.46484E-02
-4.0918048E+00 | 4.88281E-03
-4.0917424E+00 | -1.46484E-02
-4.0916799E+00 | -3.41797E-02
-4.0916175E+00 | 4.88281E-03
-4.0915550E+00 | -4.88281E-03
-4.0914926E+00 | -3.41797E-02
-4.0914301E+00 | -4.88281E-03
-4.0913676E+00 | 4.88281E-03
-4.0913052E+00 | -4.39453E-02
-4.0912427E+00 | -5.37109E-02
-4.0911803E+00 | -3.41797E-02
-4.0911178E+00 | 5.37109E-02
-4.0910554E+00 | -4.39453E-02
-4.0909929E+00 | -1.46484E-02
-4.0909305E+00 | -6.34766E-02
-4.0908680E+00 | -5.37109E-02
-4.0908055E+00 | -5.37109E-02
-4.0907431E+00 | -9.27734E-02
-4.0906806E+00 | -5.37109E-02
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
