alper-bozcal/75W_XDPS/Tests/Harmonik/Harmonik 31 Ekim 90W/SAVE07/WFM.CSV

in s | C2 in A
-4.0952136E+00 | 9.27734E-02
-4.0951511E+00 | 1.12305E-01
-4.0950886E+00 | 7.32422E-02
-4.0950261E+00 | 8.30078E-02
-4.0949636E+00 | 9.27734E-02
-4.0949011E+00 | 1.02539E-01
-4.0948386E+00 | 6.34766E-02
-4.0947762E+00 | 7.32422E-02
-4.0947137E+00 | 1.12305E-01
-4.0946512E+00 | 8.30078E-02
-4.0945887E+00 | 8.30078E-02
-4.0945262E+00 | 1.12305E-01
-4.0944637E+00 | 1.70898E-01
-4.0944012E+00 | 1.12305E-01
-4.0943387E+00 | 1.12305E-01
-4.0942762E+00 | 1.41602E-01
-4.0942138E+00 | 1.41602E-01
-4.0941513E+00 | 1.70898E-01
-4.0940888E+00 | 1.41602E-01
-4.0940263E+00 | 1.12305E-01
-4.0939638E+00 | 1.61133E-01
-4.0939013E+00 | 1.41602E-01
-4.0938388E+00 | 1.70898E-01
-4.0937763E+00 | 1.31836E-01
-4.0937139E+00 | 1.51367E-01
-4.0936514E+00 | 1.80664E-01
-4.0935889E+00 | 1.41602E-01
-4.0935264E+00 | 1.41602E-01
-4.0934639E+00 | 1.80664E-01
-4.0934014E+00 | 1.51367E-01
-4.0933389E+00 | 1.51367E-01
-4.0932764E+00 | 1.90430E-01
-4.0932140E+00 | 1.61133E-01
-4.0931515E+00 | 1.51367E-01
-4.0930890E+00 | 1.61133E-01
-4.0930265E+00 | 1.80664E-01
-4.0929640E+00 | 2.00195E-01
-4.0929015E+00 | 2.00195E-01
-4.0928390E+00 | 1.80664E-01
-4.0927765E+00 | 1.61133E-01
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
