alper-bozcal/75W_XDPS/Tests/Harmonik/Harmonik 31 Ekim 90W/SAVE08/WFM.CSV

in s | C2 in A
-4.0931164E+00 | 1.26953E-02
-4.0930540E+00 | 8.78906E-03
-4.0929915E+00 | 1.85547E-02
-4.0929290E+00 | 1.46484E-02
-4.0928666E+00 | -1.26953E-02
-4.0928041E+00 | 4.88281E-03
-4.0927417E+00 | 2.92969E-03
-4.0926792E+00 | 1.07422E-02
-4.0926168E+00 | -2.44141E-02
-4.0925543E+00 | -4.98047E-02
-4.0924919E+00 | -6.83594E-03
-4.0924294E+00 | -1.85547E-02
-4.0923669E+00 | -2.83203E-02
-4.0923045E+00 | -2.05078E-02
-4.0922420E+00 | -2.83203E-02
-4.0921796E+00 | -2.92969E-03
-4.0921171E+00 | -1.66016E-02
-4.0920547E+00 | -4.78516E-02
-4.0919922E+00 | -2.63672E-02
-4.0919298E+00 | -2.83203E-02
-4.0918673E+00 | -3.41797E-02
-4.0918048E+00 | -4.00391E-02
-4.0917424E+00 | -6.15234E-02
-4.0916799E+00 | -4.78516E-02
-4.0916175E+00 | -4.00391E-02
-4.0915550E+00 | -4.78516E-02
-4.0914926E+00 | -3.80859E-02
-4.0914301E+00 | -3.22266E-02
-4.0913676E+00 | -2.83203E-02
-4.0913052E+00 | -3.02734E-02
-4.0912427E+00 | -6.34766E-02
-4.0911803E+00 | -5.17578E-02
-4.0911178E+00 | -5.17578E-02
-4.0910554E+00 | -5.17578E-02
-4.0909929E+00 | -5.37109E-02
-4.0909305E+00 | -7.71484E-02
-4.0908680E+00 | -7.71484E-02
-4.0908055E+00 | -5.37109E-02
-4.0907431E+00 | -6.54297E-02
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
