alper-bozcal/75W_XDPS/Tests/Harmonik/Harmonik 10 Ekim/101.CSV

in Hz | Spectrum in A
0.000000E+00 | 3.2673591E-02
9.734475E-01 | 4.6182865E-02
1.946895E+00 | 4.5711611E-02
2.920342E+00 | 4.5083273E-02
3.893790E+00 | 4.4140765E-02
4.867237E+00 | 4.2884088E-02
5.840685E+00 | 4.1470327E-02
6.814132E+00 | 3.9899482E-02
7.787580E+00 | 3.8014467E-02
8.761027E+00 | 3.5972367E-02
9.734475E+00 | 3.3616099E-02
1.070792E+01 | 3.1259830E-02
1.168137E+01 | 2.8746477E-02
1.265482E+01 | 2.6076039E-02
1.362826E+01 | 2.3562686E-02
1.460171E+01 | 2.0892248E-02
1.557516E+01 | 1.8378895E-02
1.654861E+01 | 1.5865542E-02
1.752205E+01 | 1.3666358E-02
1.849550E+01 | 1.1624258E-02
1.946895E+01 | 1.0053413E-02
2.044240E+01 | 9.1109052E-03
2.141584E+01 | 9.2679898E-03
2.238929E+01 | 1.0524666E-02
2.336274E+01 | 1.2723850E-02
2.433619E+01 | 1.6022626E-02
2.530963E+01 | 2.0106825E-02
2.628308E+01 | 2.4976447E-02
2.725653E+01 | 3.0631492E-02
2.822998E+01 | 3.7229044E-02
2.920342E+01 | 4.4612019E-02
3.017687E+01 | 5.2780417E-02
3.115032E+01 | 6.1734237E-02
3.212377E+01 | 7.1473481E-02
3.309721E+01 | 8.1841063E-02
3.407066E+01 | 9.2836983E-02
3.504411E+01 | 1.0430416E-01
3.601756E+01 | 1.1592842E-01
3.699100E+01 | 1.2802393E-01
3.796445E+01 | 1.3996235E-01
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
