alper-bozcal/75W_XDPS/Tests/Harmonik/Harmonik 10 Ekim/102.CSV

in Hz | Spectrum in A
0.000000E+00 | 2.9688984E-02
9.735096E-01 | 4.1784496E-02
1.947019E+00 | 4.1470327E-02
2.920529E+00 | 4.0684904E-02
3.894038E+00 | 3.9742397E-02
4.867548E+00 | 3.8642805E-02
5.841057E+00 | 3.7229044E-02
6.814567E+00 | 3.5658198E-02
7.788077E+00 | 3.3930268E-02
8.761586E+00 | 3.2045253E-02
9.735096E+00 | 3.0003153E-02
1.070861E+01 | 2.7961054E-02
1.168211E+01 | 2.5918955E-02
1.265562E+01 | 2.3876855E-02
1.362913E+01 | 2.1834756E-02
1.460264E+01 | 1.9792656E-02
1.557615E+01 | 1.7907641E-02
1.654966E+01 | 1.5708457E-02
1.752317E+01 | 1.3666358E-02
1.849668E+01 | 1.1310089E-02
1.947019E+01 | 8.9538207E-03
2.044370E+01 | 6.2833829E-03
2.141721E+01 | 3.6129452E-03
2.239072E+01 | 3.4558606E-03
2.336423E+01 | 6.9117212E-03
2.433774E+01 | 1.1781343E-02
2.531125E+01 | 1.7593472E-02
2.628476E+01 | 2.4191024E-02
2.725827E+01 | 3.1731084E-02
2.823178E+01 | 4.0056566E-02
2.920529E+01 | 4.9481641E-02
3.017880E+01 | 5.9535053E-02
3.115231E+01 | 7.0530973E-02
3.212582E+01 | 8.2155232E-02
3.309933E+01 | 9.4564913E-02
3.407284E+01 | 1.0744585E-01
3.504634E+01 | 1.2079804E-01
3.601985E+01 | 1.3446439E-01
3.699336E+01 | 1.4828784E-01
3.796687E+01 | 1.6226836E-01
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
