alper-bozcal/75W_XDPS/Tests/Harmonik/Harmonik 10 Ekim/104.CSV

in Hz | Spectrum in A
0.000000E+00 | 4.0213651E-02
9.735096E-01 | 5.6707531E-02
1.947019E+00 | 5.6079193E-02
2.920529E+00 | 5.5293770E-02
3.894038E+00 | 5.4037093E-02
4.867548E+00 | 5.2623332E-02
5.841057E+00 | 5.0738317E-02
6.814567E+00 | 4.8696218E-02
7.788077E+00 | 4.6339949E-02
8.761586E+00 | 4.3669511E-02
9.735096E+00 | 4.0999074E-02
1.070861E+01 | 3.8171551E-02
1.168211E+01 | 3.5186944E-02
1.265562E+01 | 3.2045253E-02
1.362913E+01 | 2.9060646E-02
1.460264E+01 | 2.6076039E-02
1.557615E+01 | 2.3091432E-02
1.654966E+01 | 2.0263910E-02
1.752317E+01 | 1.7593472E-02
1.849668E+01 | 1.4923034E-02
1.947019E+01 | 1.2566766E-02
2.044370E+01 | 1.0367582E-02
2.141721E+01 | 8.3254824E-03
2.239072E+01 | 6.4404675E-03
2.336423E+01 | 4.8696218E-03
2.433774E+01 | 3.6129452E-03
2.531125E+01 | 2.6704377E-03
2.628476E+01 | 2.0420995E-03
2.725827E+01 | 1.5708457E-03
2.823178E+01 | 1.0995920E-03
2.920529E+01 | 9.4250744E-04
3.017880E+01 | 2.1991840E-03
3.115231E+01 | 4.5554526E-03
3.212582E+01 | 8.0113132E-03
3.309933E+01 | 1.2566766E-02
3.407284E+01 | 1.8221810E-02
3.504634E+01 | 2.5290616E-02
3.601985E+01 | 3.3616099E-02
3.699336E+01 | 4.3512427E-02
3.796687E+01 | 5.4979601E-02
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
