alper-bozcal/75W_XDPS/Tests/Harmonik/Harmonik 10 Ekim/105.CSV

in Hz | Spectrum in A
0.000000E+00 | 4.4612019E-02
9.735096E-01 | 6.2990914E-02
1.947019E+00 | 6.2519660E-02
2.920529E+00 | 6.1734237E-02
3.894038E+00 | 6.0634645E-02
4.867548E+00 | 5.9220884E-02
5.841057E+00 | 5.7492954E-02
6.814567E+00 | 5.5450854E-02
7.788077E+00 | 5.3094586E-02
8.761586E+00 | 5.0424148E-02
9.735096E+00 | 4.7596626E-02
1.070861E+01 | 4.4612019E-02
1.168211E+01 | 4.1470327E-02
1.265562E+01 | 3.8171551E-02
1.362913E+01 | 3.4872775E-02
1.460264E+01 | 3.1573999E-02
1.557615E+01 | 2.8275223E-02
1.654966E+01 | 2.5133532E-02
1.752317E+01 | 2.2306009E-02
1.849668E+01 | 1.9949741E-02
1.947019E+01 | 1.7907641E-02
2.044370E+01 | 1.6493880E-02
2.141721E+01 | 1.5865542E-02
2.239072E+01 | 1.6022626E-02
2.336423E+01 | 1.7279303E-02
2.433774E+01 | 1.9792656E-02
2.531125E+01 | 2.3248517E-02
2.628476E+01 | 2.7961054E-02
2.725827E+01 | 3.3773183E-02
2.823178E+01 | 4.0684904E-02
2.920529E+01 | 4.8853302E-02
3.017880E+01 | 5.8121292E-02
3.115231E+01 | 6.8331789E-02
3.212582E+01 | 7.9641879E-02
3.309933E+01 | 9.1894475E-02
3.407284E+01 | 1.0493249E-01
3.504634E+01 | 1.1875594E-01
3.601985E+01 | 1.3305063E-01
3.699336E+01 | 1.4765950E-01
3.796687E+01 | 1.6242545E-01
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
