alper-bozcal/75W_XDPS/Tests/EMC/2023 01 17 VESTEL/IMG_20230117_215528.jpg

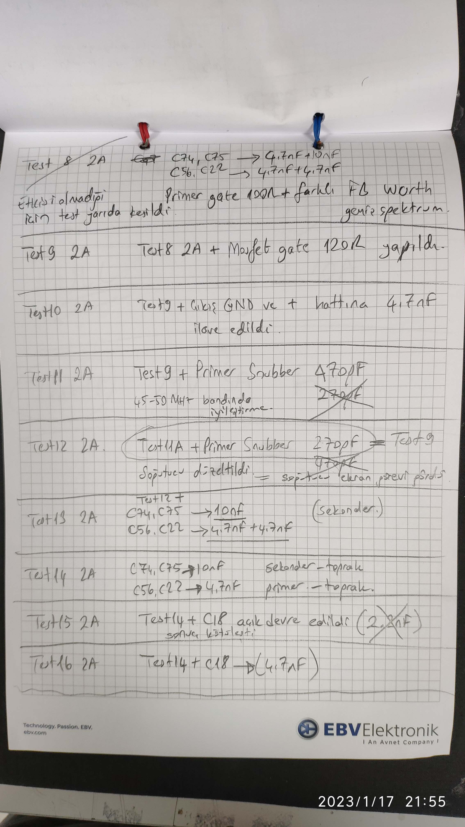
Tests/EMC/2023 01 17 VESTEL/IMG_20230117_215528.jpg
