alper-bozcal/75W_XDPS/Tests/EMC/2023 02 17 IZTECHLAB/fin_timebandwidth.png

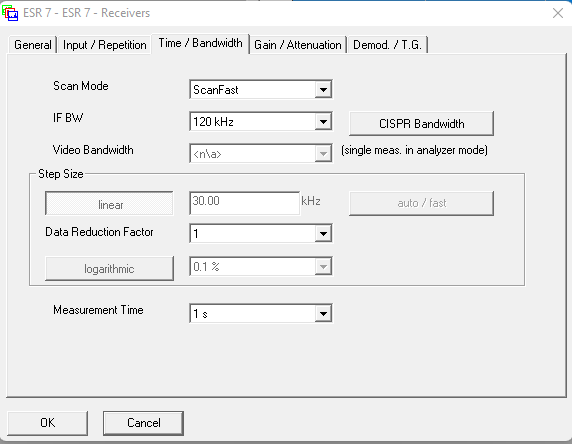
Tests/EMC/2023 02 17 IZTECHLAB/fin_timebandwidth.png
