alper-bozcal/75W_XDPS/Tests/EMC/2023 02 17 IZTECHLAB/pre-scan_gainatt.png

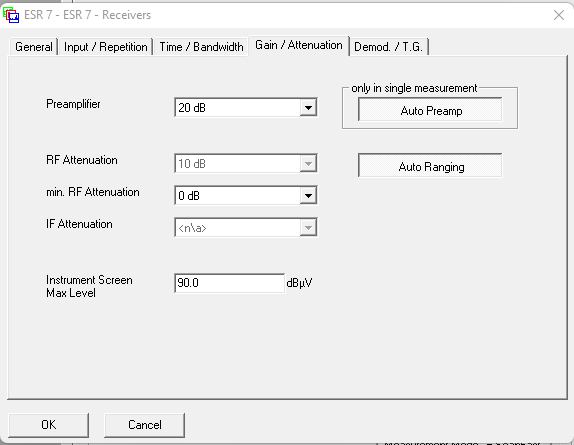
Tests/EMC/2023 02 17 IZTECHLAB/pre-scan_gainatt.png
