alper-bozcal/75W_XDPS/Tests/EMC/2023 05 23 Vestel RE CE Harmonics/Test Setups/D6825566-D2D9-45A1-B885-10263A36D330.jpg

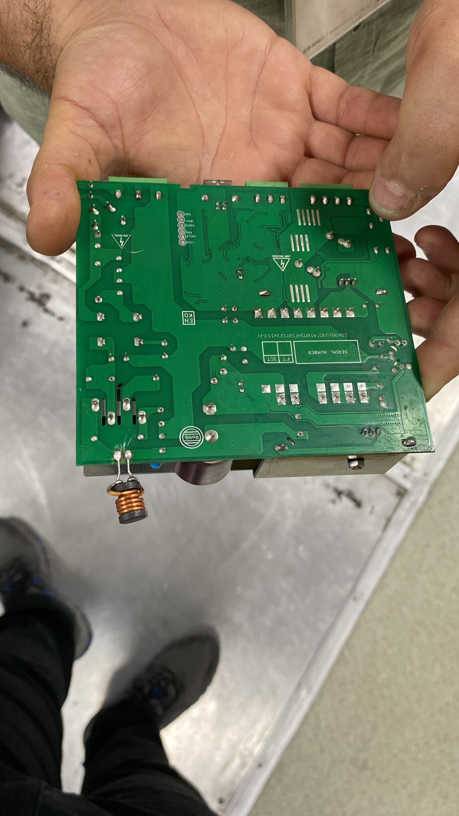
Tests/EMC/2023 05 23 Vestel RE CE Harmonics/Test Setups/D6825566-D2D9-45A1-B885-10263A36D330.jpg
