alper-bozcal/75W_XDPS/Tests/EMC/2023 05 23 Vestel RE CE Harmonics/Test Setups/IMG_3450.JPEG

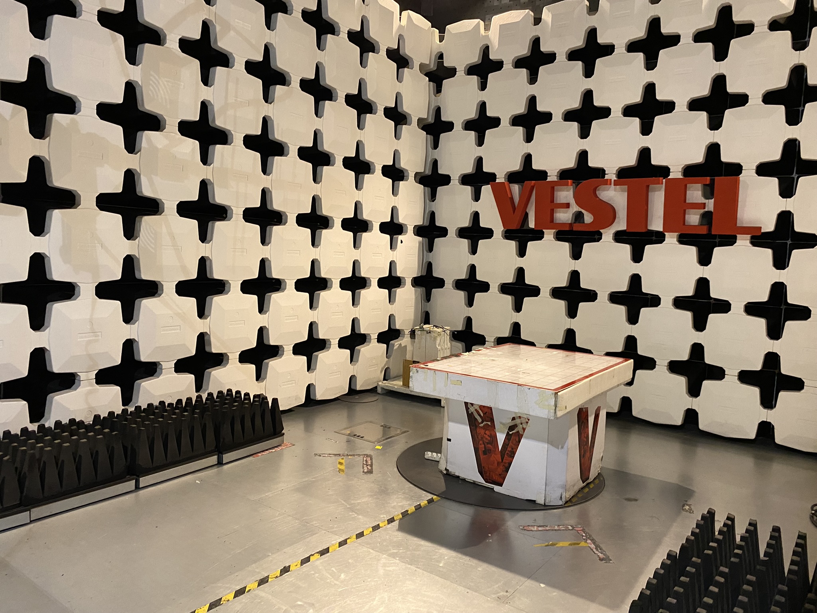
Tests/EMC/2023 05 23 Vestel RE CE Harmonics/Test Setups/IMG_3450.JPEG
