alper-bozcal/75W_XDPS/Tests/Harmonik/Harmonik 31 Ekim 90W/SAVE05/SCR.PNG

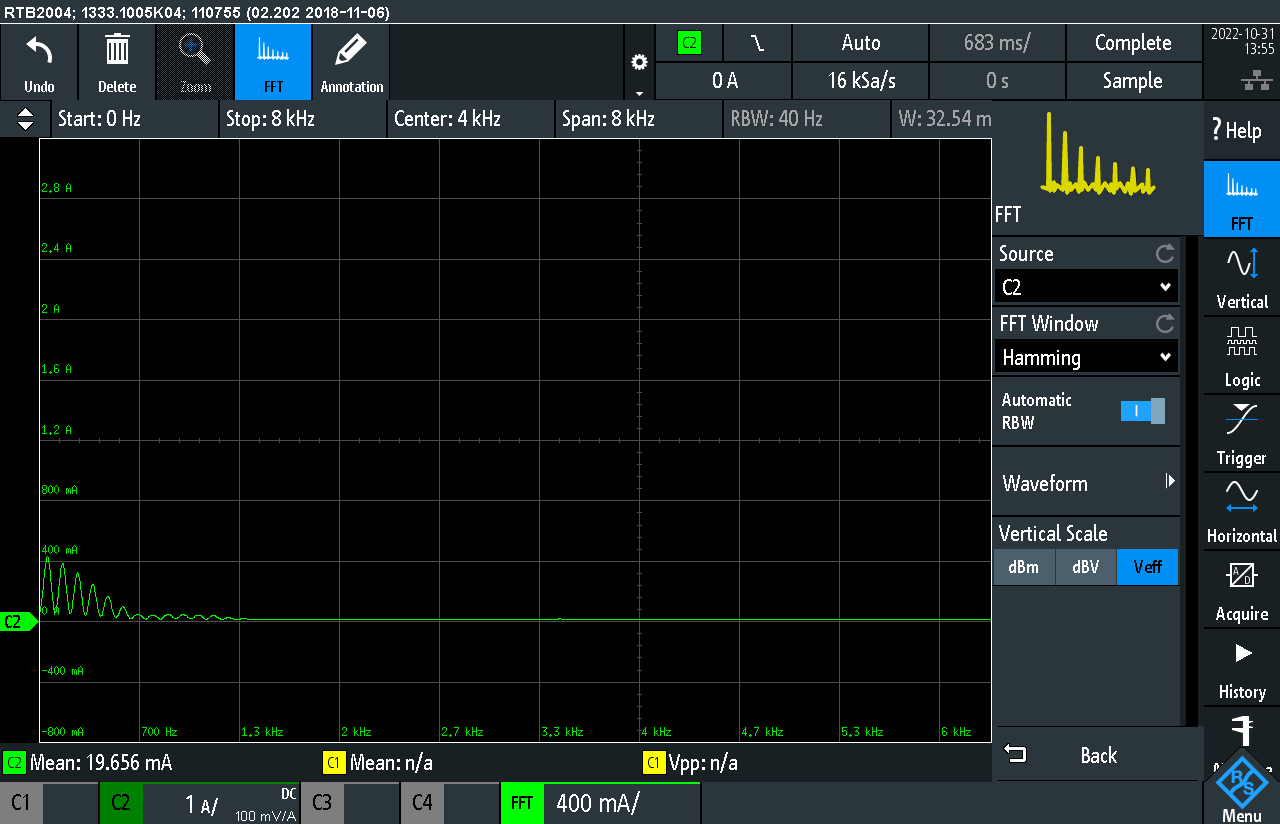
Tests/Harmonik/Harmonik 31 Ekim 90W/SAVE05/SCR.PNG
