alper-bozcal/75W_XDPS/Simulations/ADC_IOUT/I_OUT_ADC.asc

C1: cap; 100nF
C2: cap; 150pF
R1: res; 1K
R2: res; 6.8K
R3: res; 1K
R4: res; 4.7K
R5: res; 1K
R6: res; 1K
Rload: res; 15
RShunt: res; 0.003
U1: LM358
U2: LM358
V1: voltage; 15
V2: voltage; 3.3V
Named nets: 3V3, 0, I_OUT_ADC
.tran 0 10m 0s 1u
