alper-bozcal/75W_XDPS/Simulations/ADC_PT100/Pt100_rev2.asc

R1: res; 4.7K
R2: res; 1K
R3: res; 47K
R4: res; 22R
R5: res; 30K
R7: res; 120K
R9: res; 4.7K
R10: res; 1K
R11: res; 1.8K
Rpt100: res; {Rpt100}
U1: ZHT431
U2: TS921
U3: LM358
V1: voltage; 5V
V2: voltage; 5V
V3: voltage; 5V
Named nets: 0, V1, V2
.step param Rpt100 80 240 10
.op
;.step param run 1 10 1
V1:  5V -> 4V
R5: 24K ->30K
