alper-bozcal/75W_XDPS/Simulations/Boost Inp/Boost_Input.asc

C1: cap; 10nF
D1: diode; 1N4148
D2: zener; MMBZ6V8ALY
R1: res; 10K
R2: res; 1800R
R3: res; 180K
V1: voltage; ""
V2: voltage; 30V
Named nets: 0, Boost_IN
.dc V1 6 -6 1
