alper-bozcal/75W_XDPS/Simulations/Leakage/Leakeage-Model.asc

B1: bridgerectifier
C1: cap; 0
C2: cap; 0
C3: cap; 2.2µF
C4: cap; 4.7nF
C5: cap; 4.7nF
C7: cap; 4.7nF
C11: cap; 4.7nF
C12: cap; 150µF
C18: cap; 2.2nF
C35: cap; 0
C36: cap; 100nF
C37: cap; 100nF
C40: cap; 1000µF
C42: cap; 1000µF
C73: cap; 0
C74: cap; 0
C75: cap; 0
C82: cap; 0
C83: cap; 0
L1-1: ind; 7mH
L1-2: ind; 7mH
V1: voltage; SINE(0 311 50)
Named nets: EARTH, 0
L1(X1-1)
L2(X1-2)
(X1-3)
13.8V+(X3-1)
GNDIO(X3-2)
.tran 0 100m 0s 1u
