alper-bozcal/75W_XDPS/Simulations/Leakage/150W leakeage/150W-Leakeage-Model.asc

B1: bridgerectifier
C1: cap; 0
C2: cap; 0
C3: cap; 2.2µF
C4: cap; 4700pF
C5: cap; 4700pF
C7: cap; 4700pF
C11: cap; 4700pF
C12: cap; 150µF
C18: cap; 2.2nF
C22: cap; 2.2nF
C24: cap; 2.2nF
C25: cap; 4700pF
C27: cap; 4700pF
C33: cap; 100nF
C34: cap; 1µF
C35: cap; 4700pF
C36: cap; 100nF
C37: cap; 100nF
C40: cap; 1000µF
C42: cap; 1000µF
C59: cap; 4700pF
C72: cap; 10nF
C73: cap; 4700pF
C74: cap; 10nF
C75: cap; 10nF
C76: cap; 4700pF
C82: cap; 0
C83: cap; 220nF
L1-1: ind; 7mH
L1-2: ind; 7mH
V1: voltage; SINE(0 374V 50)
Named nets: EARTH, 0
L1(X1-1)
L2(X1-2)
(X1-3)
13.8V+(X3-1)
GNDIO(X3-2)
.tran 0 100m 0s 1u
SQRT(2)*85V = 120V
SQRT(2)*220V = 311V
SQRT(2)*265V = 374V
