alper-bozcal/75W_XDPS/Simulations/Leakage/300W leakeage/300W-Leakeage-Model.asc

B1: bridgerectifier
C1: cap; 2.2nF
C2: cap; 2.2nF
C3: cap; 330nF
C4: cap; 2.2nF
C5: cap; 2.2nF
C6: cap; 330nF
C8: cap; 680nF
C22: cap; 150nF
C31: cap; 1µF
C33: cap; 10nF
C38: cap; 0
C53: cap; 4700pF
C58: cap; 2.2nF
C59: cap; 100nF
C61: cap; 470µF
C62: cap; 470µF
C64: cap; 470µF
C65: cap; 470µF
C90: cap; 0
C108: cap; 10nF
C110: cap; 4700pF
C111: cap; 4700pF
C112: cap; 4700pF
C-A: cap; 0
L1-1: ind; 3.3mH
L1-2: ind; 3.3mH
L1: ind; 400µH
V1: voltage; SINE(0 373 50)
Named nets: EARTH, 0
L1(X1-1)
L2(X1-2)
(X1-3)
30V(X4-3)
GNDIO(X4-1)
.tran 0 100m 0s 1u
