alper-bozcal/75W_XDPS/Simulations/Leakage/90W leakeage/90W-Leakeage-Model.asc

B1: bridgerectifier
C1: cap; 0
C2: cap; 0
C3: cap; 1µF
C4: cap; 2n2nF
C5: cap; 2.2nF
C7: cap; 2.2nF
C11: cap; 2.2nF
C12: cap; 150µF
C18: cap; 2.2nF
C35: cap; 4700pF
C36: cap; 100nF
C37: cap; 100nF
C40: cap; 1000µF
C42: cap; 1000µF
C73: cap; 4700pF
C74: cap; 4700pF
C75: cap; 4700pF
C82: cap; 0
C83: cap; 220nF
C-A: cap; 2.2nF
L1-1: ind; 7mH
L1-2: ind; 7mH
V1: voltage; SINE(0 373 50)
Named nets: EARTH, 0
L1(X1-1)
L2(X1-2)
(X1-3)
13.8V+(X3-1)
GNDIO(X3-2)
.tran 0 100m 0s 1u
