alper-bozcal/75W_XDPS/Simulations/PWM_VOUT/VPWM/Draft1.asc

C60: cap; 10µF
R78: res; 12K
R79: res; 5K6
R80: res; 4K7
R81: res; 6K8
R82: res; 10K
R84: res; 1K
T4: npn; BC847B
U1: opamp
V1: voltage; 2.5V
V2: voltage; 0
V3: voltage; 13.8V
Named nets: 0
.dc v2 0 3.3 0.1
