alper-bozcal/75W_XDPS/Firmware/DBC2-Battery-Charger/Core/Src/tim.c

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
/* Includes ------------------------------------------------------------------*/
#include "tim.h"

TIM_HandleTypeDef htim3;
TIM_HandleTypeDef htim14;

/* TIM3 init function */
void MX_TIM3_Init(void)
{

  TIM_MasterConfigTypeDef sMasterConfig = {0};
  TIM_OC_InitTypeDef sConfigOC = {0};

  htim3.Instance = TIM3;
  htim3.Init.Prescaler = 0;
  htim3.Init.CounterMode = TIM_COUNTERMODE_UP;
  htim3.Init.Period = 959;
  htim3.Init.ClockDivision = TIM_CLOCKDIVISION_DIV1;
  htim3.Init.AutoReloadPreload = TIM_AUTORELOAD_PRELOAD_DISABLE;
  if (HAL_TIM_PWM_Init(&htim3) != HAL_OK)
  {
    Error_Handler();
  }
  sMasterConfig.MasterOutputTrigger = TIM_TRGO_RESET;
  sMasterConfig.MasterSlaveMode = TIM_MASTERSLAVEMODE_DISABLE;
  if (HAL_TIMEx_MasterConfigSynchronization(&htim3, &sMasterConfig) != HAL_OK)
  {
    Error_Handler();
  }
  sConfigOC.OCMode = TIM_OCMODE_PWM1;
  sConfigOC.Pulse = 0;
  sConfigOC.OCPolarity = TIM_OCPOLARITY_HIGH;
  sConfigOC.OCFastMode = TIM_OCFAST_DISABLE;
  if (HAL_TIM_PWM_ConfigChannel(&htim3, &sConfigOC, TIM_CHANNEL_3) != HAL_OK)
  {
    Error_Handler();
  }
  if (HAL_TIM_PWM_ConfigChannel(&htim3, &sConfigOC, TIM_CHANNEL_4) != HAL_OK)
  {
    Error_Handler();
  }
  HAL_TIM_MspPostInit(&htim3);

}
/* TIM14 init function */
void MX_TIM14_Init(void)
{

  htim14.Instance = TIM14;
  htim14.Init.Prescaler = 0;
  htim14.Init.CounterMode = TIM_COUNTERMODE_UP;
  htim14.Init.Period = 1000;
  htim14.Init.ClockDivision = TIM_CLOCKDIVISION_DIV1;
  htim14.Init.AutoReloadPreload = TIM_AUTORELOAD_PRELOAD_DISABLE;
  if (HAL_TIM_Base_Init(&htim14) != HAL_OK)
  {
    Error_Handler();
  }
}

void HAL_TIM_PWM_MspInit(TIM_HandleTypeDef* tim_pwmHandle)
{

  if(tim_pwmHandle->Instance==TIM3)
  {
    /* TIM3 clock enable */
    __HAL_RCC_TIM3_CLK_ENABLE();
  }
}

void HAL_TIM_Base_MspInit(TIM_HandleTypeDef* tim_baseHandle)
{

  if(tim_baseHandle->Instance==TIM14)
  {
    /* TIM14 clock enable */
    __HAL_RCC_TIM14_CLK_ENABLE();

    /* TIM14 interrupt Init */
    HAL_NVIC_SetPriority(TIM14_IRQn, 1, 0);
    HAL_NVIC_EnableIRQ(TIM14_IRQn);
  }
}
void HAL_TIM_MspPostInit(TIM_HandleTypeDef* timHandle)
{

  GPIO_InitTypeDef GPIO_InitStruct = {0};
  if(timHandle->Instance==TIM3)
  {
    __HAL_RCC_GPIOB_CLK_ENABLE();
    /**TIM3 GPIO Configuration
    PB0     ------> TIM3_CH3
    PB1     ------> TIM3_CH4
    */
    GPIO_InitStruct.Pin = I_PWM_Pin|V_PWM_Pin;
    GPIO_InitStruct.Mode = GPIO_MODE_AF_PP;
    GPIO_InitStruct.Pull = GPIO_NOPULL;
    GPIO_InitStruct.Speed = GPIO_SPEED_FREQ_LOW;
    GPIO_InitStruct.Alternate = GPIO_AF1_TIM3;
    HAL_GPIO_Init(GPIOB, &GPIO_InitStruct);

  }

}

void HAL_TIM_PWM_MspDeInit(TIM_HandleTypeDef* tim_pwmHandle)
{

  if(tim_pwmHandle->Instance==TIM3)
  {
    /* Peripheral clock disable */
    __HAL_RCC_TIM3_CLK_DISABLE();
  }
}

void HAL_TIM_Base_MspDeInit(TIM_HandleTypeDef* tim_baseHandle)
{

  if(tim_baseHandle->Instance==TIM14)
  {
    /* Peripheral clock disable */
    __HAL_RCC_TIM14_CLK_DISABLE();

    /* TIM14 interrupt Deinit */
    HAL_NVIC_DisableIRQ(TIM14_IRQn);
  }
}

/* USER CODE BEGIN 1 */

#endif //DBC_2_90W
#ifdef DBC_2_150W
/* Includes ------------------------------------------------------------------*/
#include "tim.h"

TIM_HandleTypeDef htim3;
TIM_HandleTypeDef htim14;

/* TIM3 init function */
void MX_TIM3_Init(void)
{

  TIM_MasterConfigTypeDef sMasterConfig = {0};
  TIM_OC_InitTypeDef sConfigOC = {0};

  htim3.Instance = TIM3;
  htim3.Init.Prescaler = 0;
  htim3.Init.CounterMode = TIM_COUNTERMODE_UP;
  htim3.Init.Period = 959;
  htim3.Init.ClockDivision = TIM_CLOCKDIVISION_DIV1;
  htim3.Init.AutoReloadPreload = TIM_AUTORELOAD_PRELOAD_DISABLE;
  if (HAL_TIM_PWM_Init(&htim3) != HAL_OK)
  {
    Error_Handler();
  }
  sMasterConfig.MasterOutputTrigger = TIM_TRGO_RESET;
  sMasterConfig.MasterSlaveMode = TIM_MASTERSLAVEMODE_DISABLE;
  if (HAL_TIMEx_MasterConfigSynchronization(&htim3, &sMasterConfig) != HAL_OK)
  {
    Error_Handler();
  }
  sConfigOC.OCMode = TIM_OCMODE_PWM1;
  sConfigOC.Pulse = 0;
  sConfigOC.OCPolarity = TIM_OCPOLARITY_HIGH;
  sConfigOC.OCFastMode = TIM_OCFAST_DISABLE;
  if (HAL_TIM_PWM_ConfigChannel(&htim3, &sConfigOC, TIM_CHANNEL_3) != HAL_OK)
  {
    Error_Handler();
  }
  if (HAL_TIM_PWM_ConfigChannel(&htim3, &sConfigOC, TIM_CHANNEL_4) != HAL_OK)
  {
    Error_Handler();
  }
  HAL_TIM_MspPostInit(&htim3);

}
/* TIM14 init function */
void MX_TIM14_Init(void)
{

  htim14.Instance = TIM14;
  htim14.Init.Prescaler = 0;
  htim14.Init.CounterMode = TIM_COUNTERMODE_UP;
  htim14.Init.Period = 1000;
  htim14.Init.ClockDivision = TIM_CLOCKDIVISION_DIV1;
  htim14.Init.AutoReloadPreload = TIM_AUTORELOAD_PRELOAD_DISABLE;
  if (HAL_TIM_Base_Init(&htim14) != HAL_OK)
  {
    Error_Handler();
  }
}

void HAL_TIM_PWM_MspInit(TIM_HandleTypeDef* tim_pwmHandle)
{

  if(tim_pwmHandle->Instance==TIM3)
  {
    /* TIM3 clock enable */
    __HAL_RCC_TIM3_CLK_ENABLE();
  }
}

void HAL_TIM_Base_MspInit(TIM_HandleTypeDef* tim_baseHandle)
{

  if(tim_baseHandle->Instance==TIM14)
  {
    /* TIM14 clock enable */
    __HAL_RCC_TIM14_CLK_ENABLE();

    /* TIM14 interrupt Init */
    HAL_NVIC_SetPriority(TIM14_IRQn, 1, 0);
    HAL_NVIC_EnableIRQ(TIM14_IRQn);
  }
}
void HAL_TIM_MspPostInit(TIM_HandleTypeDef* timHandle)
{

  GPIO_InitTypeDef GPIO_InitStruct = {0};
  if(timHandle->Instance==TIM3)
  {
    __HAL_RCC_GPIOB_CLK_ENABLE();
    /**TIM3 GPIO Configuration
    PB0     ------> TIM3_CH3
    PB1     ------> TIM3_CH4
    */
    GPIO_InitStruct.Pin = I_PWM_Pin|V_PWM_Pin;
    GPIO_InitStruct.Mode = GPIO_MODE_AF_PP;
    GPIO_InitStruct.Pull = GPIO_NOPULL;
    GPIO_InitStruct.Speed = GPIO_SPEED_FREQ_LOW;
    GPIO_InitStruct.Alternate = GPIO_AF1_TIM3;
    HAL_GPIO_Init(GPIOB, &GPIO_InitStruct);

  }

}

void HAL_TIM_PWM_MspDeInit(TIM_HandleTypeDef* tim_pwmHandle)
{

  if(tim_pwmHandle->Instance==TIM3)
  {
    /* Peripheral clock disable */
    __HAL_RCC_TIM3_CLK_DISABLE();
  }
}

void HAL_TIM_Base_MspDeInit(TIM_HandleTypeDef* tim_baseHandle)
{

  if(tim_baseHandle->Instance==TIM14)
  {
    /* Peripheral clock disable */
    __HAL_RCC_TIM14_CLK_DISABLE();

    /* TIM14 interrupt Deinit */
    HAL_NVIC_DisableIRQ(TIM14_IRQn);
  }
}
#endif //DBC_2_150W
#ifdef DBC_2_150W_2
/**
  ******************************************************************************
  * @file    tim.c
  * @brief   This file provides code for the configuration
  *          of the TIM instances.
  ******************************************************************************
  * @attention
  *
  * Copyright (c) 2022 STMicroelectronics.
  * All rights reserved.
  *
  * This software is licensed under terms that can be found in the LICENSE file
  * in the root directory of this software component.
  * If no LICENSE file comes with this software, it is provided AS-IS.
  *
  ******************************************************************************
  */
/* USER CODE END Header */
/* Includes ------------------------------------------------------------------*/
#include "tim.h"

TIM_HandleTypeDef htim1;
TIM_HandleTypeDef htim2;
TIM_HandleTypeDef htim3;
TIM_HandleTypeDef htim14;

/* TIM1 init function */
void MX_TIM1_Init(void)
{

  TIM_ClockConfigTypeDef sClockSourceConfig = {0};
  TIM_MasterConfigTypeDef sMasterConfig = {0};

  htim1.Instance = TIM1;
  htim1.Init.Prescaler = 0;
  htim1.Init.CounterMode = TIM_COUNTERMODE_UP;
  htim1.Init.Period = 0;
  htim1.Init.ClockDivision = TIM_CLOCKDIVISION_DIV1;
  htim1.Init.RepetitionCounter = 0;
  htim1.Init.AutoReloadPreload = TIM_AUTORELOAD_PRELOAD_DISABLE;
  if (HAL_TIM_Base_Init(&htim1) != HAL_OK)
  {
    Error_Handler();
  }
  sClockSourceConfig.ClockSource = TIM_CLOCKSOURCE_INTERNAL;
  if (HAL_TIM_ConfigClockSource(&htim1, &sClockSourceConfig) != HAL_OK)
  {
    Error_Handler();
  }
  sMasterConfig.MasterOutputTrigger = TIM_TRGO_RESET;
  sMasterConfig.MasterSlaveMode = TIM_MASTERSLAVEMODE_DISABLE;
  if (HAL_TIMEx_MasterConfigSynchronization(&htim1, &sMasterConfig) != HAL_OK)
  {
    Error_Handler();
  }
}
/* TIM2 init function */
void MX_TIM2_Init(void)
{

  TIM_ClockConfigTypeDef sClockSourceConfig = {0};
  TIM_MasterConfigTypeDef sMasterConfig = {0};

  htim2.Instance = TIM2;
  htim2.Init.Prescaler = 0;
  htim2.Init.CounterMode = TIM_COUNTERMODE_UP;
  htim2.Init.Period = 0;
  htim2.Init.ClockDivision = TIM_CLOCKDIVISION_DIV1;
  htim2.Init.AutoReloadPreload = TIM_AUTORELOAD_PRELOAD_DISABLE;
  if (HAL_TIM_Base_Init(&htim2) != HAL_OK)
  {
    Error_Handler();
  }
  sClockSourceConfig.ClockSource = TIM_CLOCKSOURCE_INTERNAL;
  if (HAL_TIM_ConfigClockSource(&htim2, &sClockSourceConfig) != HAL_OK)
  {
    Error_Handler();
  }
  sMasterConfig.MasterOutputTrigger = TIM_TRGO_RESET;
  sMasterConfig.MasterSlaveMode = TIM_MASTERSLAVEMODE_DISABLE;
  if (HAL_TIMEx_MasterConfigSynchronization(&htim2, &sMasterConfig) != HAL_OK)
  {
    Error_Handler();
  }
}
/* TIM3 init function */
void MX_TIM3_Init(void)
{

  TIM_MasterConfigTypeDef sMasterConfig = {0};
  TIM_OC_InitTypeDef sConfigOC = {0};

  htim3.Instance = TIM3;
  htim3.Init.Prescaler = 1-1;
  htim3.Init.CounterMode = TIM_COUNTERMODE_UP;
  htim3.Init.Period = 1-1;
  htim3.Init.ClockDivision = TIM_CLOCKDIVISION_DIV1;
  htim3.Init.AutoReloadPreload = TIM_AUTORELOAD_PRELOAD_DISABLE;
  if (HAL_TIM_PWM_Init(&htim3) != HAL_OK)
  {
    Error_Handler();
  }
  sMasterConfig.MasterOutputTrigger = TIM_TRGO_RESET;
  sMasterConfig.MasterSlaveMode = TIM_MASTERSLAVEMODE_DISABLE;
  if (HAL_TIMEx_MasterConfigSynchronization(&htim3, &sMasterConfig) != HAL_OK)
  {
    Error_Handler();
  }
  sConfigOC.OCMode = TIM_OCMODE_PWM1;
  sConfigOC.Pulse = 0;
  sConfigOC.OCPolarity = TIM_OCPOLARITY_HIGH;
  sConfigOC.OCFastMode = TIM_OCFAST_DISABLE;
  if (HAL_TIM_PWM_ConfigChannel(&htim3, &sConfigOC, TIM_CHANNEL_3) != HAL_OK)
  {
    Error_Handler();
  }
  if (HAL_TIM_PWM_ConfigChannel(&htim3, &sConfigOC, TIM_CHANNEL_4) != HAL_OK)
  {
    Error_Handler();
  }
  HAL_TIM_MspPostInit(&htim3);

}
/* TIM14 init function */
void MX_TIM14_Init(void)
{

  htim14.Instance = TIM14;
  htim14.Init.Prescaler = 0;
  htim14.Init.CounterMode = TIM_COUNTERMODE_UP;
  htim14.Init.Period = 1000;
  htim14.Init.ClockDivision = TIM_CLOCKDIVISION_DIV1;
  htim14.Init.AutoReloadPreload = TIM_AUTORELOAD_PRELOAD_DISABLE;
  if (HAL_TIM_Base_Init(&htim14) != HAL_OK)
  {
    Error_Handler();
  }
}

void HAL_TIM_Base_MspInit(TIM_HandleTypeDef* tim_baseHandle)
{

  if(tim_baseHandle->Instance==TIM1)
  {
    /* TIM1 clock enable */
    __HAL_RCC_TIM1_CLK_ENABLE();
  }
  else if(tim_baseHandle->Instance==TIM2)
  {
    /* TIM2 clock enable */
    __HAL_RCC_TIM2_CLK_ENABLE();
  }
  else if(tim_baseHandle->Instance==TIM14)
  {
    /* TIM14 clock enable */
    __HAL_RCC_TIM14_CLK_ENABLE();

    /* TIM14 interrupt Init */
    HAL_NVIC_SetPriority(TIM14_IRQn, 1, 0);
    HAL_NVIC_EnableIRQ(TIM14_IRQn);
  }
}

void HAL_TIM_PWM_MspInit(TIM_HandleTypeDef* tim_pwmHandle)
{

  if(tim_pwmHandle->Instance==TIM3)
  {
    /* TIM3 clock enable */
    __HAL_RCC_TIM3_CLK_ENABLE();
  }
}
void HAL_TIM_MspPostInit(TIM_HandleTypeDef* timHandle)
{

  GPIO_InitTypeDef GPIO_InitStruct = {0};
  if(timHandle->Instance==TIM3)
  {
    __HAL_RCC_GPIOB_CLK_ENABLE();
    /**TIM3 GPIO Configuration
    PB0     ------> TIM3_CH3
    PB1     ------> TIM3_CH4
    */
    GPIO_InitStruct.Pin = V_PWM_Pin|I_PWM_Pin;
    GPIO_InitStruct.Mode = GPIO_MODE_AF_PP;
    GPIO_InitStruct.Pull = GPIO_NOPULL;
    GPIO_InitStruct.Speed = GPIO_SPEED_FREQ_LOW;
    GPIO_InitStruct.Alternate = GPIO_AF1_TIM3;
    HAL_GPIO_Init(GPIOB, &GPIO_InitStruct);

  }

}

void HAL_TIM_Base_MspDeInit(TIM_HandleTypeDef* tim_baseHandle)
{

  if(tim_baseHandle->Instance==TIM1)
  {
    /* Peripheral clock disable */
    __HAL_RCC_TIM1_CLK_DISABLE();
  }
  else if(tim_baseHandle->Instance==TIM2)
  {
    /* Peripheral clock disable */
    __HAL_RCC_TIM2_CLK_DISABLE();
  }
  else if(tim_baseHandle->Instance==TIM14)
  {
    /* Peripheral clock disable */
    __HAL_RCC_TIM14_CLK_DISABLE();

    /* TIM14 interrupt Deinit */
    HAL_NVIC_DisableIRQ(TIM14_IRQn);
  }
}

void HAL_TIM_PWM_MspDeInit(TIM_HandleTypeDef* tim_pwmHandle)
{

  if(tim_pwmHandle->Instance==TIM3)
  {
    /* Peripheral clock disable */
    __HAL_RCC_TIM3_CLK_DISABLE();
  }
}

/* USER CODE BEGIN 1 */

#endif //DBC_2_150W_2
#ifdef DBC_2_300W
/* Includes ------------------------------------------------------------------*/
#include "tim.h"

TIM_HandleTypeDef htim1;
TIM_HandleTypeDef htim2;
TIM_HandleTypeDef htim14;

/* TIM1 init function */
void MX_TIM1_Init(void)
{

  TIM_ClockConfigTypeDef sClockSourceConfig = {0};
  TIM_MasterConfigTypeDef sMasterConfig = {0};
  TIM_OC_InitTypeDef sConfigOC = {0};
  TIM_BreakDeadTimeConfigTypeDef sBreakDeadTimeConfig = {0};

  htim1.Instance = TIM1;
  htim1.Init.Prescaler = 0;
  htim1.Init.CounterMode = TIM_COUNTERMODE_UP;
  htim1.Init.Period = 0;
  htim1.Init.ClockDivision = TIM_CLOCKDIVISION_DIV1;
  htim1.Init.RepetitionCounter = 0;
  htim1.Init.AutoReloadPreload = TIM_AUTORELOAD_PRELOAD_DISABLE;
  if (HAL_TIM_Base_Init(&htim1) != HAL_OK)
  {
    Error_Handler();
  }
  sClockSourceConfig.ClockSource = TIM_CLOCKSOURCE_INTERNAL;
  if (HAL_TIM_ConfigClockSource(&htim1, &sClockSourceConfig) != HAL_OK)
  {
    Error_Handler();
  }
  if (HAL_TIM_PWM_Init(&htim1) != HAL_OK)
  {
    Error_Handler();
  }
  sMasterConfig.MasterOutputTrigger = TIM_TRGO_RESET;
  sMasterConfig.MasterSlaveMode = TIM_MASTERSLAVEMODE_DISABLE;
  if (HAL_TIMEx_MasterConfigSynchronization(&htim1, &sMasterConfig) != HAL_OK)
  {
    Error_Handler();
  }
  sConfigOC.OCMode = TIM_OCMODE_PWM1;
  sConfigOC.Pulse = 0;
  sConfigOC.OCPolarity = TIM_OCPOLARITY_HIGH;
  sConfigOC.OCNPolarity = TIM_OCNPOLARITY_HIGH;
  sConfigOC.OCFastMode = TIM_OCFAST_DISABLE;
  sConfigOC.OCIdleState = TIM_OCIDLESTATE_RESET;
  sConfigOC.OCNIdleState = TIM_OCNIDLESTATE_RESET;
  if (HAL_TIM_PWM_ConfigChannel(&htim1, &sConfigOC, TIM_CHANNEL_3) != HAL_OK)
  {
    Error_Handler();
  }
  sBreakDeadTimeConfig.OffStateRunMode = TIM_OSSR_DISABLE;
  sBreakDeadTimeConfig.OffStateIDLEMode = TIM_OSSI_DISABLE;
  sBreakDeadTimeConfig.LockLevel = TIM_LOCKLEVEL_OFF;
  sBreakDeadTimeConfig.DeadTime = 0;
  sBreakDeadTimeConfig.BreakState = TIM_BREAK_DISABLE;
  sBreakDeadTimeConfig.BreakPolarity = TIM_BREAKPOLARITY_HIGH;
  sBreakDeadTimeConfig.AutomaticOutput = TIM_AUTOMATICOUTPUT_DISABLE;
  if (HAL_TIMEx_ConfigBreakDeadTime(&htim1, &sBreakDeadTimeConfig) != HAL_OK)
  {
    Error_Handler();
  }
  HAL_TIM_MspPostInit(&htim1);

}
/* TIM2 init function */
void MX_TIM2_Init(void)
{

  TIM_ClockConfigTypeDef sClockSourceConfig = {0};
  TIM_MasterConfigTypeDef sMasterConfig = {0};
  TIM_OC_InitTypeDef sConfigOC = {0};

  htim2.Instance = TIM2;
  htim2.Init.Prescaler = 0;
  htim2.Init.CounterMode = TIM_COUNTERMODE_UP;
  htim2.Init.Period = 0;
  htim2.Init.ClockDivision = TIM_CLOCKDIVISION_DIV1;
  htim2.Init.AutoReloadPreload = TIM_AUTORELOAD_PRELOAD_DISABLE;
  if (HAL_TIM_Base_Init(&htim2) != HAL_OK)
  {
    Error_Handler();
  }
  sClockSourceConfig.ClockSource = TIM_CLOCKSOURCE_INTERNAL;
  if (HAL_TIM_ConfigClockSource(&htim2, &sClockSourceConfig) != HAL_OK)
  {
    Error_Handler();
  }
  if (HAL_TIM_PWM_Init(&htim2) != HAL_OK)
  {
    Error_Handler();
  }
  sMasterConfig.MasterOutputTrigger = TIM_TRGO_RESET;
  sMasterConfig.MasterSlaveMode = TIM_MASTERSLAVEMODE_DISABLE;
  if (HAL_TIMEx_MasterConfigSynchronization(&htim2, &sMasterConfig) != HAL_OK)
  {
    Error_Handler();
  }
  sConfigOC.OCMode = TIM_OCMODE_PWM1;
  sConfigOC.Pulse = 0;
  sConfigOC.OCPolarity = TIM_OCPOLARITY_HIGH;
  sConfigOC.OCFastMode = TIM_OCFAST_DISABLE;
  if (HAL_TIM_PWM_ConfigChannel(&htim2, &sConfigOC, TIM_CHANNEL_3) != HAL_OK)
  {
    Error_Handler();
  }
  if (HAL_TIM_PWM_ConfigChannel(&htim2, &sConfigOC, TIM_CHANNEL_4) != HAL_OK)
  {
    Error_Handler();
  }
  HAL_TIM_MspPostInit(&htim2);

}
/* TIM14 init function */
void MX_TIM14_Init(void)
{

  htim14.Instance = TIM14;
  htim14.Init.Prescaler = 0;
  htim14.Init.CounterMode = TIM_COUNTERMODE_UP;
  htim14.Init.Period = 1000;
  htim14.Init.ClockDivision = TIM_CLOCKDIVISION_DIV1;
  htim14.Init.AutoReloadPreload = TIM_AUTORELOAD_PRELOAD_DISABLE;
  if (HAL_TIM_Base_Init(&htim14) != HAL_OK)
  {
    Error_Handler();
  }
}

void HAL_TIM_Base_MspInit(TIM_HandleTypeDef* tim_baseHandle)
{

  if(tim_baseHandle->Instance==TIM1)
  {
    /* TIM1 clock enable */
    __HAL_RCC_TIM1_CLK_ENABLE();
  }
  else if(tim_baseHandle->Instance==TIM2)
  {
    /* TIM2 clock enable */
    __HAL_RCC_TIM2_CLK_ENABLE();
  }
  else if(tim_baseHandle->Instance==TIM14)
  {
    /* TIM14 clock enable */
    __HAL_RCC_TIM14_CLK_ENABLE();

    /* TIM14 interrupt Init */
    HAL_NVIC_SetPriority(TIM14_IRQn, 1, 0);
    HAL_NVIC_EnableIRQ(TIM14_IRQn);
  }
}
void HAL_TIM_MspPostInit(TIM_HandleTypeDef* timHandle)
{

  GPIO_InitTypeDef GPIO_InitStruct = {0};
  if(timHandle->Instance==TIM1)
  {
    __HAL_RCC_GPIOB_CLK_ENABLE();
    /**TIM1 GPIO Configuration
    PB15     ------> TIM1_CH3N
    */
    GPIO_InitStruct.Pin = PWM_CAN_Pin;
    GPIO_InitStruct.Mode = GPIO_MODE_AF_PP;
    GPIO_InitStruct.Pull = GPIO_NOPULL;
    GPIO_InitStruct.Speed = GPIO_SPEED_FREQ_LOW;
    GPIO_InitStruct.Alternate = GPIO_AF2_TIM1;
    HAL_GPIO_Init(PWM_CAN_GPIO_Port, &GPIO_InitStruct);

  }
  else if(timHandle->Instance==TIM2)
  {
    __HAL_RCC_GPIOA_CLK_ENABLE();
    __HAL_RCC_GPIOB_CLK_ENABLE();
    /**TIM2 GPIO Configuration
    PA3     ------> TIM2_CH4
    PB10     ------> TIM2_CH3
    */
    GPIO_InitStruct.Pin = GPIO_PIN_3;
    GPIO_InitStruct.Mode = GPIO_MODE_AF_PP;
    GPIO_InitStruct.Pull = GPIO_NOPULL;
    GPIO_InitStruct.Speed = GPIO_SPEED_FREQ_LOW;
    GPIO_InitStruct.Alternate = GPIO_AF2_TIM2;
    HAL_GPIO_Init(GPIOA, &GPIO_InitStruct);

    GPIO_InitStruct.Pin = I_PWM_Pin;
    GPIO_InitStruct.Mode = GPIO_MODE_AF_PP;
    GPIO_InitStruct.Pull = GPIO_NOPULL;
    GPIO_InitStruct.Speed = GPIO_SPEED_FREQ_LOW;
    GPIO_InitStruct.Alternate = GPIO_AF2_TIM2;
    HAL_GPIO_Init(I_PWM_GPIO_Port, &GPIO_InitStruct);

  }

}

void HAL_TIM_Base_MspDeInit(TIM_HandleTypeDef* tim_baseHandle)
{

  if(tim_baseHandle->Instance==TIM1)
  {
    /* Peripheral clock disable */
    __HAL_RCC_TIM1_CLK_DISABLE();
  }
  else if(tim_baseHandle->Instance==TIM2)
  {
    /* Peripheral clock disable */
    __HAL_RCC_TIM2_CLK_DISABLE();
  }
  else if(tim_baseHandle->Instance==TIM14)
  {
    /* Peripheral clock disable */
    __HAL_RCC_TIM14_CLK_DISABLE();

    /* TIM14 interrupt Deinit */
    HAL_NVIC_DisableIRQ(TIM14_IRQn);
  }
}
#endif //DBC_2_300W
/* USER CODE END 1 */
