alper-bozcal/75W_XDPS/Firmware/DBC2-Battery-Charger/Parameters/parameter_list.c

/*
 * parameter_list.c
 *
 *  Created on: 15 Nis 2016
 *      Author: NAZIM YILDIZ
 */
#include <parameter_definitions.h>
#include "parameters_setget.h"
#include "parameter_callback.h"
#include "main.h"

const ParameterList_t ParamList[PARAM_LAST_INDEX] = {
	//PNo							//Min			//Max			//Val		//Coef					//AccesLevel						//SaveToStorageActivation //CallBack
	{OUTPUT_VOLTAGE,				MIN_VOLTAGE,	MAX_VOLTAGE,	1380,		-2,			ACCESS_LEVEL1_READ | ACCESS_LEVEL1_WRITE,		SAVE_ENABLE,		callBackUpdateVoltageREF},
	{OUTPUT_CURRENT,				0,				MAX_CURRENT,	500,		-2,			ACCESS_LEVEL1_READ | ACCESS_LEVEL1_WRITE,		SAVE_ENABLE,		callBackUpdateCurrentREF},
	{OUTPUT_RELAY,					-1,				1,				0,			0,			ACCESS_LEVEL2_READ | ACCESS_LEVEL1_WRITE,		SAVE_ENABLE,		CallbackRelay},
	{VOUTPWM,						0,				959,			0,			0,			ACCESS_LEVEL1_READ | ACCESS_LEVEL1_WRITE,		SAVE_ENABLE,		CallbackUpdateVPWM},
	{IOUTPWM,						0,				959,			959,		0,			ACCESS_LEVEL1_READ | ACCESS_LEVEL1_WRITE,		SAVE_ENABLE,		CallbackUpdateIPWM},
	{OUTPUT_BOOST_VOLTAGE,			MIN_VOLTAGE,	MAX_VOLTAGE,	1450,		-2,			ACCESS_LEVEL2_READ | ACCESS_LEVEL1_WRITE,		SAVE_ENABLE,		CallbackUpdateVoltageBoost},
	{OUTPUT_BLANK_7,				-1,				1,				0,			0,			ACCESS_LEVEL1_READ | ACCESS_LEVEL1_WRITE,		SAVE_ENABLE,		CallbackNull},
	{OUTPUT_CONS_CURRENT,			0,				4000,			500,		-2,			ACCESS_LEVEL1_READ | ACCESS_LEVEL1_WRITE,		SAVE_ENABLE,		CallbackNull},
	{OUTPUT_CONS_VOLTAGE,			1200,			3000,			1380,		-2, 		ACCESS_LEVEL2_READ | ACCESS_LEVEL1_WRITE,		SAVE_ENABLE,		CallbackNull},
	{OUTPUT_FLOAT_VOLTAGE,			1200,			3000,			1380,		-2,			ACCESS_LEVEL1_READ | ACCESS_LEVEL1_WRITE,		SAVE_ENABLE,		CallbackNull},
	{OUTPUT_CONS_CURRENT_TIME,		0,				32000,			0,			0,			ACCESS_LEVEL1_READ | ACCESS_LEVEL1_WRITE,		SAVE_ENABLE,		CallbackNull},
	{OUTPUT_CONS_VOLTAGE_TIME,		0,				32000,			0,			0,			ACCESS_LEVEL1_READ | ACCESS_LEVEL1_WRITE,		SAVE_ENABLE,		CallbackNull},
	{OUTPUT_BOOST_TIME_MINUTES,		0,				32767,			10000,		0,			ACCESS_LEVEL1_READ | ACCESS_LEVEL1_WRITE,		SAVE_ENABLE,		CallbackNull},
	{OUTPUT_FLOAT_TIME,				0,				32000,			0,			0,			ACCESS_LEVEL1_READ | ACCESS_LEVEL1_WRITE,		SAVE_ENABLE,		CallbackNull},
	{OUTPUT_CHARGE_MODE,			0,				10,				0,			0,			ACCESS_LEVEL1_READ | ACCESS_LEVEL1_WRITE,		SAVE_DISABLE,		CallbackNull},
	{OUTPUT_AUTO_BOOST,				0,				1,				0,			0,			ACCESS_LEVEL1_READ | ACCESS_LEVEL1_WRITE,		SAVE_DISABLE,		CallbackNull},
	{OUTPUT_BLANK_17,				0,			32000,				0,			0,			ACCESS_LEVEL1_READ | ACCESS_LEVEL1_WRITE,		SAVE_DISABLE,		CallbackNull},
	{OUTPUT_BLANK_18,				-1,				1,				0,			0,			ACCESS_LEVEL1_READ | ACCESS_LEVEL1_WRITE,		SAVE_DISABLE,		CallbackTestMode},
	{OUTPUT_BLANK_19,				0,			32000,				0,			0,			ACCESS_LEVEL1_READ | ACCESS_LEVEL1_WRITE,		SAVE_DISABLE,		CallbackDebugParam},
	{DEVICE_RESET,					0,				1,				0,			0,			ACCESS_LEVEL1_READ | ACCESS_LEVEL1_WRITE,		SAVE_DISABLE,		CallbackDeviceReset},
	{OUTPUT_REVERSE_VOLTAGE,		100,			6000,			2000,		-2,			ACCESS_LEVEL1_READ | ACCESS_LEVEL1_WRITE,		SAVE_ENABLE,		CallbackReverse},
	{PWMFLAG,						0,				1,				0,			0,			ACCESS_LEVEL1_READ | ACCESS_LEVEL1_WRITE,		SAVE_DISABLE,		CallbackNull},
	{OUTPUT_BLANK_23,				0,				0,				0,			0,			ACCESS_LEVEL1_READ | ACCESS_LEVEL1_WRITE,		SAVE_ENABLE,		CallbackNull},
	{OUTPUT_BLANK_24,				0,				0,				0,			0,			ACCESS_LEVEL1_READ | ACCESS_LEVEL1_WRITE,		SAVE_ENABLE,		CallbackNull},
	{OUTPUT_BLANK_25,				0,				0,				0,			0,			ACCESS_LEVEL1_READ | ACCESS_LEVEL1_WRITE,		SAVE_ENABLE,		CallbackNull},
	{OUTPUT_BLANK_26,				0,				0,				0,			0,			ACCESS_LEVEL1_READ | ACCESS_LEVEL1_WRITE,		SAVE_ENABLE,		CallbackNull},
	{OUTPUT_MODE_AUTO,				0,				1,				0,			0,			ACCESS_LEVEL1_READ | ACCESS_LEVEL1_WRITE,		SAVE_ENABLE,		CallbackNull},
	{OUTPUT_MODE_PSU,				0,				1,				1,			0,			ACCESS_LEVEL1_READ | ACCESS_LEVEL1_WRITE,		SAVE_ENABLE,		CallbackNull},
	{OUTPUT_MODEL,					0,				32000,			0,			0,			ACCESS_LEVEL1_READ | ACCESS_LEVEL1_WRITE,		SAVE_DISABLE,		CallbackModel},
	{OUTPUT_CUT_OFF,				0,				1,				0,			0,			ACCESS_LEVEL1_READ | ACCESS_LEVEL1_WRITE,		SAVE_DISABLE,		CallbackCutoff},

	{MEASURE_CALIB_VOUT,			800,			1200,			1024,		-3,			ACCESS_LEVEL1_READ | ACCESS_LEVEL1_WRITE,		SAVE_ENABLE,		CallbackCalibration},
	{MEASURE_CALIB_IOUT,			800,			1200,			1024,		-3,			ACCESS_LEVEL1_READ | ACCESS_LEVEL1_WRITE,		SAVE_ENABLE,		CallbackCalibration},
	{MEASURE_CALIB_PT100,			800,			1200,			1024,		-3,			ACCESS_LEVEL1_READ | ACCESS_LEVEL1_WRITE,		SAVE_ENABLE,		CallbackCalibration},
	{MEASURE_CALIB_NTC,				800,			1200,			1024,		-3,			ACCESS_LEVEL1_READ | ACCESS_LEVEL1_WRITE,		SAVE_ENABLE,		CallbackCalibration},
	{MEASURE_CALIB_VBAT,			800,			1200,			1024,		-3,			ACCESS_LEVEL1_READ | ACCESS_LEVEL1_WRITE,		SAVE_ENABLE,		CallbackCalibration},
	{MEASURE_OFF_VOUT,				-1000,			1000,			0,			0,			ACCESS_LEVEL1_READ | ACCESS_LEVEL1_WRITE,		SAVE_ENABLE,		CallbackCalibration},
	{MEASURE_OFF_IOUT,				-1000,			1000,			0,			0,			ACCESS_LEVEL1_READ | ACCESS_LEVEL1_WRITE,		SAVE_ENABLE,		CallbackCalibration},
	{MEASURE_OFF_PT100,				-1000,			1000,			0,			0,			ACCESS_LEVEL1_READ | ACCESS_LEVEL1_WRITE,		SAVE_ENABLE,		CallbackCalibration},
	{MEASURE_OFF_NTC,				-1000,			1000,			0,			0,			ACCESS_LEVEL1_READ | ACCESS_LEVEL1_WRITE,		SAVE_ENABLE,		CallbackCalibration},
	{MEASURE_OFF_VBAT,				-1000,			1000,			0,			0,			ACCESS_LEVEL1_READ | ACCESS_LEVEL1_WRITE,		SAVE_ENABLE,		CallbackCalibration},
	{MEASURE_BLANK_10,				-32000,			32000,			0,			0,			ACCESS_LEVEL1_READ | ACCESS_LEVEL1_WRITE,		SAVE_ENABLE,		CallbackCalibration},
	{MEASURE_BLANK_11,				-32000,			32000,			0,			0,			ACCESS_LEVEL1_READ | ACCESS_LEVEL1_WRITE,		SAVE_ENABLE,		CallbackCalibration},
	{MEASURE_BLANK_12,				-32000,			32000,			0,			-2,			ACCESS_LEVEL1_READ | ACCESS_LEVEL1_WRITE,		SAVE_ENABLE,		CallbackCalibration},
	{MEASURE_BLANK_13,				-32000,			32000,			0,			-2,			ACCESS_LEVEL1_READ | ACCESS_LEVEL1_WRITE,		SAVE_ENABLE,		CallbackCalibration},
	{MEASURE_BLANK_14,				-32000,			32000,			0,			-2,			ACCESS_LEVEL1_READ | ACCESS_LEVEL1_WRITE,		SAVE_ENABLE,		CallbackCalibration},
	{MEASURE_BLANK_15,				-32000,			32000,			0,			-2,			ACCESS_LEVEL1_READ | ACCESS_LEVEL1_WRITE,		SAVE_ENABLE,		CallbackCalibration},
	{MEASURE_BLANK_16,				-32000,			32000,			0,			-2,			ACCESS_LEVEL1_READ | ACCESS_LEVEL1_WRITE,		SAVE_ENABLE,		CallbackCalibration},
	{MEASURE_BLANK_17,				-32000,			32000,			0,			-2,			ACCESS_LEVEL1_READ | ACCESS_LEVEL1_WRITE,		SAVE_ENABLE,		CallbackCalibration},
	{MEASURE_BLANK_18,				-32000,			32000,			0,			-2,			ACCESS_LEVEL1_READ | ACCESS_LEVEL1_WRITE,		SAVE_ENABLE,		CallbackCalibration},
	{MEASURE_BLANK_19,				-32000,			32000,			0,			-2,			ACCESS_LEVEL1_READ | ACCESS_LEVEL1_WRITE,		SAVE_ENABLE,		CallbackCalibration},

	{TEMP_DERATE_NTC,				0,				10000,			2000,		0,			ACCESS_LEVEL1_READ | ACCESS_LEVEL1_WRITE,		SAVE_ENABLE,		CallbackTempControl},
	{TEMP_DERATE_PT100,				0,				10000,			1000,		-2,			ACCESS_LEVEL1_READ | ACCESS_LEVEL1_WRITE,		SAVE_ENABLE,		CallbackTempControl},
	{TEMP_BLANK_3,					0,				10000,			0,			0,			ACCESS_LEVEL1_READ | ACCESS_LEVEL1_WRITE,		SAVE_ENABLE,		CallbackTempControl},
	{TEMP_BLANK_4,					0,				10000,			0,			0,			ACCESS_LEVEL1_READ | ACCESS_LEVEL1_WRITE,		SAVE_ENABLE,		CallbackTempControl},
	{TEMP_COEFF_1,					0,				10000,			0,			0,			ACCESS_LEVEL1_READ | ACCESS_LEVEL1_WRITE,		SAVE_ENABLE,		CallbackTempControl},
	{TEMP_COEFF_2,					0,				10000,			0,			0,			ACCESS_LEVEL1_READ | ACCESS_LEVEL1_WRITE,		SAVE_ENABLE,		CallbackTempControl},
	{TEMP_PT100_ACT,				0,				1,				0,			0,			ACCESS_LEVEL1_READ | ACCESS_LEVEL1_WRITE,		SAVE_ENABLE,		CallbackTempControl},
	{TEMP_PT100_DVDT,				0,				10,				0,			-2,			ACCESS_LEVEL1_READ | ACCESS_LEVEL1_WRITE,		SAVE_ENABLE,		CallbackTempControl},
	{TEMP_PT100_MAX,				65,				200,			100,		0,			ACCESS_LEVEL1_READ | ACCESS_LEVEL1_WRITE,		SAVE_ENABLE,		CallbackTempControl},
	{TEMP_BLANK_10,					0,				10000,			0,			0,			ACCESS_LEVEL1_READ | ACCESS_LEVEL1_WRITE,		SAVE_ENABLE,		CallbackTempControl},

	{PARALLEL_WORKING,				0,				1,				0,			0,			ACCESS_LEVEL1_READ | ACCESS_LEVEL1_WRITE,		SAVE_ENABLE,		CallbackParallelWorking},
	{PARALLEL_CURRENT_COEFF,		0,			   100,			   3,			0,			ACCESS_LEVEL1_READ | ACCESS_LEVEL1_WRITE,		SAVE_ENABLE,		CallbackUpdateParallelWorkingCoeff},
	{PARALLEL_BLANK_3,				-10,			10,				0,			0,			ACCESS_LEVEL1_READ | ACCESS_LEVEL1_WRITE,		SAVE_ENABLE,		CallbackParallelWorking},
	{PARALLEL_BLANK_4,				-10,			10,				0,			0,			ACCESS_LEVEL1_READ | ACCESS_LEVEL1_WRITE,		SAVE_ENABLE,		CallbackParallelWorking},
	{PARALLEL_BLANK_5,				-10,			10,				0,			0,			ACCESS_LEVEL1_READ | ACCESS_LEVEL1_WRITE,		SAVE_ENABLE,		CallbackParallelWorking},
	{PARALLEL_BLANK_6,				-10,			10,				0,			0,			ACCESS_LEVEL1_READ | ACCESS_LEVEL1_WRITE,		SAVE_ENABLE,		CallbackParallelWorking},
	{PARALLEL_BLANK_7,				-10,			10,				0,			0,			ACCESS_LEVEL1_READ | ACCESS_LEVEL1_WRITE,		SAVE_ENABLE,		CallbackParallelWorking},
	{PARALLEL_BLANK_8,				-10,			10,				0,			0,			ACCESS_LEVEL1_READ | ACCESS_LEVEL1_WRITE,		SAVE_ENABLE,		CallbackParallelWorking},
	{PARALLEL_BLANK_9,				-10,			10,				0,			0,			ACCESS_LEVEL1_READ | ACCESS_LEVEL1_WRITE,		SAVE_ENABLE,		CallbackParallelWorking},
	{PARALLEL_BLANK_10,				-10,			10,				0,			0,			ACCESS_LEVEL1_READ | ACCESS_LEVEL1_WRITE,		SAVE_ENABLE,		CallbackParallelWorking},
	
	{LED_COLOR,						0,				32000,			0,			0,			ACCESS_LEVEL1_READ | ACCESS_LEVEL1_WRITE,		SAVE_DISABLE,		CallbackLEDControl},
	{LED_FLASH_TIME,				0,				8192,			1024,		0,			ACCESS_LEVEL1_READ | ACCESS_LEVEL1_WRITE,		SAVE_DISABLE,		CallbackNull},
	{LED_CONSTANT,					0,				1,				1,			0,			ACCESS_LEVEL1_READ | ACCESS_LEVEL1_WRITE,		SAVE_DISABLE,		CallbackNull},
	{LED_BLINK,						0,				10,				2,			0,			ACCESS_LEVEL1_READ | ACCESS_LEVEL1_WRITE,		SAVE_DISABLE,		CallbackNull},
	{LED_BLANK_5,					-10,			10,				0,			0,			ACCESS_LEVEL1_READ | ACCESS_LEVEL1_WRITE,		SAVE_ENABLE,		CallbackNull},
	{LED_BLANK_6,					-10,			10,				0,			0,			ACCESS_LEVEL1_READ | ACCESS_LEVEL1_WRITE,		SAVE_ENABLE,		CallbackNull},
	{LED_BLANK_7,					-10,			10,				0,			0,			ACCESS_LEVEL1_READ | ACCESS_LEVEL1_WRITE,		SAVE_ENABLE,		CallbackNull},
	{LED_BLANK_8,					-10,			10,				0,			0,			ACCESS_LEVEL1_READ | ACCESS_LEVEL1_WRITE,		SAVE_ENABLE,		CallbackNull},
	{LED_BLANK_9,					-10,			10,				0,			0,			ACCESS_LEVEL1_READ | ACCESS_LEVEL1_WRITE,		SAVE_ENABLE,		CallbackNull},
	{LED_BLANK_10,					-10,			10,				0,			0,			ACCESS_LEVEL1_READ | ACCESS_LEVEL1_WRITE,		SAVE_ENABLE,		CallbackNull},

	{DEVICE_CUSTOMER_NUMBER1,			-32768,			32767,				0,		 	 0,			ACCESS_LEVEL1_READ | ACCESS_LEVEL4_WRITE,		SAVE_ENABLE,		CallbackDeviceUpdate},
	{DEVICE_CUSTOMER_NUMBER2,			-32768,			32767,				0,		 	 0,			ACCESS_LEVEL1_READ | ACCESS_LEVEL4_WRITE,		SAVE_ENABLE,		CallbackDeviceUpdate},
	{DEVICE_CUSTOMER_NUMBER3,			-32768,			32767,				0,		 	 0,			ACCESS_LEVEL1_READ | ACCESS_LEVEL4_WRITE,		SAVE_ENABLE,		CallbackDeviceUpdate},
	{DEVICE_CUSTOMER_NUMBER4,			-32768,			32767,				0,		 	 0,			ACCESS_LEVEL1_READ | ACCESS_LEVEL4_WRITE,		SAVE_ENABLE,		CallbackDeviceUpdate},
	{DEVICE_CUSTOMER_NUMBER5,			-32768,			32767,				0,		 	 0,			ACCESS_LEVEL1_READ | ACCESS_LEVEL4_WRITE,		SAVE_ENABLE,		CallbackDeviceUpdate},
	{DEVICE_CUSTOMER_TEXT1,				-32768,			32767,				12336,	 	 0,			ACCESS_LEVEL1_READ | ACCESS_LEVEL4_WRITE,		SAVE_ENABLE,		CallbackDeviceUpdate},
	{DEVICE_CUSTOMER_TEXT2,				-32768,			32767,				12336,		 0,			ACCESS_LEVEL1_READ | ACCESS_LEVEL4_WRITE,		SAVE_ENABLE,		CallbackDeviceUpdate},
	{DEVICE_CUSTOMER_TEXT3,				-32768,			32767,				12336,		 0,			ACCESS_LEVEL1_READ | ACCESS_LEVEL4_WRITE,		SAVE_ENABLE,		CallbackDeviceUpdate},
	{DEVICE_CUSTOMER_TEXT4,				-32768,			32767,				12336,		 0,			ACCESS_LEVEL1_READ | ACCESS_LEVEL4_WRITE,		SAVE_ENABLE,		CallbackDeviceUpdate},
	{DEVICE_CUSTOMER_TEXT5,				-32768,			32767,				12336,		 0,			ACCESS_LEVEL1_READ | ACCESS_LEVEL4_WRITE,		SAVE_ENABLE,		CallbackDeviceUpdate},
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
	{ERR_BLANK_11,			0,			1,				0,		 0,			ACCESS_LEVEL1_READ | ACCESS_LEVEL4_WRITE,		SAVE_DISABLE,		CallbackNull},
	{ERR_BLANK_12,			0,			1,				0,		 0,			ACCESS_LEVEL1_READ | ACCESS_LEVEL4_WRITE,		SAVE_DISABLE,		CallbackNull},

	{WARN_FLAG,				-32767,		32767,			0,		 0,			ACCESS_LEVEL1_READ | ACCESS_LEVEL4_WRITE,		SAVE_DISABLE,		CallbackNull},
	{WARN_ADC,				0,			1,				0,		 0,			ACCESS_LEVEL1_READ | ACCESS_LEVEL4_WRITE,		SAVE_DISABLE,		CallbackNull},
	{WARN_OVER_TEMP,		0,			1,				0,		 0,			ACCESS_LEVEL1_READ | ACCESS_LEVEL4_WRITE,		SAVE_DISABLE,		CallbackNull},
	{WARN_PT100_CONN,		0,			1,				0,		 0,			ACCESS_LEVEL1_READ | ACCESS_LEVEL4_WRITE,		SAVE_DISABLE,		CallbackNull},
	{WARN_PT100_TEMP,		0,			1,				0,		 0,			ACCESS_LEVEL1_READ | ACCESS_LEVEL4_WRITE,		SAVE_DISABLE,		CallbackNull},
	{WARN_MAX_CURR,			0,			1,				0,		 0,			ACCESS_LEVEL1_READ | ACCESS_LEVEL4_WRITE,		SAVE_DISABLE,		CallbackNull},
	{WARN_BATT_VOLT,		0,			1,				0,		 0,			ACCESS_LEVEL1_READ | ACCESS_LEVEL4_WRITE,		SAVE_DISABLE,		CallbackNull},
	{WARN_BLANK_8,			0,			1,				0,		 0,			ACCESS_LEVEL1_READ | ACCESS_LEVEL4_WRITE,		SAVE_DISABLE,		CallbackNull},
	{WARN_BLANK_9,			0,			1,				0,		 0,			ACCESS_LEVEL1_READ | ACCESS_LEVEL4_WRITE,		SAVE_DISABLE,		CallbackNull},
	{WARN_BLANK_10,			0,			1,				0,		 0,			ACCESS_LEVEL1_READ | ACCESS_LEVEL4_WRITE,		SAVE_DISABLE,		CallbackNull},

	{DEBUG_FLAG,			-32768,		32767,			0,		 0,			ACCESS_LEVEL1_READ | ACCESS_LEVEL4_WRITE,		SAVE_DISABLE,		CallbackNull},
	{DEBUG_MODE,			0,			32767,			0,		 0,			ACCESS_LEVEL1_READ | ACCESS_LEVEL4_WRITE,		SAVE_DISABLE,		CallbackNull},
	{DEBUG_TAG,				-32768,		32767,			0,		 0,			ACCESS_LEVEL1_READ | ACCESS_LEVEL4_WRITE,		SAVE_DISABLE,		CallbackSaveTag},
	{DEBUG_RETURN_FACTORY,	0,			1,				0,		 0,			ACCESS_LEVEL1_READ | ACCESS_LEVEL4_WRITE,		SAVE_DISABLE,		CallbackFactoryReset},
	{DEBUG_DERATE,			0,			1,				1,		 0,			ACCESS_LEVEL1_READ | ACCESS_LEVEL4_WRITE,		SAVE_ENABLE,		CallbackNull},
	{DEBUG_BLANK_6,			-32768,		32767,			0,		 0,			ACCESS_LEVEL1_READ | ACCESS_LEVEL4_WRITE,		SAVE_DISABLE,		CallbackNull},
	{DEBUG_BLANK_7,			-32768,		32767,			0,		 0,			ACCESS_LEVEL1_READ | ACCESS_LEVEL4_WRITE,		SAVE_DISABLE,		CallbackNull},
	{DEBUG_BLANK_8,			-32768,		32767,			0,		 0,			ACCESS_LEVEL1_READ | ACCESS_LEVEL4_WRITE,		SAVE_DISABLE,		CallbackNull},
	{GENERAL_DYNAMIC_PASS_TYPE, -32768,	32767,			0,		 0,			ACCESS_LEVEL1_READ | ACCESS_LEVEL4_WRITE,		SAVE_DISABLE,		CallbackDynamicPass},
	{DEBUG_BLANK_10,		-32768,		32767,			0,		 0,			ACCESS_LEVEL1_READ | ACCESS_LEVEL4_WRITE,		SAVE_DISABLE,		CallbackNull},
};
