alper-bozcal/75W_XDPS/Firmware/DBC2-90W/Core/Src/gpio.c

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

/* Includes ------------------------------------------------------------------*/
#include "gpio.h"

/* USER CODE BEGIN 0 */
#include "main.h"
/* USER CODE END 0 */

/*----------------------------------------------------------------------------*/
/* Configure GPIO                                                             */
/*----------------------------------------------------------------------------*/
/** Configure pins as
        * Analog
        * Input
        * Output
        * EVENT_OUT
        * EXTI
        * Free pins are configured automatically as Analog (this feature is enabled through
        * the Code Generation settings)
*/
void MX_GPIO_Init(void)
{

  GPIO_InitTypeDef GPIO_InitStruct = {0};

  /* GPIO Ports Clock Enable */
  __HAL_RCC_GPIOC_CLK_ENABLE();
  __HAL_RCC_GPIOF_CLK_ENABLE();
  __HAL_RCC_GPIOA_CLK_ENABLE();
  __HAL_RCC_GPIOB_CLK_ENABLE();

  /*Configure GPIO pin Output Level */
  HAL_GPIO_WritePin(OUTPUT_HEALTY_GPIO_Port, OUTPUT_HEALTY_Pin, GPIO_PIN_RESET);

  /*Configure GPIO pin Output Level */
  HAL_GPIO_WritePin(GPIOA, RELAY_OP_Pin|OVER_VOLT_Pin, GPIO_PIN_RESET);

  /*Configure GPIO pin Output Level */
  HAL_GPIO_WritePin(GPIOB, GPIO_PIN_11|LED_G_Pin|LED_B_Pin|LED_R_Pin
                          |NTC_ACTIVE_Pin, GPIO_PIN_RESET);

  /*Configure GPIO pin : OUTPUT_HEALTY_Pin */
  GPIO_InitStruct.Pin = OUTPUT_HEALTY_Pin;
  GPIO_InitStruct.Mode = GPIO_MODE_OUTPUT_PP;
  GPIO_InitStruct.Pull = GPIO_PULLDOWN;
  GPIO_InitStruct.Speed = GPIO_SPEED_FREQ_LOW;
  HAL_GPIO_Init(OUTPUT_HEALTY_GPIO_Port, &GPIO_InitStruct);

  /*Configure GPIO pins : PC14 PC15 */
  GPIO_InitStruct.Pin = GPIO_PIN_14|GPIO_PIN_15;
  GPIO_InitStruct.Mode = GPIO_MODE_ANALOG;
  GPIO_InitStruct.Pull = GPIO_NOPULL;
  HAL_GPIO_Init(GPIOC, &GPIO_InitStruct);

  /*Configure GPIO pins : PF0 PF1 */
  GPIO_InitStruct.Pin = GPIO_PIN_0|GPIO_PIN_1;
  GPIO_InitStruct.Mode = GPIO_MODE_ANALOG;
  GPIO_InitStruct.Pull = GPIO_NOPULL;
  HAL_GPIO_Init(GPIOF, &GPIO_InitStruct);

  /*Configure GPIO pin : RELAY_OP_Pin */
  GPIO_InitStruct.Pin = RELAY_OP_Pin;
  GPIO_InitStruct.Mode = GPIO_MODE_OUTPUT_PP;
  GPIO_InitStruct.Pull = GPIO_NOPULL;
  GPIO_InitStruct.Speed = GPIO_SPEED_FREQ_LOW;
  HAL_GPIO_Init(RELAY_OP_GPIO_Port, &GPIO_InitStruct);

  /*Configure GPIO pin : BOOST_INP_Pin */
  GPIO_InitStruct.Pin = BOOST_INP_Pin;
  GPIO_InitStruct.Mode = GPIO_MODE_IT_RISING_FALLING;
  GPIO_InitStruct.Pull = GPIO_NOPULL;
  HAL_GPIO_Init(BOOST_INP_GPIO_Port, &GPIO_InitStruct);

  /*Configure GPIO pins : PA6 PA7 PA8 PA9
                           PA10 */
  GPIO_InitStruct.Pin = GPIO_PIN_6|GPIO_PIN_7|GPIO_PIN_8|GPIO_PIN_9
                          |GPIO_PIN_10;
  GPIO_InitStruct.Mode = GPIO_MODE_ANALOG;
  GPIO_InitStruct.Pull = GPIO_NOPULL;
  HAL_GPIO_Init(GPIOA, &GPIO_InitStruct);

  /*Configure GPIO pins : PB2 PB12 PB13 PB14
                           PB15 */
  GPIO_InitStruct.Pin = GPIO_PIN_2|GPIO_PIN_12|GPIO_PIN_13|GPIO_PIN_14
                          |GPIO_PIN_15;
  GPIO_InitStruct.Mode = GPIO_MODE_ANALOG;
  GPIO_InitStruct.Pull = GPIO_NOPULL;
  HAL_GPIO_Init(GPIOB, &GPIO_InitStruct);

  /*Configure GPIO pins : PB11 LED_G_Pin LED_B_Pin LED_R_Pin
                           NTC_ACTIVE_Pin */
  GPIO_InitStruct.Pin = GPIO_PIN_11|LED_G_Pin|LED_B_Pin|LED_R_Pin
                          |NTC_ACTIVE_Pin;
  GPIO_InitStruct.Mode = GPIO_MODE_OUTPUT_PP;
  GPIO_InitStruct.Pull = GPIO_NOPULL;
  GPIO_InitStruct.Speed = GPIO_SPEED_FREQ_LOW;
  HAL_GPIO_Init(GPIOB, &GPIO_InitStruct);

  /*Configure GPIO pin : OVER_VOLT_Pin */
  GPIO_InitStruct.Pin = OVER_VOLT_Pin;
  GPIO_InitStruct.Mode = GPIO_MODE_OUTPUT_PP;
  GPIO_InitStruct.Pull = GPIO_PULLUP;
  GPIO_InitStruct.Speed = GPIO_SPEED_FREQ_LOW;
  HAL_GPIO_Init(OVER_VOLT_GPIO_Port, &GPIO_InitStruct);

  /*Configure GPIO pin : JTDO_Pin */
  GPIO_InitStruct.Pin = JTDO_Pin;
  GPIO_InitStruct.Mode = GPIO_MODE_INPUT;
  GPIO_InitStruct.Pull = GPIO_NOPULL;
  HAL_GPIO_Init(JTDO_GPIO_Port, &GPIO_InitStruct);

  /* EXTI interrupt init*/
  HAL_NVIC_SetPriority(EXTI4_15_IRQn, 2, 0);
  HAL_NVIC_EnableIRQ(EXTI4_15_IRQn);

}

/* USER CODE BEGIN 2 */
/* MX_GPIO_Init sonrasi cagrilir: CubeMX'in ezdigi karta ozel pin ayarlari */
void MX_GPIO_UserInit(void)
{
#ifdef PCB_VERSION_V7
  // V7'de OUTPUT_HEALTY PA6'da; MX_GPIO_Init PA6'yi analog yapiyor, cikisa geri al
  GPIO_InitTypeDef GPIO_InitStruct = {0};
  HAL_GPIO_WritePin(OUTPUT_HEALTY_GPIO_Port, OUTPUT_HEALTY_Pin, GPIO_PIN_RESET);
  GPIO_InitStruct.Pin = OUTPUT_HEALTY_Pin;
  GPIO_InitStruct.Mode = GPIO_MODE_OUTPUT_PP;
  GPIO_InitStruct.Pull = GPIO_PULLDOWN;
  GPIO_InitStruct.Speed = GPIO_SPEED_FREQ_LOW;
  HAL_GPIO_Init(OUTPUT_HEALTY_GPIO_Port, &GPIO_InitStruct);
#endif
}
/* USER CODE END 2 */
