alper-bozcal/75W_XDPS/Firmware/Common/Peripherals/J1939I/IJ1939Config.h

/*
 * j1939-config.h
 *
 *  Created on: Sep 30, 2022
 *      Author: eren.akyol
 */

#ifndef J1939_CONFIG_H_
#define J1939_CONFIG_H_

#include "main.h"
#include "can.h"
#include "assert.h"

#define J1939_SPECIFIC_PACKET_NUMBER		0  // Motora ozgu maksimum spesifik mesajlarin toplami
#define J1939_STANDART_PACKET_NUMBER		3  // Common olarak eklenen paket sayisi

#endif /* J1939_CONFIG_H_ */
