alper-bozcal/75W_XDPS/Firmware/Common/Peripherals/J1939Module/version.h

/*
 * version.h
 *
 *  Created on: Sep 30, 2022
 *      Author: eren.akyol
 */

#ifndef VERSION_H_
#define VERSION_H_



#define SOFTWARE_VERSION	0003


/*V0002*/
//f4 vb  islemciler ile uyumlu olmasi icin can structeri fonksiyonlara parametrik olarak eklendi.

/*V0003*/
//AMF-L ürünü ile CAN1 ve CAN2 donanımları denendi. 
//Nesne yapısı test edildi. Bir veya birden fazla CAN tanımlı stm32 tabanlı işlemcilerde çalışır hale getirildi.





#endif /* VERSION_H_ */
